trissim/OpenMFD/docs/source/api/export.rst

Export Module
=============

The export module provides file export and conversion functionality.

.. currentmodule:: openmfd.export

Configuration
-------------

.. automodule:: openmfd.export.config
   :members:
   :undoc-members:
   :show-inheritance:

SCAD Export
-----------

.. automodule:: openmfd.export.scad
   :members:
   :undoc-members:
   :show-inheritance:

DXF Export
----------

.. automodule:: openmfd.export.dxf
   :members:
   :undoc-members:
   :show-inheritance:

STL Export
----------

.. automodule:: openmfd.export.stl
   :members:
   :undoc-members:
   :show-inheritance:

File Naming
-----------

.. automodule:: openmfd.export.naming
   :members:
   :undoc-members:
   :show-inheritance:

Exporter
--------

.. automodule:: openmfd.export.exporter
   :members:
   :undoc-members:
   :show-inheritance:
