trissim/OpenMFD/docs/source/api/geometry.rst

Geometry Module
===============

The geometry module provides primitives and patterns for creating microfluidic device components.

.. currentmodule:: openmfd.geometry

Types and Measurements
----------------------

.. automodule:: openmfd.geometry.types
   :members:
   :undoc-members:
   :show-inheritance:

Primitives
----------

.. automodule:: openmfd.geometry.primitives
   :members:
   :undoc-members:
   :show-inheritance:

Wells
-----

.. automodule:: openmfd.geometry.wells
   :members:
   :undoc-members:
   :show-inheritance:

Channels
--------

.. automodule:: openmfd.geometry.channels
   :members:
   :undoc-members:
   :show-inheritance:

Chambers
--------

.. automodule:: openmfd.geometry.chambers
   :members:
   :undoc-members:
   :show-inheritance:

Positioning
-----------

.. automodule:: openmfd.geometry.positioning
   :members:
   :undoc-members:
   :show-inheritance:
