trissim/OpenMFD/docs/source/examples/custom_device.rst

Custom Devices
==============

Examples of custom device designs.

(Content to be added)
