trissim/OpenMFD/docs/source/examples/gradient_device.rst

Gradient Devices
================

Examples of gradient generation devices.

(Content to be added)
