trissim/OpenMFD/docs/source/examples/multi_well_plate.rst

Multi-Well Plates
=================

Examples of multi-well plate devices.

(Content to be added)
