trissim/OpenMFD/docs/source/examples/two_compartment.rst

Two-Compartment Devices
=======================

Examples of two-compartment microfluidic devices.

(Content to be added)
