trissim/OpenMFD/docs/source/api/index.rst

API Reference
=============

Complete API reference for OpenMFD.

.. toctree::
   :maxdepth: 2

   geometry
   devices
   export
   core
   utils

Modules
-------

.. autosummary::
   :toctree: _autosummary
   :recursive:

   openmfd.geometry
   openmfd.devices
   openmfd.export
   openmfd.core
   openmfd.utils
