trissim/OpenMFD/papers/mfd_platform/paper.md

# Manuscript source moved

The sole editable manuscript is [manuscript.md](manuscript.md). This historical
path is retained as a pointer; edit the canonical source, not this file.

Read the latest paired and combined documents under [current](current/), or see
[the paper guide](README.md) for building and preserved history.
