trissim/OpenMFD/papers/mfd_platform/prior_art_table.md

# Table 1. Prior art: multiscale microfluidic fabrication strategies (microfeatures + tall wells)

| Approach | Micro-scale features | Macro wells / tall structures | Plate / automation compatibility | What it typically costs you | Representative refs |
|---|---|---|---|---|---|
| Conventional PDMS soft lithography + manual punching | SU-8 photolithography (µm-scale channels) | Biopsy punch after casting | Limited by manual post-processing; punching becomes the throughput bottleneck | Manual labor, variability, edge defects, hard to scale to 96-well | (baseline approach; see e.g., Taylor et al., 2005) |
| CO₂ laser micromachining of PDMS | Maskless laser ablation; practical widths generally >100 µm | Laser-ablated reservoirs/wells/channels | Serial process; not ideal for dense plate arrays | Limited resolution and non-ideal cross-sections; thermal artifacts | Holle et al., 2007 |
| Micro–macro hybrid master via milling + hot embossing | Hot embossing for microfeatures | PMMA milled macrostructures (mm-scale) | Can replicate PDMS masters in quantity (not inherently plate-format) | Requires hot embosser + milling; multi-master workflow | Park et al., 2010 |
| Thick SU-8 molding + photolithography (single material) | Photolithography on molded SU-8 surface | Millimeter structures molded from 3D-printed master via PDMS mold | Demonstrated as micro-to-mm “seamless” structures (not plate workflows) | Surface roughness can degrade lithography; multi-step SU-8 handling | Tamura & Suzuki, 2019 |
| Direct 3D printing of PDMS onto photolithographic master (“printed soft lithography”) | Photolithographic master for microchannels | Printed PDMS walls/compartments | Removes punching for certain architectures; not inherently microtiter plate-format | Requires PDMS-printing hardware (bioprinter/extrusion) and ink tuning | Kajtez et al., 2020 |
| Aligned SLA printing onto patterned chips | SU-8 lithography on diced chips | SLA-printed micro/macro 3D features | Chip-scale alignment; not wafer-scale or plate-scale workflows | Requires dicing + alignment fixtures; first-layer overcure effects | Pan et al., 2022 |
| 3D-printed inserts bonded to SU-8 (lock-and-key) | SU-8 photolithography for microfeatures | Tall 3D-printed inserts + epoxy bonding | Works for open reservoirs; scaling limited by manual insert handling | Metal printing cost/availability; manual placement effort | Ristola et al., 2019 |
| Hard-plastic microtiter microfluidic plates (industrial) | Hot-embossed microchannels in COC | CNC-milled wells/compartments + fusion bonding | ANSI/SLAS compatible; automation-friendly | Requires specialized tooling/processes; not typical academic fab | Moll et al., 2024 |
| Commercial microfluidic titer plates (proprietary) | Proprietary | Proprietary | High-throughput, plate footprint | Limited design freedom; cost; opaque fab details | Spijkers et al., 2021 (OrganoPlate) |
| **This work: wafer-bonded resin well inserts + SU-8 microfeatures (with OpenMFD design rules)** | SU-8/SUEX photolithography for µm-scale microfeatures | Resin-printed well inserts adhesively bonded to wafer mold; wells formed during casting (no punching) | ANSI/SLAS footprint; demonstrated with HCS imaging + autofocus (Opera Phenix, ImageXpress) | Requires reliable bonding workflow + final mold insulation (e.g., parylene coating) | **This work** |
