trissim/OpenMFD/papers/mfd_platform/supplementary/Supplementary_Table_S1_pin_z_variability.md

# Supplementary Table S1. Resin-insert pin-height variation across a 96-position array

Each pin height was measured individually with a micrometer across one 8 × 12 resin-insert array (rows A-H, columns 1-12; *n* = 96). Values are reported in millimeters (mm) and as deviations from the mean in micrometers (µm).

- Mean height: **5.551 mm**
- Standard deviation: **26.7 µm**
- Minimum / maximum height: **5.483 mm** (H12) / **5.599 mm** (A3, A4, and A6)
- Difference between tallest and shortest pins: **116 µm**

## S1A. Measured pin heights (mm)

| Row | 1 | 2 | 3 | 4 | 5 | 6 | 7 | 8 | 9 | 10 | 11 | 12 |
|---|---|---|---|---|---|---|---|---|---|---|---|---|
| A | 5.567 | 5.588 | 5.599 | 5.599 | 5.591 | 5.599 | 5.598 | 5.598 | 5.597 | 5.596 | 5.581 | 5.562 |
| B | 5.557 | 5.588 | 5.591 | 5.591 | 5.592 | 5.588 | 5.593 | 5.592 | 5.592 | 5.591 | 5.587 | 5.562 |
| C | 5.555 | 5.556 | 5.555 | 5.563 | 5.563 | 5.556 | 5.560 | 5.557 | 5.560 | 5.560 | 5.558 | 5.555 |
| D | 5.549 | 5.552 | 5.552 | 5.555 | 5.552 | 5.552 | 5.549 | 5.552 | 5.549 | 5.552 | 5.550 | 5.545 |
| E | 5.543 | 5.546 | 5.549 | 5.550 | 5.547 | 5.547 | 5.548 | 5.544 | 5.544 | 5.543 | 5.536 | 5.532 |
| F | 5.522 | 5.531 | 5.548 | 5.544 | 5.540 | 5.540 | 5.543 | 5.542 | 5.536 | 5.531 | 5.528 | 5.522 |
| G | 5.519 | 5.528 | 5.542 | 5.543 | 5.536 | 5.535 | 5.538 | 5.538 | 5.532 | 5.529 | 5.521 | 5.501 |
| H | 5.499 | 5.516 | 5.525 | 5.525 | 5.521 | 5.520 | 5.529 | 5.517 | 5.517 | 5.503 | 5.495 | 5.483 |

## S1B. Deviation from mean (µm)

| Row | 1 | 2 | 3 | 4 | 5 | 6 | 7 | 8 | 9 | 10 | 11 | 12 |
|---|---|---|---|---|---|---|---|---|---|---|---|---|
| A | +16.2 | +37.2 | +48.2 | +48.2 | +40.2 | +48.2 | +47.2 | +47.2 | +46.2 | +45.2 | +30.2 | +11.2 |
| B | +6.2 | +37.2 | +40.2 | +40.2 | +41.2 | +37.2 | +42.2 | +41.2 | +41.2 | +40.2 | +36.2 | +11.2 |
| C | +4.2 | +5.2 | +4.2 | +12.2 | +12.2 | +5.2 | +9.2 | +6.2 | +9.2 | +9.2 | +7.2 | +4.2 |
| D | -1.8 | +1.2 | +1.2 | +4.2 | +1.2 | +1.2 | -1.8 | +1.2 | -1.8 | +1.2 | -0.8 | -5.8 |
| E | -7.8 | -4.8 | -1.8 | -0.8 | -3.8 | -3.8 | -2.8 | -6.8 | -6.8 | -7.8 | -14.8 | -18.8 |
| F | -28.8 | -19.8 | -2.8 | -6.8 | -10.8 | -10.8 | -7.8 | -8.8 | -14.8 | -19.8 | -22.8 | -28.8 |
| G | -31.8 | -22.8 | -8.8 | -7.8 | -14.8 | -15.8 | -12.8 | -12.8 | -18.8 | -21.8 | -29.8 | -49.8 |
| H | -51.8 | -34.8 | -25.8 | -25.8 | -29.8 | -30.8 | -21.8 | -33.8 | -33.8 | -47.8 | -55.8 | -67.8 |
