trissim/OpenMFD/papers/mfd_platform/figures/final_drop/Fig3_bonding_fixture/draft_figure.odp

Inserts are printed in position aligned with the wafer and then covered in slow setting epoxy

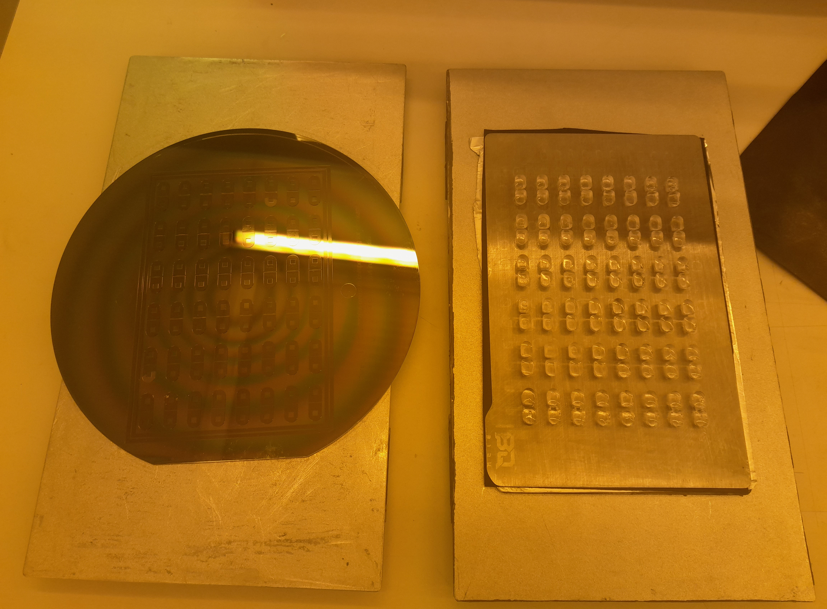
[picture p5: figure]

Aligned and Clamped Assembly

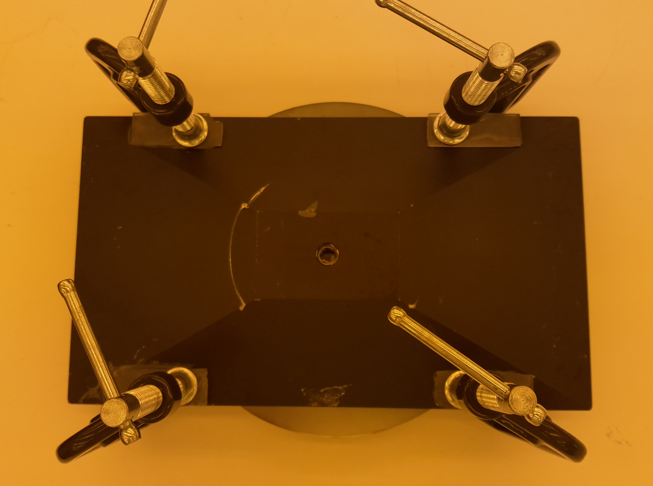
[picture p6: figure]

Sealing the glue between the wafer and inserts allows excess epoxy to be washed by immersion in acetone

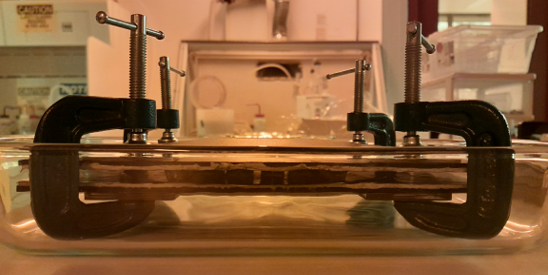
[picture p7: figure]
