trissim/OpenMFD/papers/mfd_platform/figures/final_drop/Fig4_mold_casts_package/draft_figure.odp

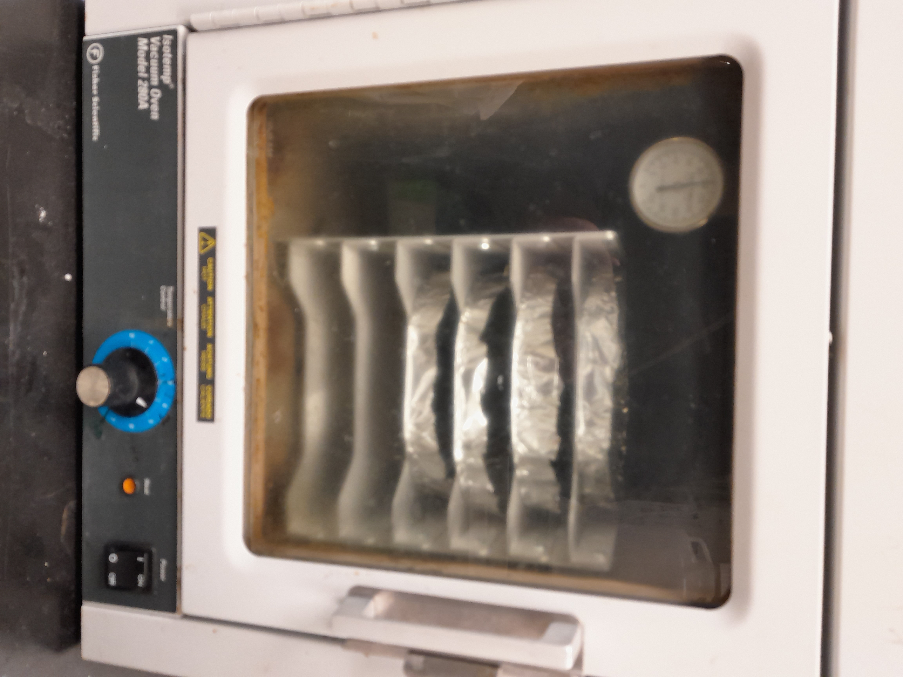
[picture p8: figure]
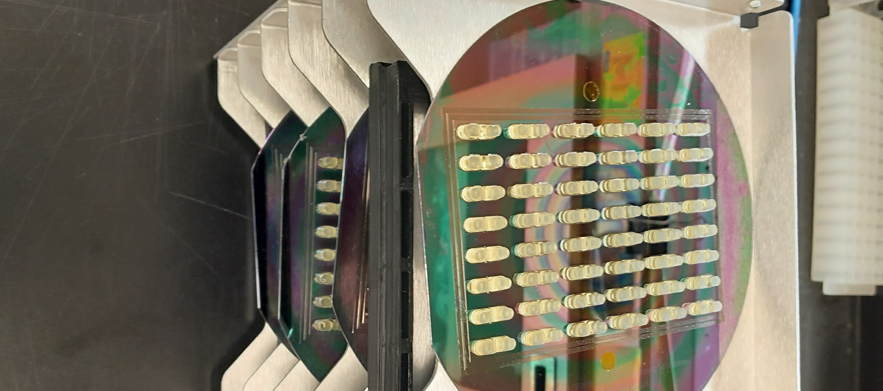
[picture p9: figure]
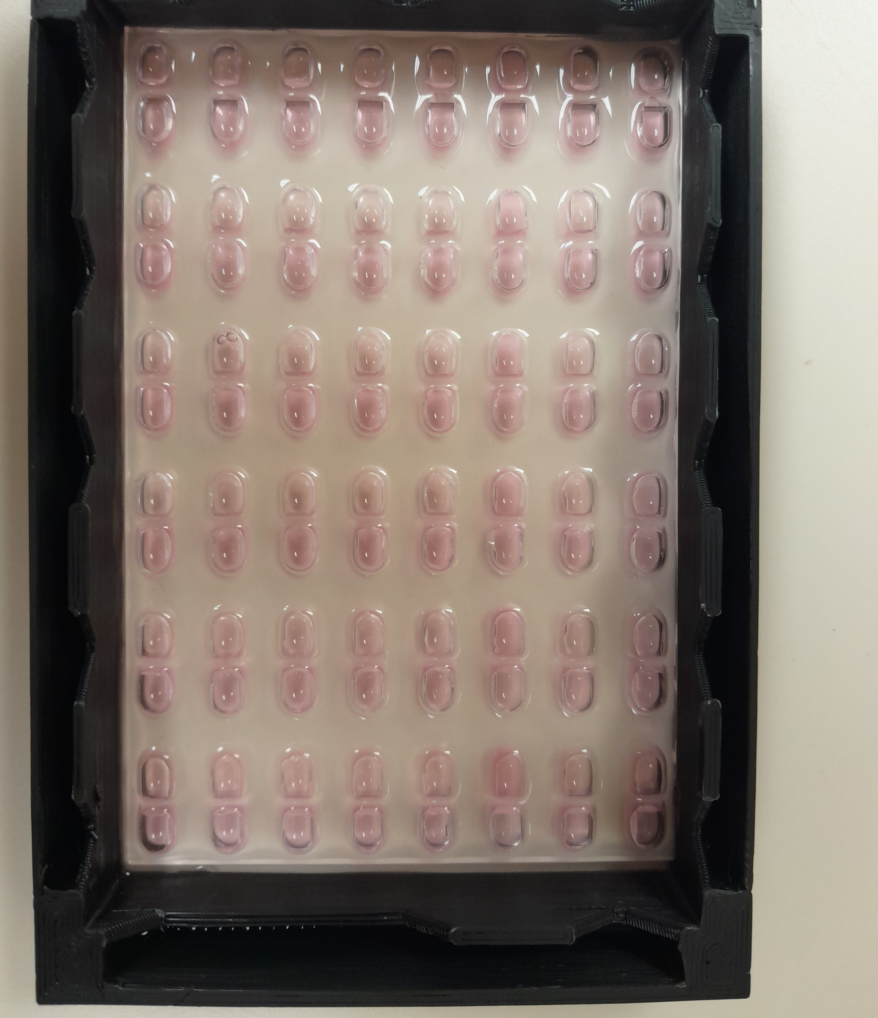
[picture p10: figure]

Unified mold and custom rack for parallel fabrication of devices

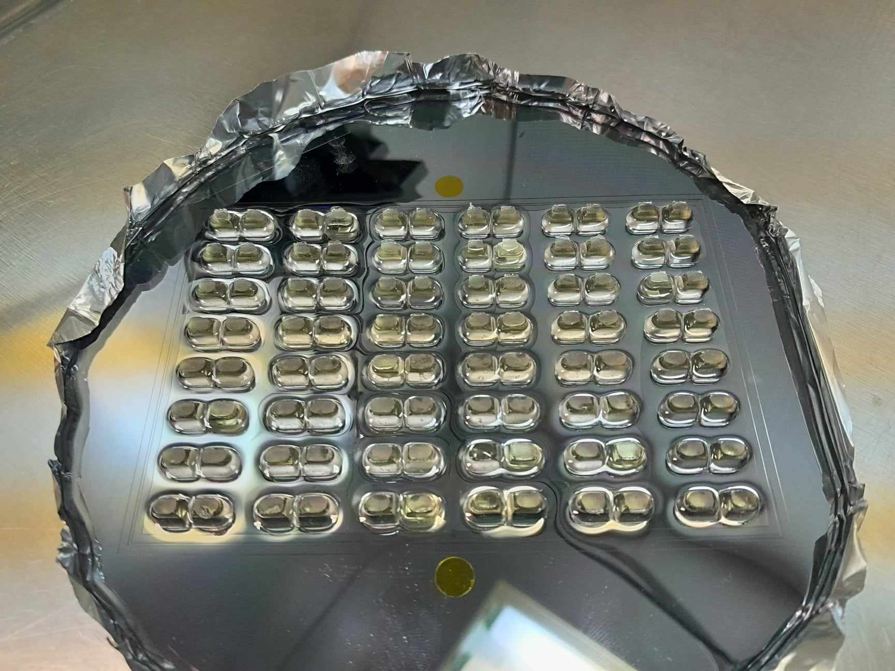
[picture p11: figure]

Assembly with 3D printed plates and glue

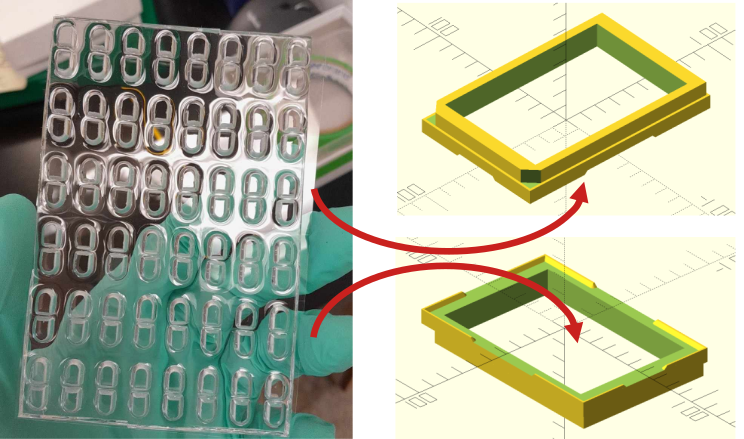
[picture p12: figure]
