trissim/OpenMFD/papers/mfd_platform/figures/final_drop/Fig6_generalizability/draft_figure.odp

## Other High-throughput Devices for Various Assays

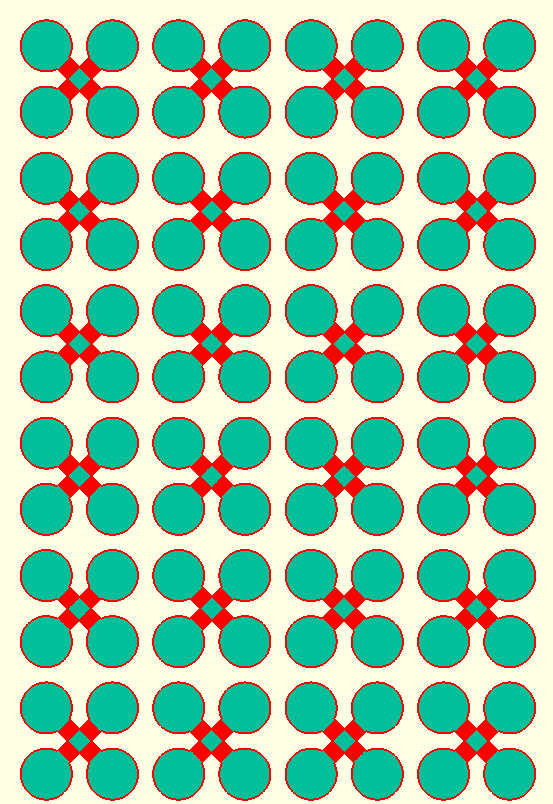
[picture p13: figure]

Myelination Assay

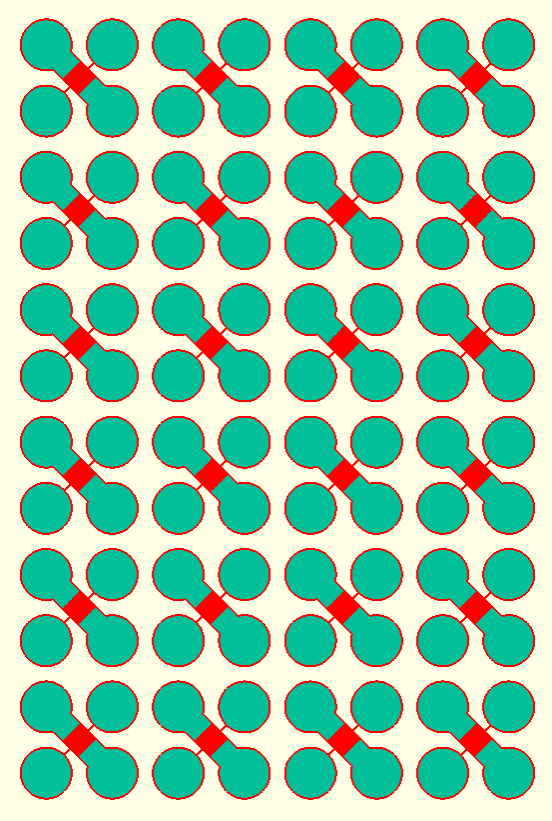
[picture p14: figure]

Axon Guidance Assay

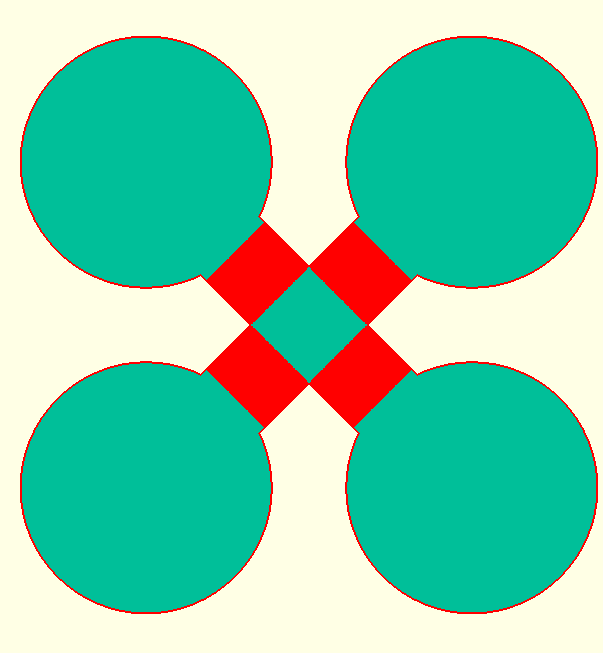
[picture p15: figure]
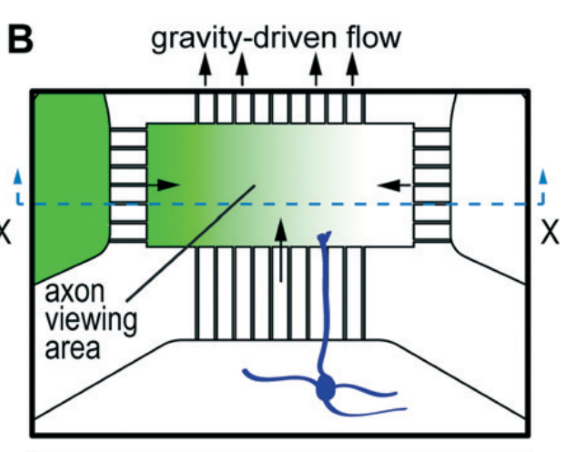
[picture p16: figure]
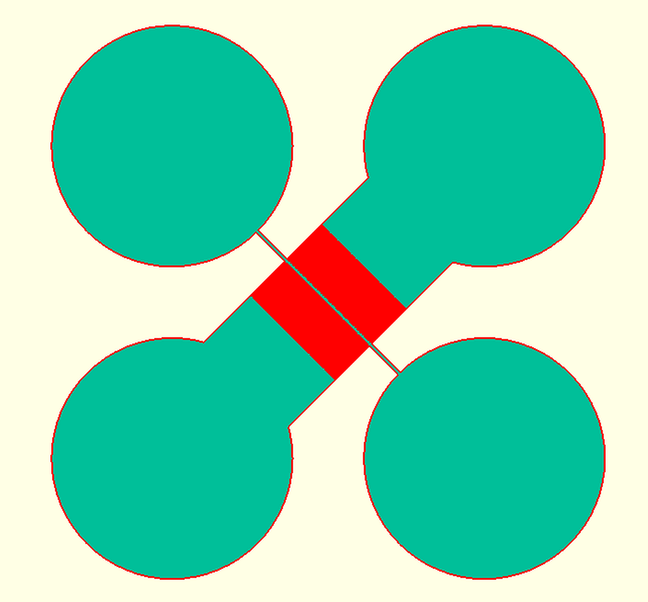
[picture p17: figure]
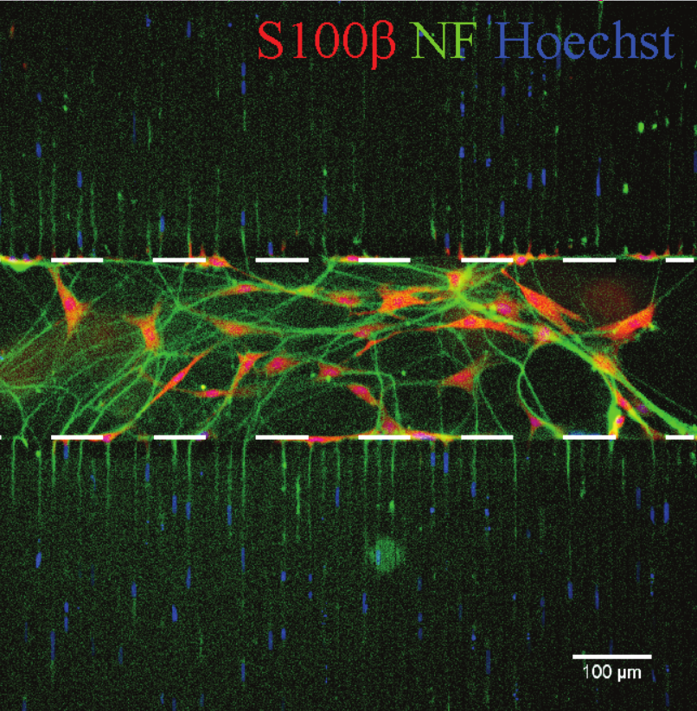
[picture p18: figure]

Oligo

Inlet

Axons

Myelin

Oligo

Outlet

Waste /

Outlet

Axons

Cue 2

Cue 1

Cell

Bodies

Cell

Bodies

<number>

Notes: - Once 96-well axotomy works → can make high-throughput device of any layouts - Recreation of published layout but transformed into high throughput version - Example of myelination assay - Example of Axon guidance assay
