trissim/OpenMFD/papers/mfd_platform/figures/final_drop/Supp_FigS1_noLP360/draft_figure.odp

SUEX 200 without 360nm Long-Pass Filter

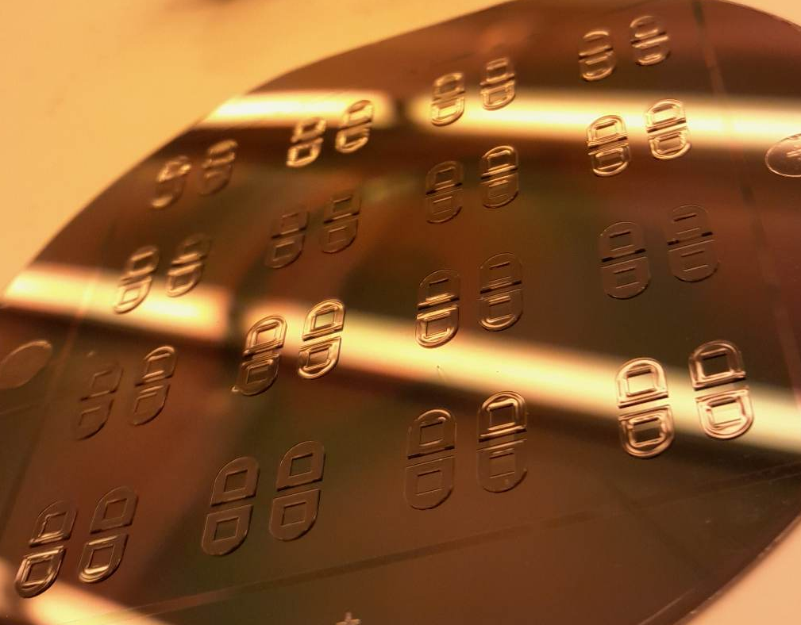
[picture p19: figure]

SUEX 200 with 360nm Long-Pass Filter

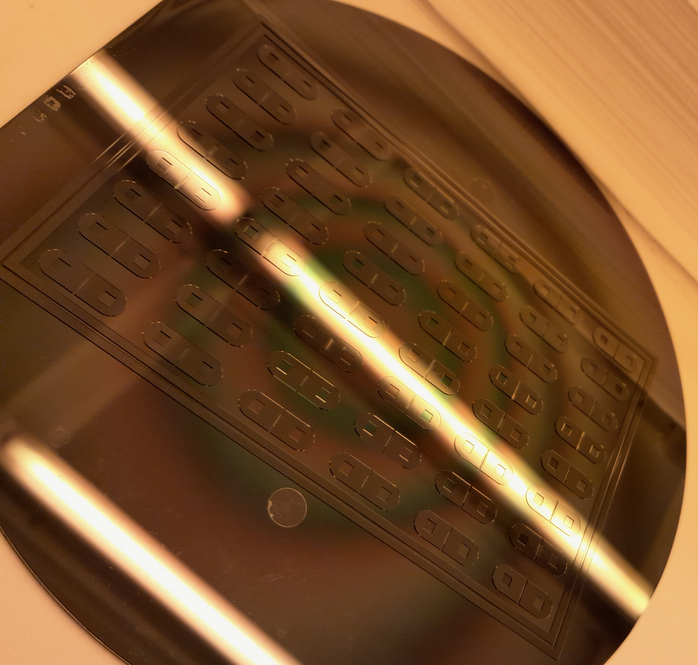
[picture p20: figure]
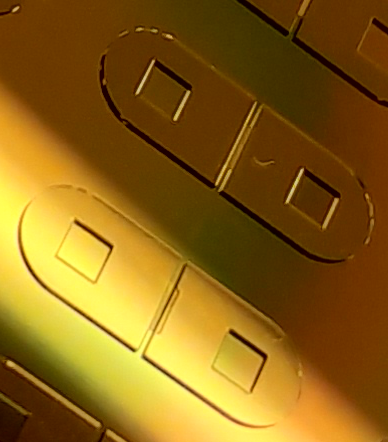
[picture p21: figure]
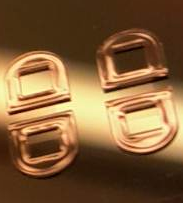
[picture p22: figure]
