trissim/OpenMFD/papers/mfd_platform/figures/rendered/mold_casts_package.pdf

# Post-mold device replication and assembly

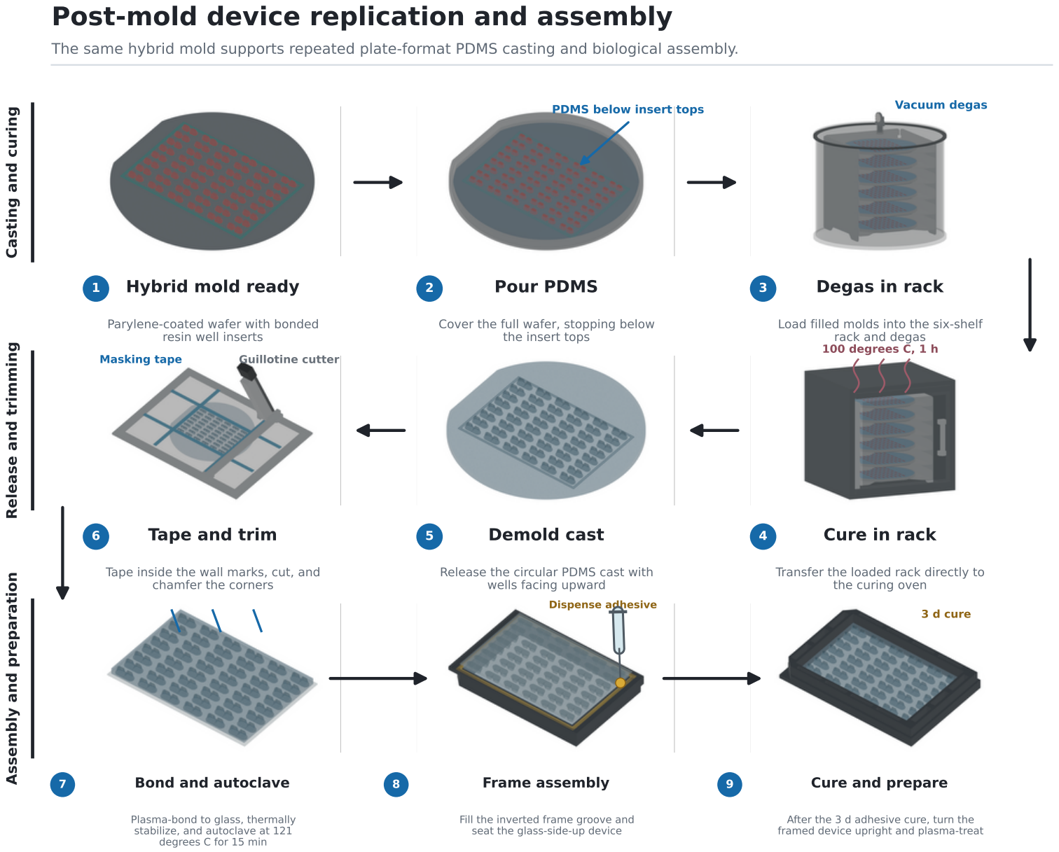
[picture p23: page 1]

The same hybrid mold supports repeated plate-format PDMS casting and biological assembly.

### Casting and curing

## Hybrid mold ready

Parylene-coated wafer with bonded resin well inserts

PDMS below insert tops

## Pour PDMS

Cover the full wafer, stopping below the insert tops

Vacuum degas

## Degas in rack

Load filled molds into the six-shelf rack and degas

### Release and trimming

Masking tape | Guillotine cutter

## Tape and trim

Tape inside the wall marks, cut, and chamfer the corners

## Demold cast

Release the circular PDMS cast with wells facing upward

100 degrees C, 1 h

## Cure in rack

Transfer the loaded rack directly to the curing oven

### Assembly and preparation

Bond and autoclave

Plasma-bond to glass, thermally stabilize, and autoclave at 121 degrees C for 15 min

Dispense adhesive

Frame assembly

Fill the inverted frame groove and seat the glass-side-up device

### 3 d cure

Cure and prepare

After the 3 d adhesive cure, turn the framed device upright and plasma-treat

1 | 2 | 3
6 | 5 | 4
7 | 8 | 9
