trissim/OpenMFD/papers/mfd_platform/figures/final_drop/Supp_FigS2_delamination/draft_figure.odp

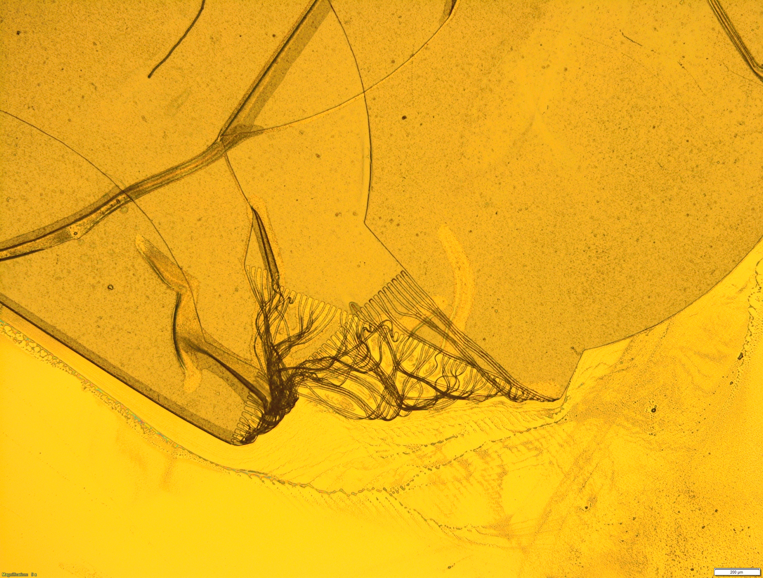
[picture p24: figure]
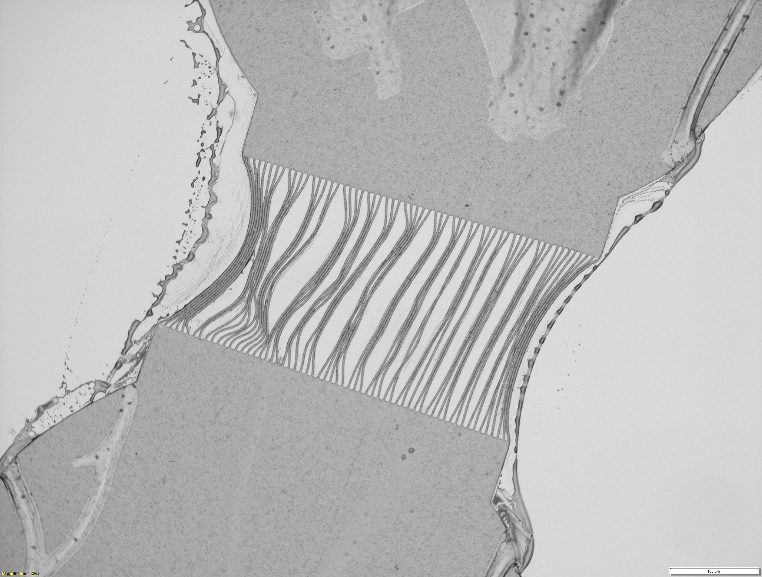
[picture p25: figure]
