trissim/OpenMFD/papers/mfd_platform/pin_z_variability.xlsx

Raw Data | 1 | 2 | 3 | 4 | 5 | 6 | 7 | 8 | 9 | 10 | 11 | 12
1 | 5.567 | 5.588 | 5.599 | 5.599 | 5.591 | 5.599 | 5.598 | 5.598 | 5.597 | 5.596 | 5.581 | 5.562
2 | 5.557 | 5.588 | 5.591 | 5.591 | 5.592 | 5.588 | 5.593 | 5.592 | 5.592 | 5.591 | 5.587 | 5.562
3 | 5.555 | 5.556 | 5.555 | 5.563 | 5.563 | 5.556 | 5.56 | 5.557 | 5.56 | 5.56 | 5.558 | 5.555
4 | 5.549 | 5.552 | 5.552 | 5.555 | 5.552 | 5.552 | 5.549 | 5.552 | 5.549 | 5.552 | 5.55 | 5.545
5 | 5.543 | 5.546 | 5.549 | 5.55 | 5.547 | 5.547 | 5.548 | 5.544 | 5.544 | 5.543 | 5.536 | 5.532
6 | 5.522 | 5.531 | 5.548 | 5.544 | 5.54 | 5.54 | 5.543 | 5.542 | 5.536 | 5.531 | 5.528 | 5.522
7 | 5.519 | 5.528 | 5.542 | 5.543 | 5.536 | 5.535 | 5.538 | 5.538 | 5.532 | 5.529 | 5.521 | 5.501
8 | 5.499 | 5.516 | 5.525 | 5.525 | 5.521 | 5.52 | 5.529 | 5.517 | 5.517 | 5.503 | 5.495 | 5.483
 |  | Average of pin heights |  |  | 5.552409091
Diff. From Avg | 1 | 2 | 3 | 4 | 5 | 6 | 7 | 8 | 9 | 10 | 11 | 12
1 | 0.01459090909 | 0.03559090909 | 0.04659090909 | 0.04659090909 | 0.03859090909 | 0.04659090909 | 0.04559090909 | 0.04559090909 | 0.04459090909 | 0.04359090909 | 0.02859090909 | 0.009590909091
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
