trissim/OpenMFD/papers/mfd_platform/figures/final_drop/Fig2_insert_bonding/old/Fig2_insert_alignment/README.md

# Retired Insert Alignment Source

This source folder is no longer rendered into the main manuscript. Its OpenMFD design-rule and insert STL panels moved to `Fig1_openmfd_design`.

Dump here:
- CAD render of one insert
- CAD or DXF view of matching lock geometry
- any panel showing the 1.85 mm pin into the 2.0 mm square hole
- any tolerance callout graphic

Best fit for this figure:
- lock-and-key geometry
- alignment concept
- clearance / tolerance explanation

Avoid using only a bench photo here; this figure should mainly be geometry-driven.
