trissim/OpenMFD/papers/mfd_platform/figures/final_drop/Fig2_insert_bonding/old/Fig2_insert_alignment/draft_figure.odp

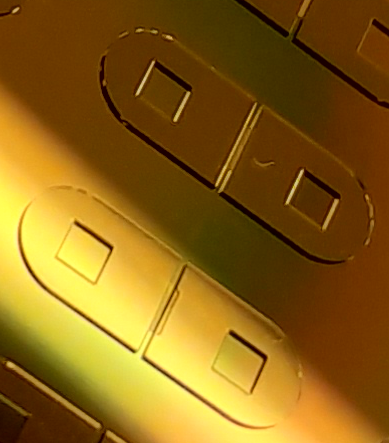
[picture p26: figure]

2 mm

2 mm

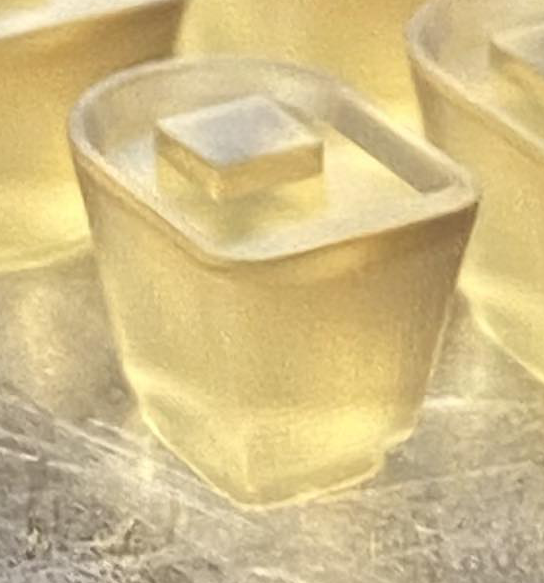
[picture p27: figure]

1.85 mm

1.85 mm

3D Printed Inserts

Cavity to Align Insert Pins

Assemble Pins on Wafer

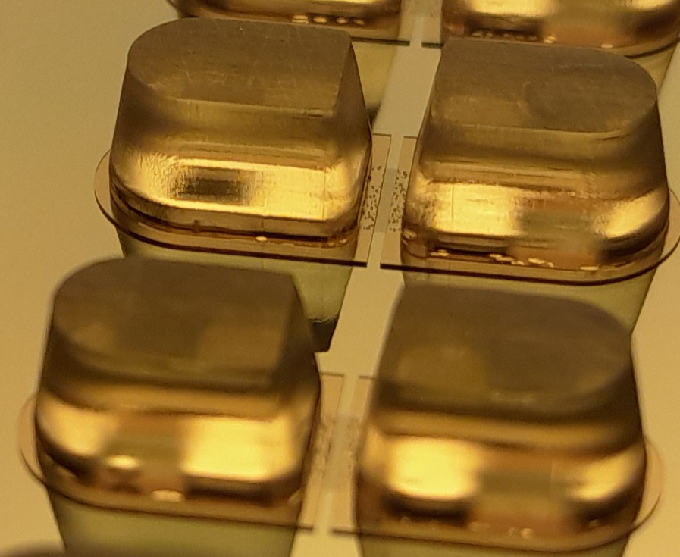
[picture p28: figure]

+

=
