trissim/OpenMFD/papers/mfd_platform/figures/final_drop/Fig2_insert_bonding/old/Fig2_insert_alignment/draft_figure_old.odp

2 mm

2 mm


1.85 mm

1.85 mm

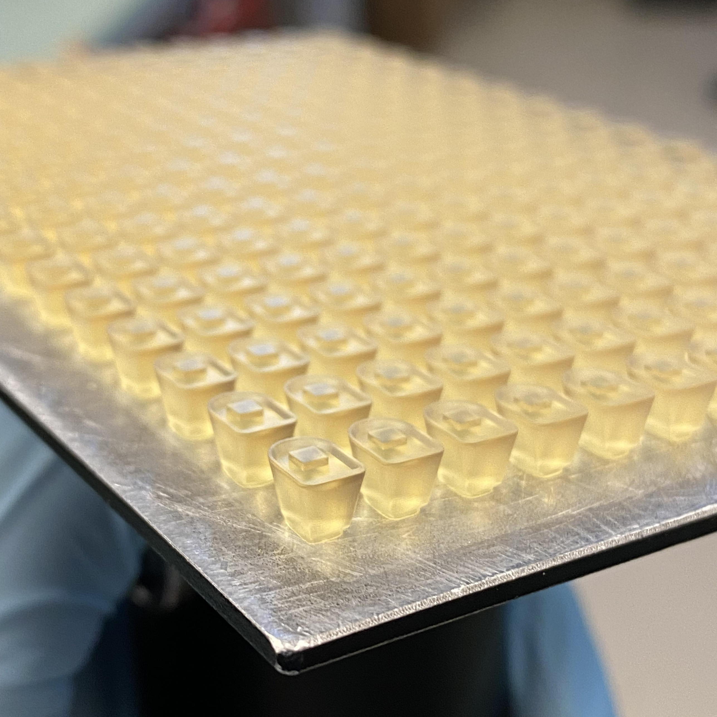
[picture p29: figure]

3D Printed Inserts

Cavity to Align Insert Pins

Assemble Pins on Wafer


+

=

<number>

Mervi Ristola et al 2019 J. Micromech. Microeng. 29 065009

Confidential

Notes: - integrating well in mold saves time, more accurate, reproducible - SU-8 is practically limited to 200um as resin, 500um as dry sheet - Journal of Micromechanics and Microengineering paper uses steel 3D printed parts and glues on wafer with lock and key mechanism - Used affordable resin printer instead
