trissim/OpenMFD/designs/open_chamber/2compartment/devices_2compartment_multi_device.png

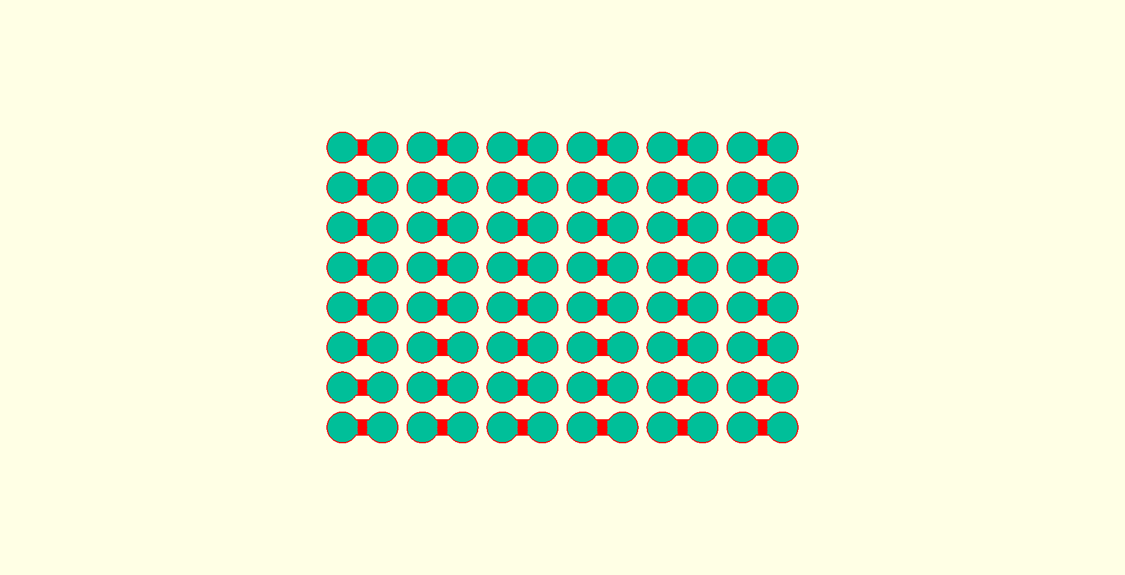
designs/open_chamber/2compartment/devices_2compartment_multi_device.png
