trissim/OpenMFD/designs/open_chamber/2compartment/devices_2compartment_single_device.png

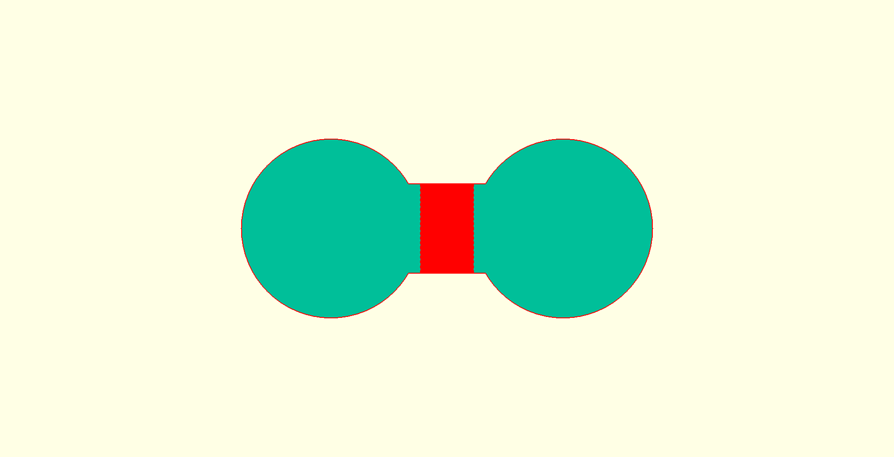
designs/open_chamber/2compartment/devices_2compartment_single_device.png
