trissim/OpenMFD/designs/open_chamber/3compartment/devices_3compartment_single_device.png

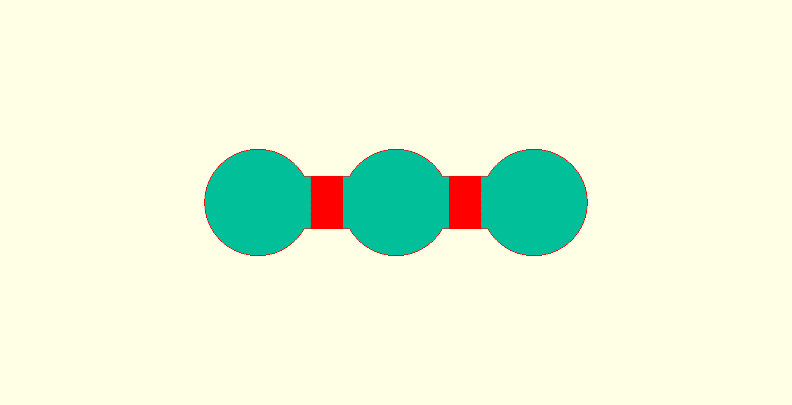
designs/open_chamber/3compartment/devices_3compartment_single_device.png
