trissim/OpenMFD/designs/open_chamber/gradient_layout/devices_closed_gradient_single_device.png

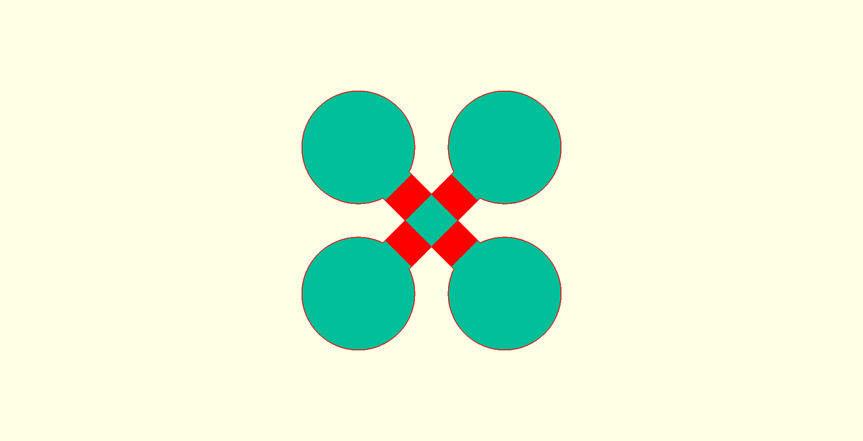
designs/open_chamber/gradient_layout/devices_closed_gradient_single_device.png
