trissim/OpenMFD/designs/open_chamber/gradient_layout/gradient_96_well_single.png

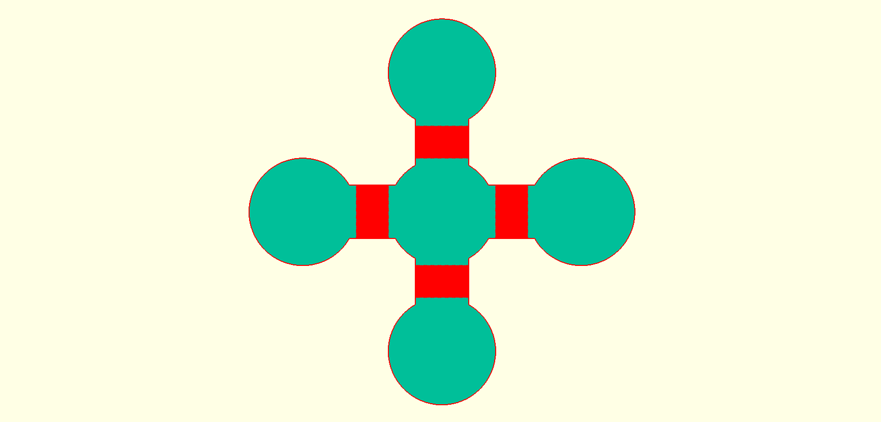
designs/open_chamber/gradient_layout/gradient_96_well_single.png
