trissim/OpenMFD/designs/open_chamber/myelination/devices_myelination_single_device.png

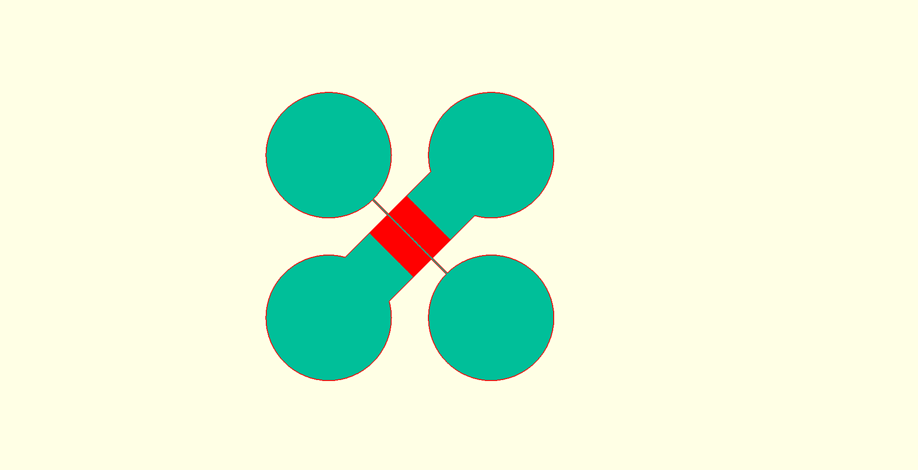
designs/open_chamber/myelination/devices_myelination_single_device.png
