trissim/OpenMFD/designs/taylor/chambers_wells_chans_1x1_units_.jpg

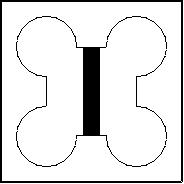
designs/taylor/chambers_wells_chans_1x1_units_.jpg
