trissim/OpenMFD/designs/taylor/chambers_wells_chans_8x12_units_.jpg

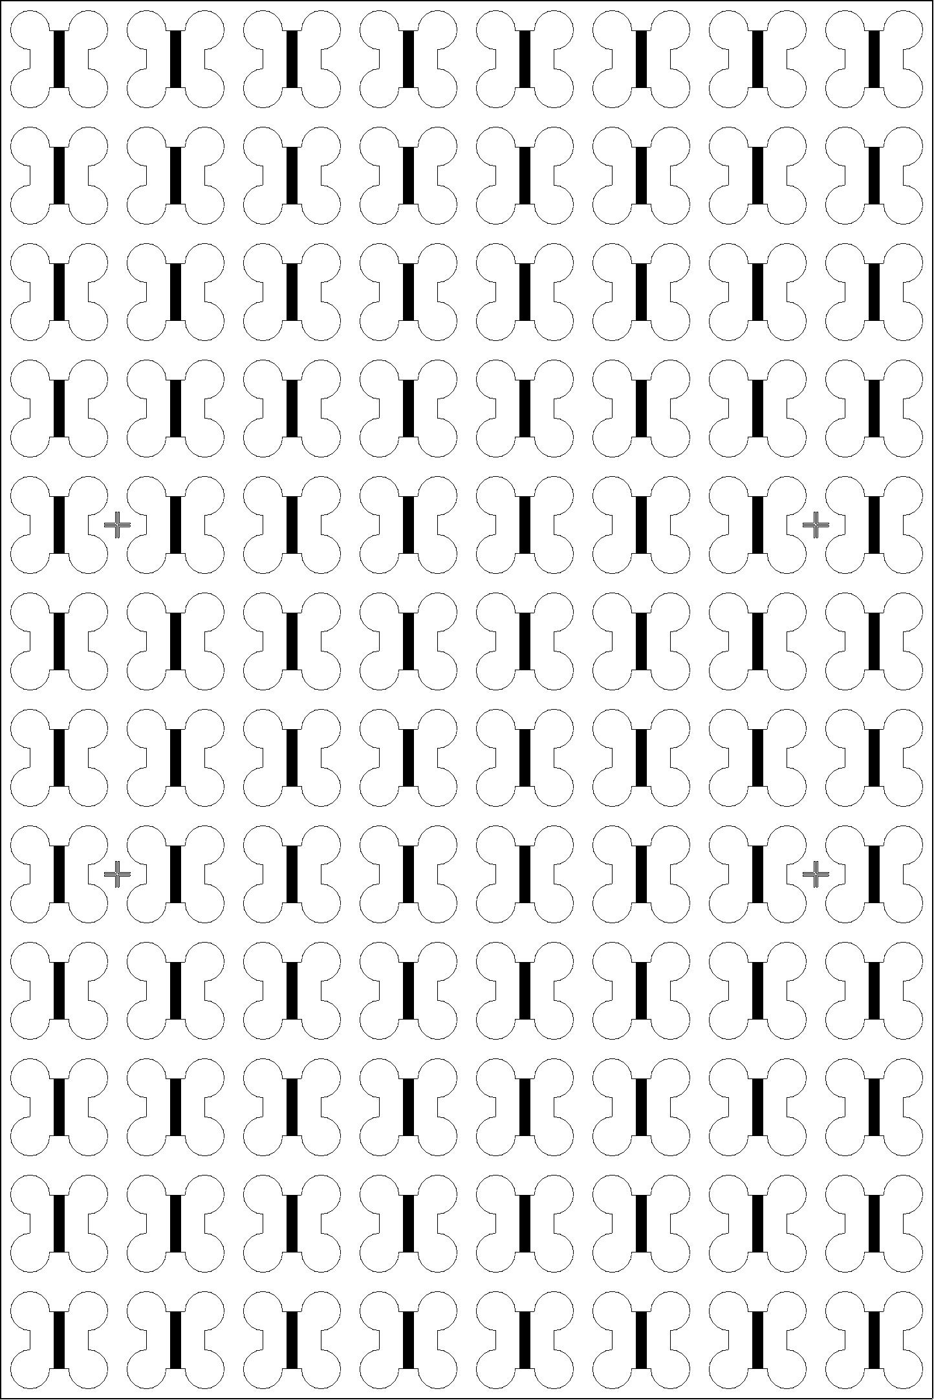
designs/taylor/chambers_wells_chans_8x12_units_.jpg
