trissim/OpenMFD/papers/mfd_platform/figures/comparisons/v25_vs_v27/2_compartment_96_well_300um_v25_vs_v27.png

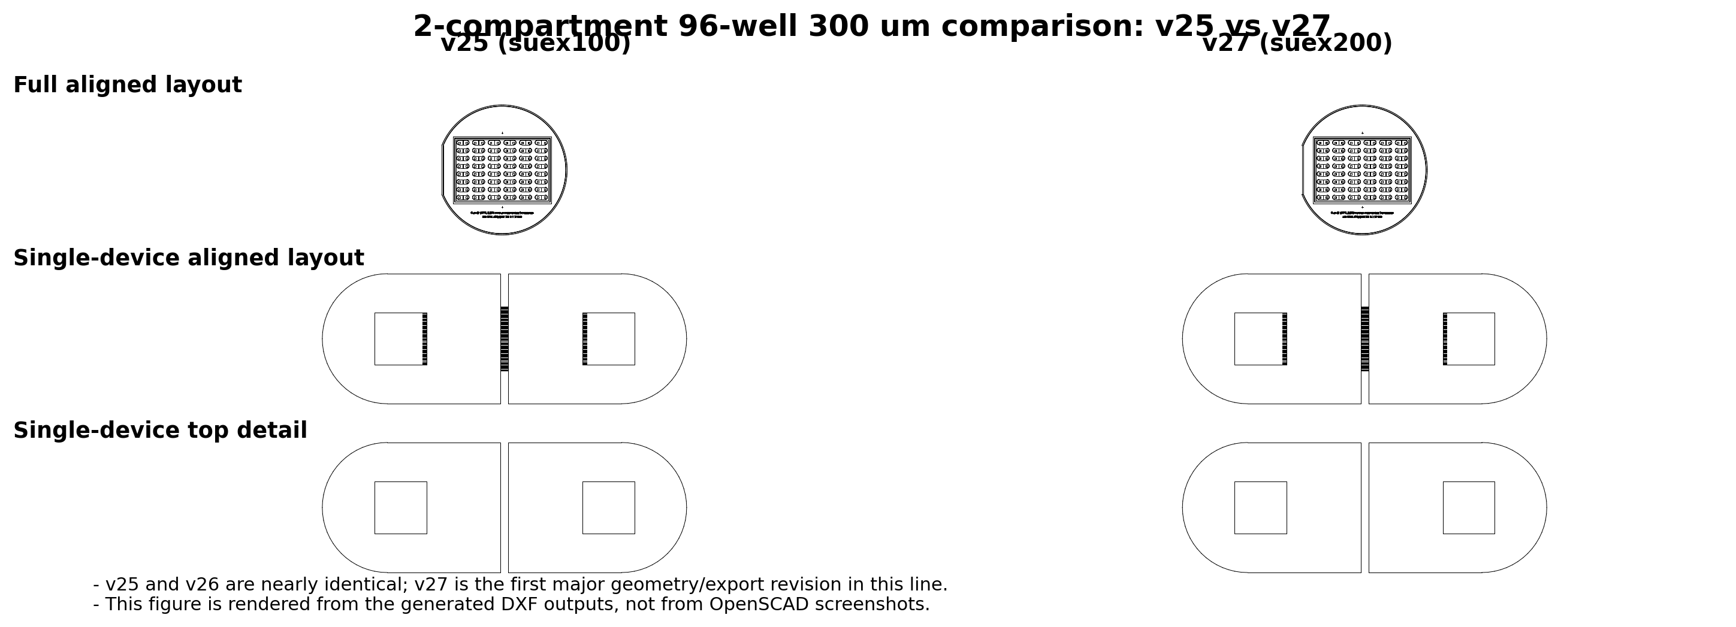
papers/mfd_platform/figures/comparisons/v25_vs_v27/2_compartment_96_well_300um_v25_vs_v27.png
