trissim/OpenMFD/papers/mfd_platform/figures/drafts/pics/4x_brightfield.png

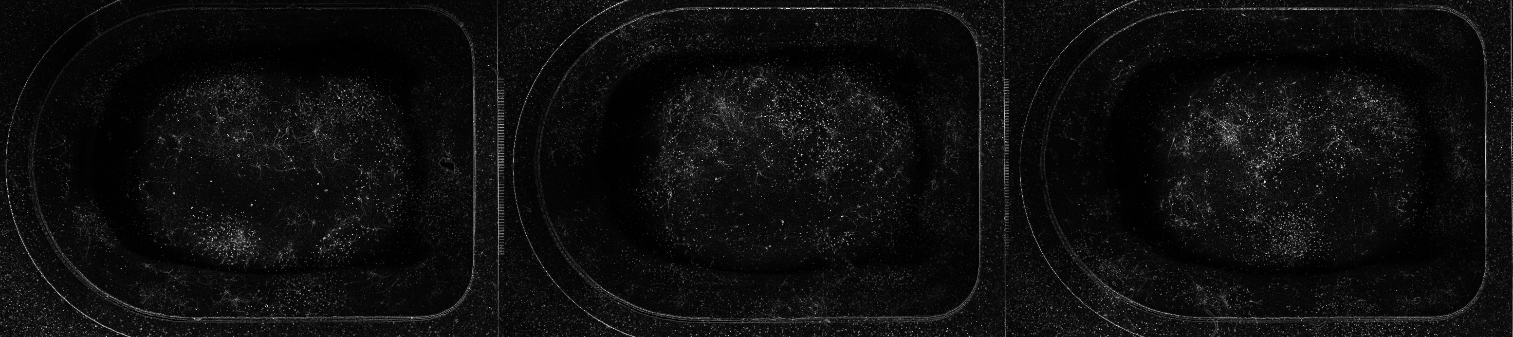
papers/mfd_platform/figures/drafts/pics/4x_brightfield.png
