trissim/OpenMFD/papers/mfd_platform/figures/drafts/pics/4x_brightfield_inv.png

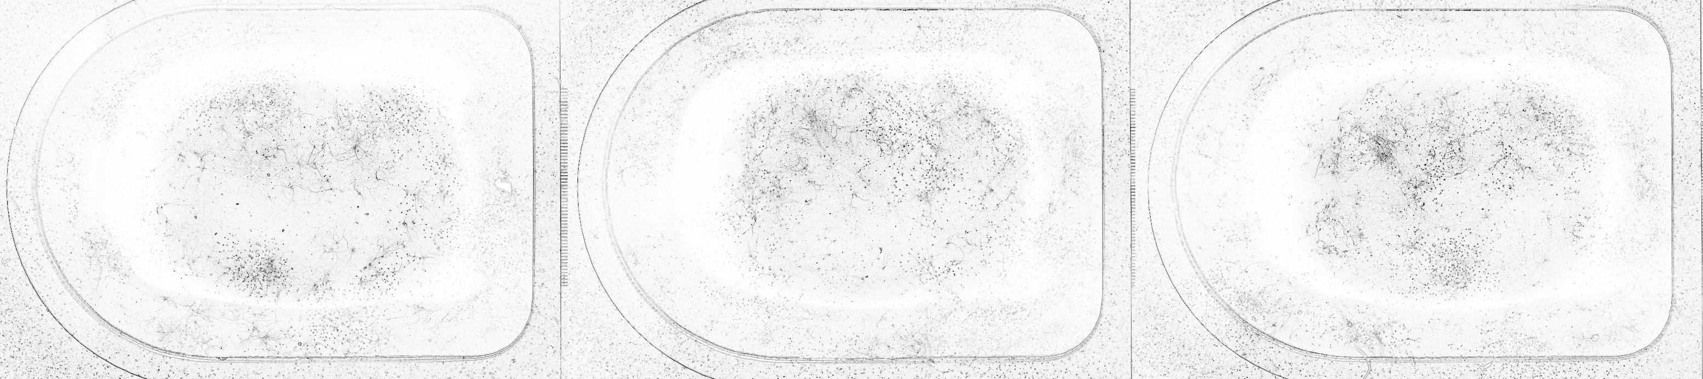
papers/mfd_platform/figures/drafts/pics/4x_brightfield_inv.png
