trissim/OpenMFD/papers/mfd_platform/figures/drafts/pics/dapi_tild_inv.tif

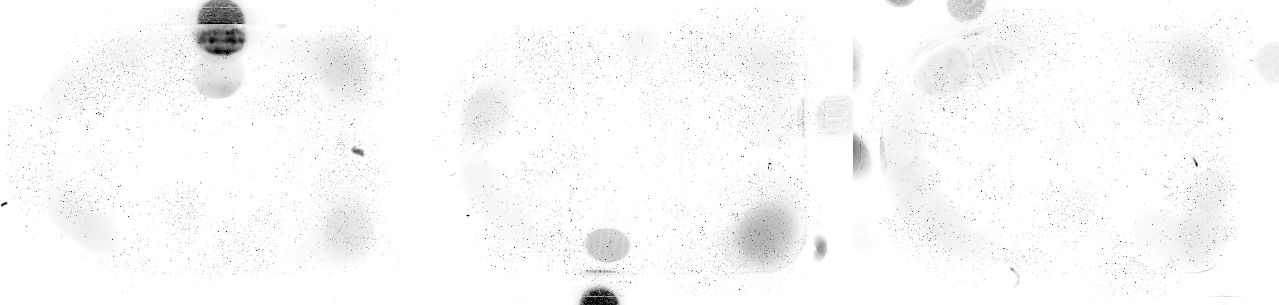
papers/mfd_platform/figures/drafts/pics/dapi_tild_inv.tif
