trissim/OpenMFD/papers/mfd_platform/figures/drafts/pics/dapi_tiled.tif

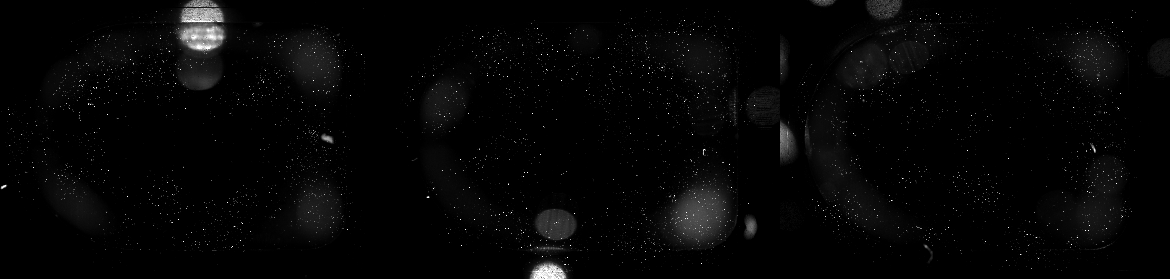
papers/mfd_platform/figures/drafts/pics/dapi_tiled.tif
