trissim/OpenMFD/papers/mfd_platform/figures/drafts/pics/dapi_zoom.tif

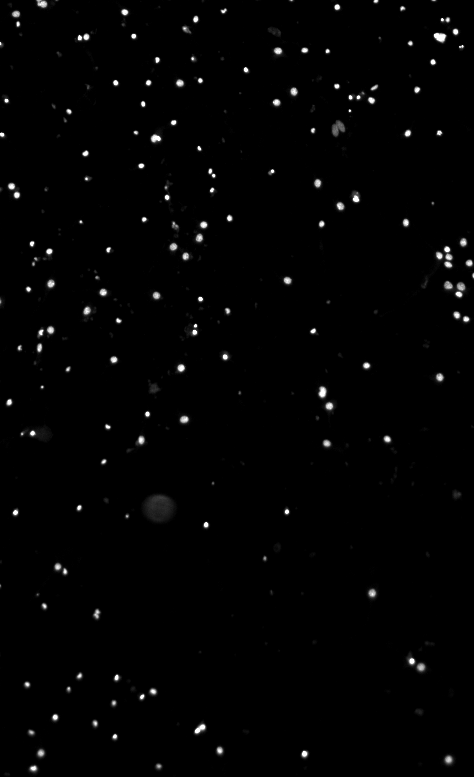
papers/mfd_platform/figures/drafts/pics/dapi_zoom.tif
