trissim/OpenMFD/papers/mfd_platform/figures/drafts/pics/E09_w2_001_bin2_background.png

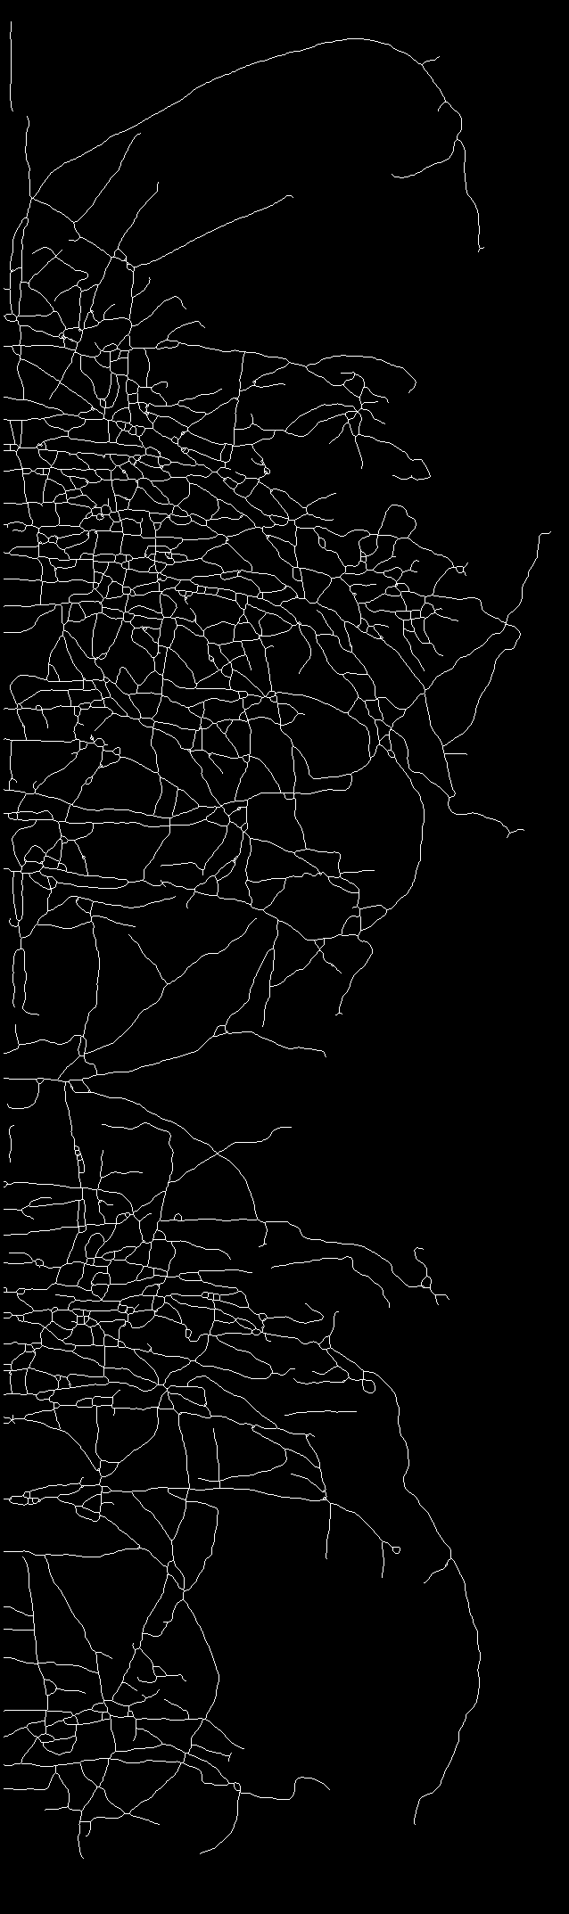
papers/mfd_platform/figures/drafts/pics/E09_w2_001_bin2_background.png
