trissim/OpenMFD/papers/mfd_platform/figures/drafts/pics/less_axons.png

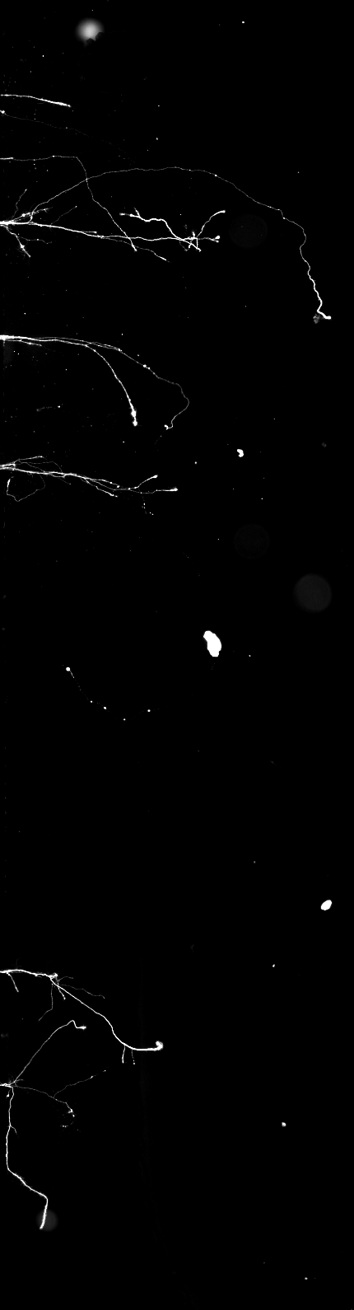
papers/mfd_platform/figures/drafts/pics/less_axons.png
