trissim/OpenMFD/papers/mfd_platform/figures/drafts/pics/less_axons_inv.png

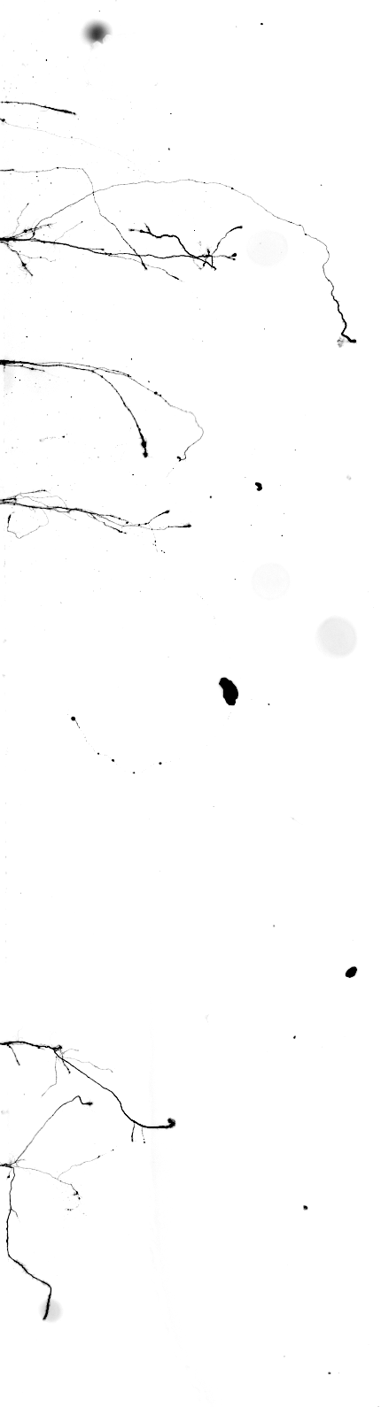
papers/mfd_platform/figures/drafts/pics/less_axons_inv.png
