trissim/OpenMFD/papers/mfd_platform/figures/drafts/pics/less_axons_trace.png

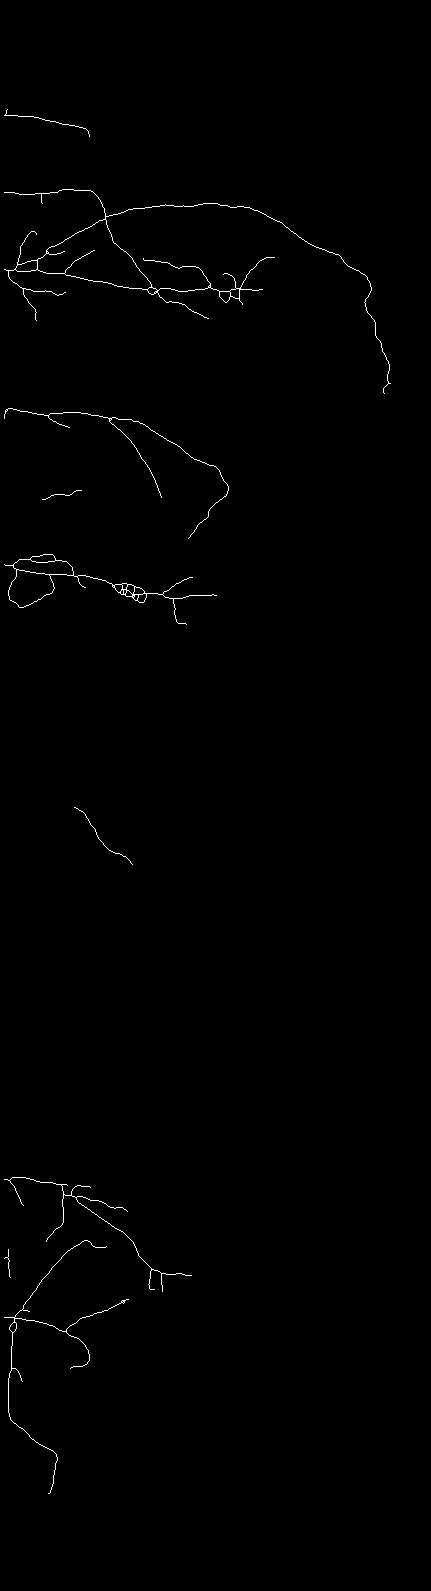
papers/mfd_platform/figures/drafts/pics/less_axons_trace.png
