trissim/OpenMFD/papers/mfd_platform/figures/drafts/pics/less_axons_trace_inv.png

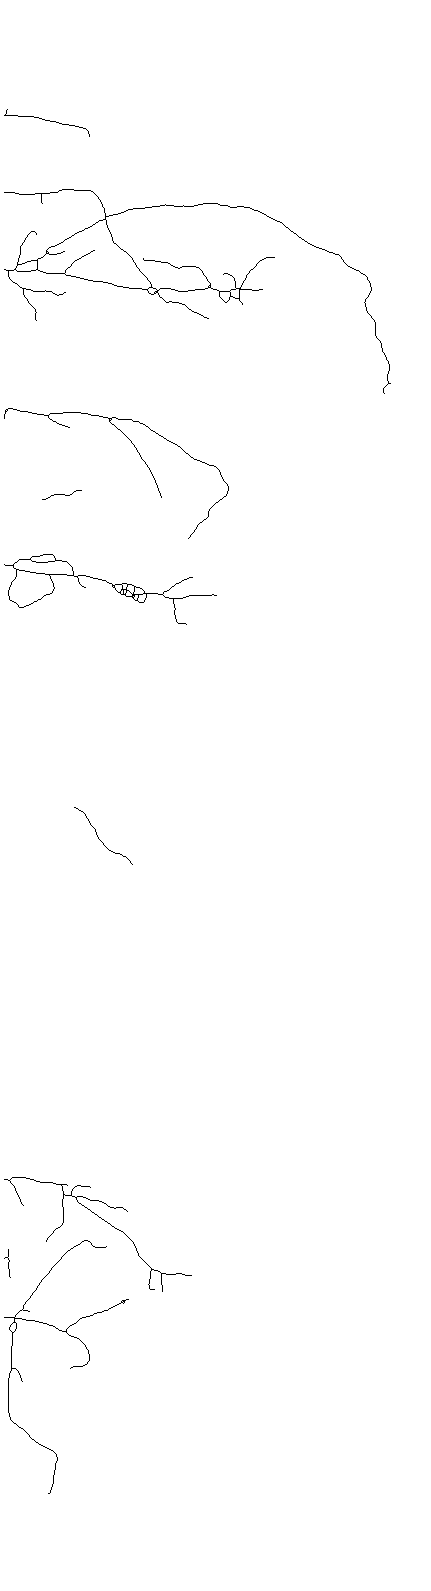
papers/mfd_platform/figures/drafts/pics/less_axons_trace_inv.png
