trissim/OpenMFD/papers/mfd_platform/figures/drafts/pics/lotsa_axons.png

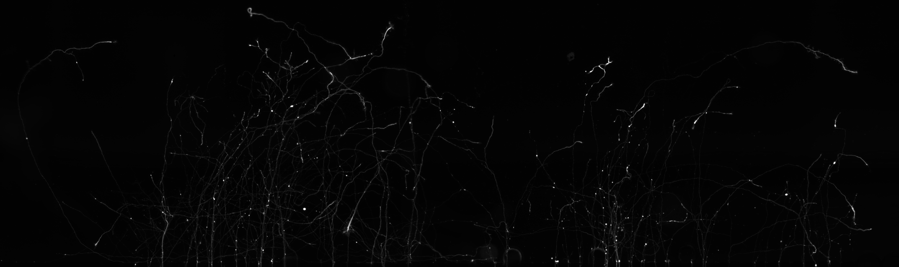
papers/mfd_platform/figures/drafts/pics/lotsa_axons.png
