trissim/OpenMFD/papers/mfd_platform/figures/drafts/pics/lotsa_axons_inv.png

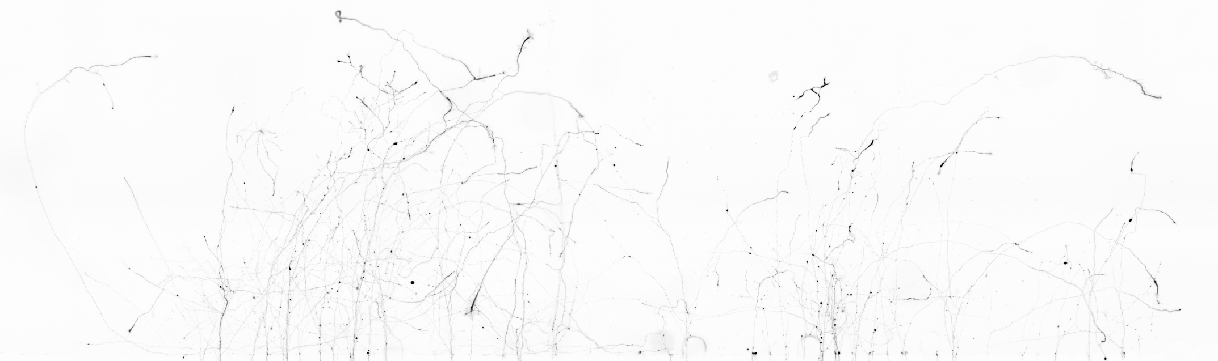
papers/mfd_platform/figures/drafts/pics/lotsa_axons_inv.png
