trissim/OpenMFD/papers/mfd_platform/figures/drafts/pics/lotsa_axons_inv_contrast.tif

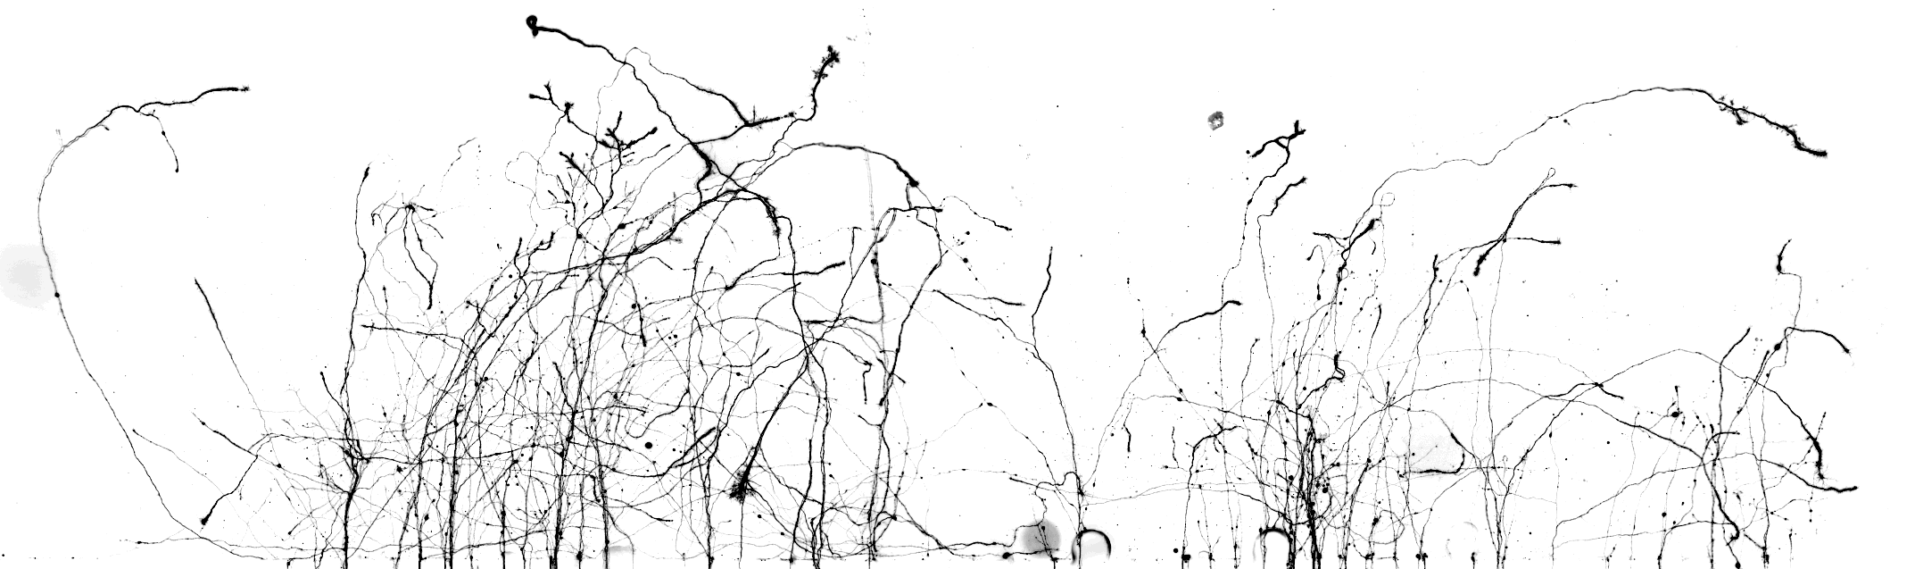
papers/mfd_platform/figures/drafts/pics/lotsa_axons_inv_contrast.tif
