trissim/OpenMFD/papers/mfd_platform/figures/final_drop/Fig1_openmfd_design/subfigures/C.png

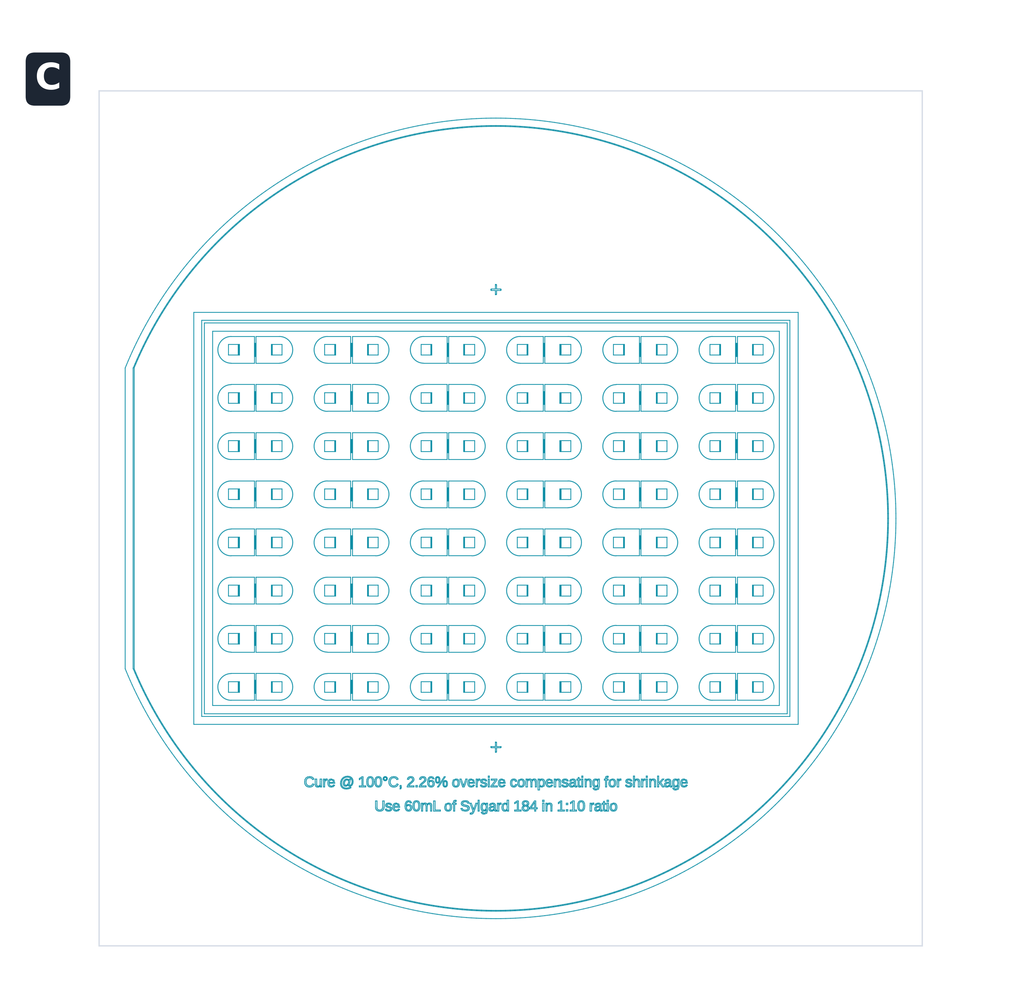
papers/mfd_platform/figures/final_drop/Fig1_openmfd_design/subfigures/C.png
