trissim/OpenMFD/papers/mfd_platform/figures/final_drop/Fig1_openmfd_design/subfigures/D.png

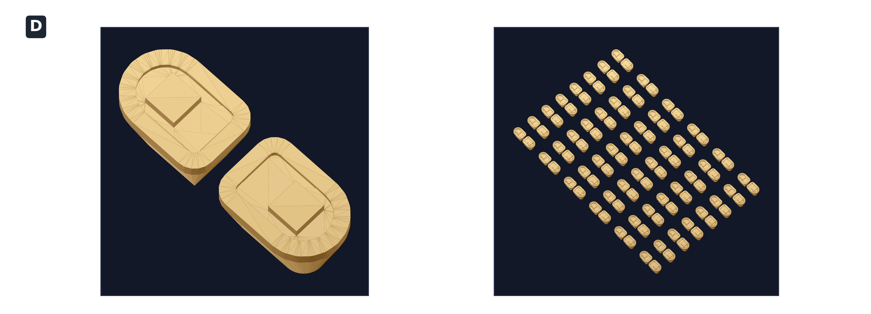
papers/mfd_platform/figures/final_drop/Fig1_openmfd_design/subfigures/D.png
