trissim/OpenMFD/papers/mfd_platform/figures/final_drop/Fig1_openmfd_design/subfigures/E.png

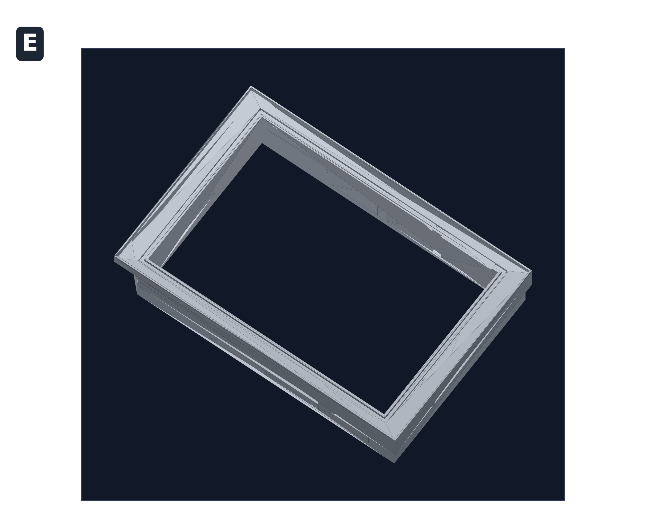
papers/mfd_platform/figures/final_drop/Fig1_openmfd_design/subfigures/E.png
