trissim/OpenMFD/papers/mfd_platform/figures/final_drop/Fig2_insert_bonding/subfigures/D.png

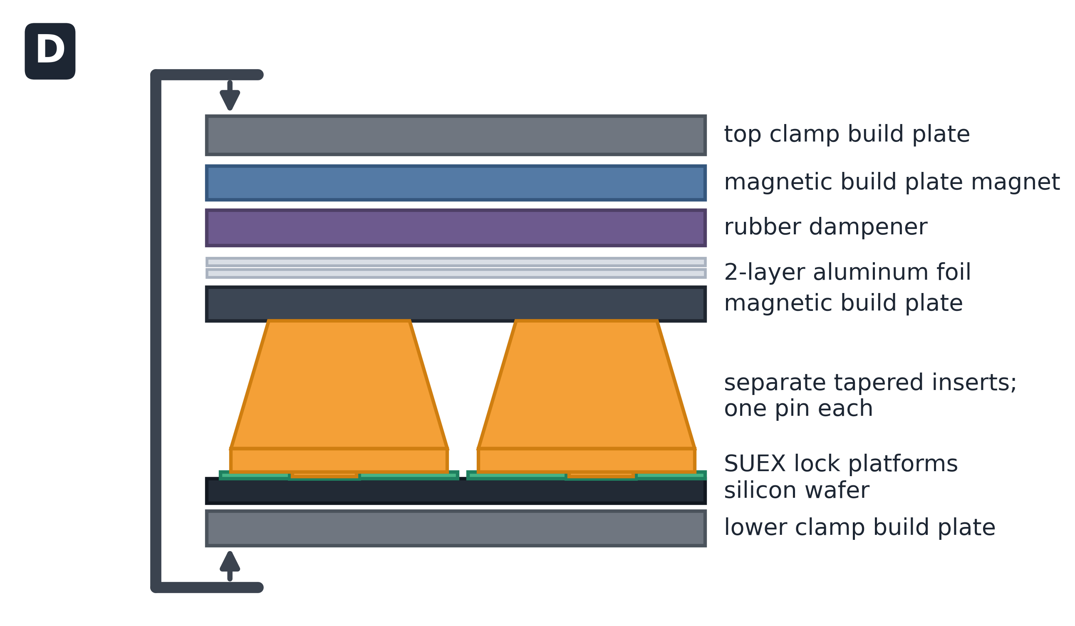
papers/mfd_platform/figures/final_drop/Fig2_insert_bonding/subfigures/D.png
