trissim/OpenMFD/papers/mfd_platform/figures/final_drop/Fig3_bonding_fixture/draft_figure.png

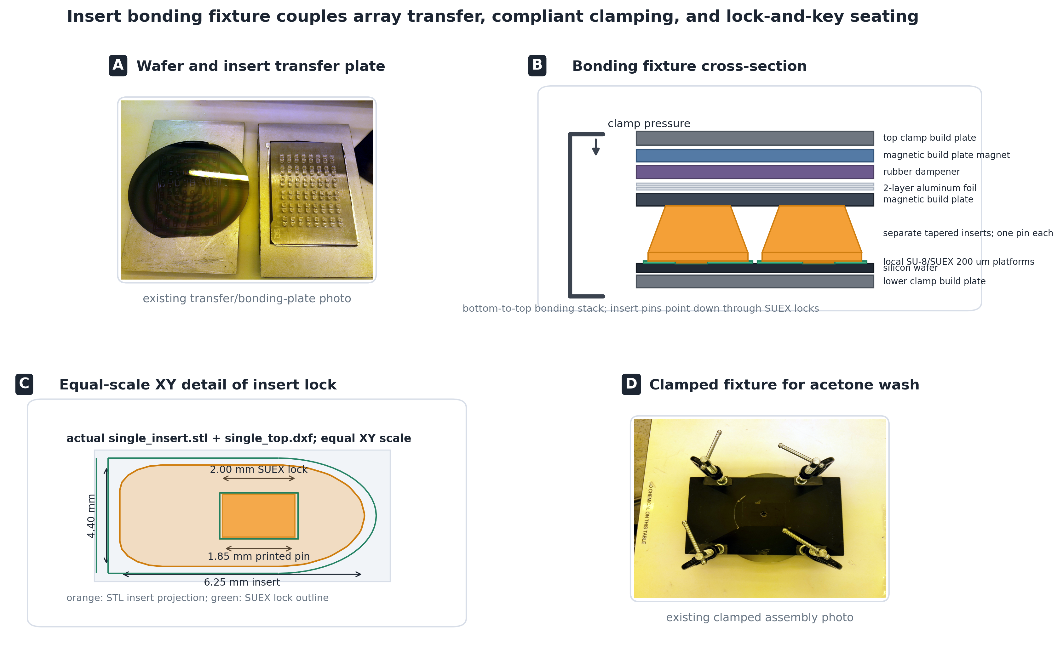
papers/mfd_platform/figures/final_drop/Fig3_bonding_fixture/draft_figure.png
