trissim/OpenMFD/papers/mfd_platform/figures/final_drop/Fig4_mold_casts_package/draft_figure.png

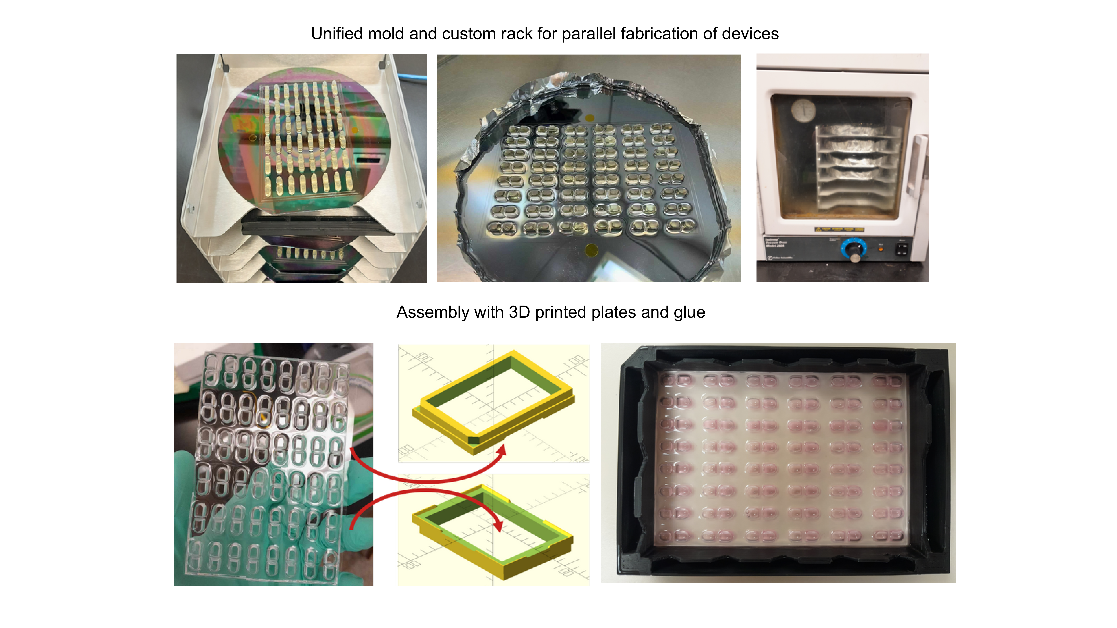
papers/mfd_platform/figures/final_drop/Fig4_mold_casts_package/draft_figure.png
