trissim/OpenMFD/papers/mfd_platform/figures/final_drop/Fig6_generalizability/subfigures/A_myelination_dxf_outputs.png

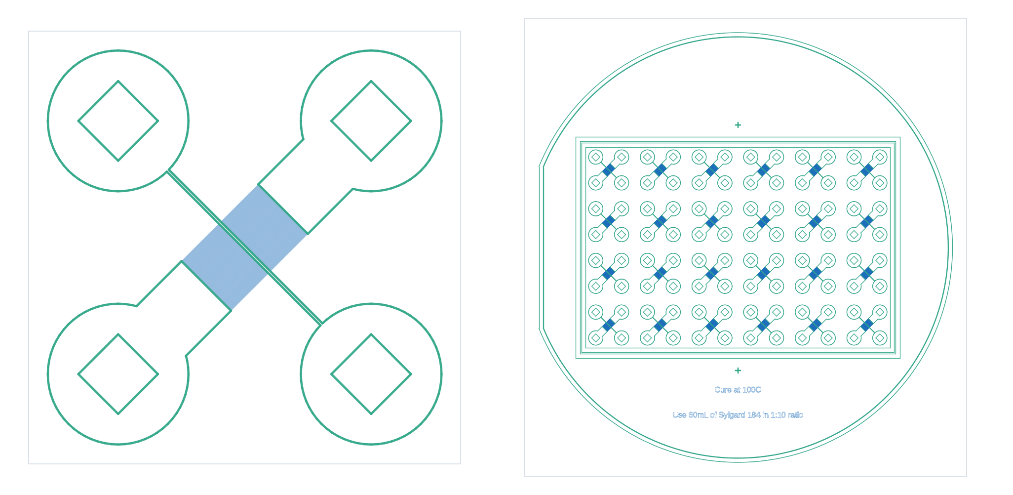
papers/mfd_platform/figures/final_drop/Fig6_generalizability/subfigures/A_myelination_dxf_outputs.png
