trissim/OpenMFD/papers/mfd_platform/figures/final_drop/Fig6_generalizability/subfigures/B_myelination_insert_outputs.png

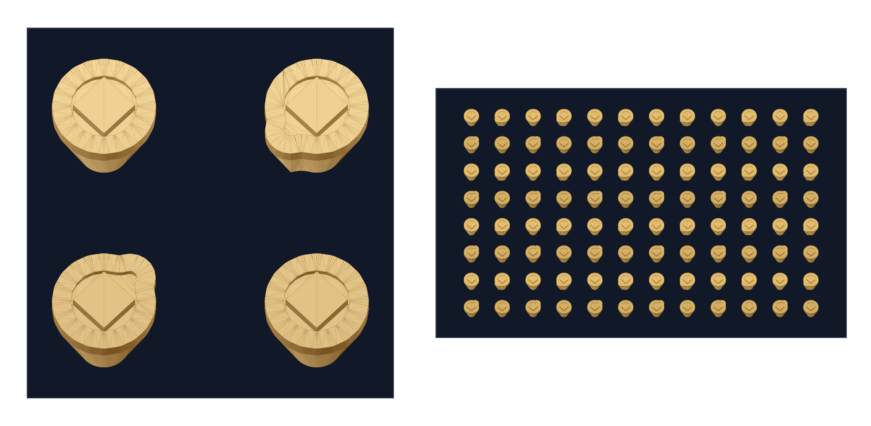
papers/mfd_platform/figures/final_drop/Fig6_generalizability/subfigures/B_myelination_insert_outputs.png
