trissim/OpenMFD/papers/mfd_platform/figures/final_drop/Fig6_generalizability/subfigures/E_three_compartment_dxf_outputs.png

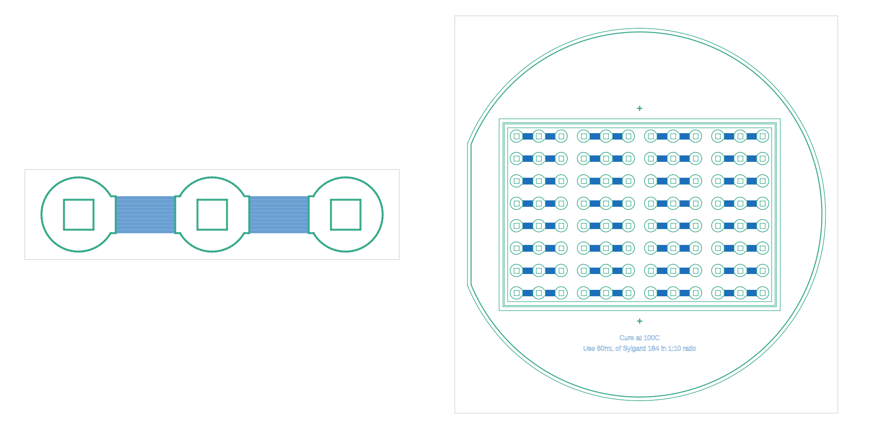
papers/mfd_platform/figures/final_drop/Fig6_generalizability/subfigures/E_three_compartment_dxf_outputs.png
