trissim/OpenMFD/papers/mfd_platform/figures/final_drop/Fig6_generalizability/subfigures/F_three_compartment_insert_outputs.png

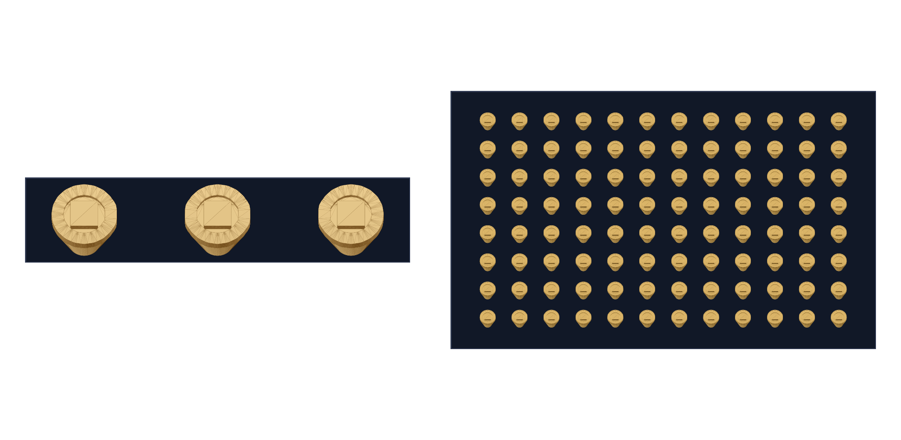
papers/mfd_platform/figures/final_drop/Fig6_generalizability/subfigures/F_three_compartment_insert_outputs.png
