trissim/OpenMFD/papers/mfd_platform/figures/final_drop/Fig6_generalizability/subfigures/individual/myelination_single_unit_dxf.png

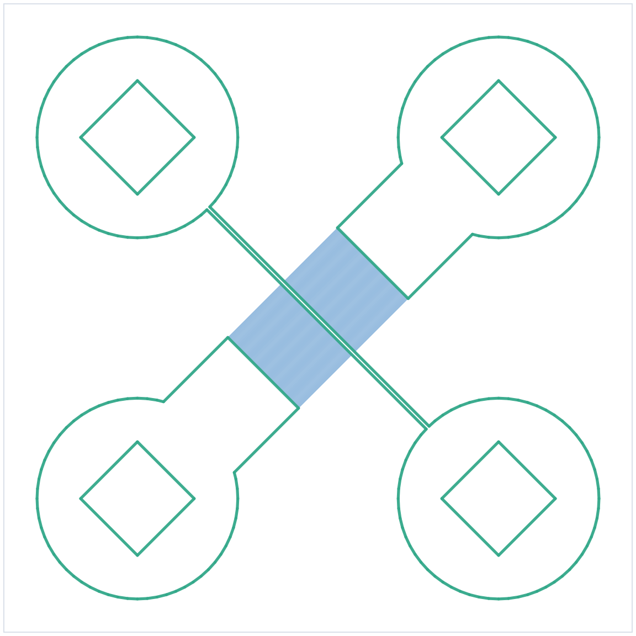
papers/mfd_platform/figures/final_drop/Fig6_generalizability/subfigures/individual/myelination_single_unit_dxf.png
