trissim/OpenMFD/papers/mfd_platform/figures/final_drop/Fig6_generalizability/subfigures/individual/three_compartment_plate_layout_dxf.png

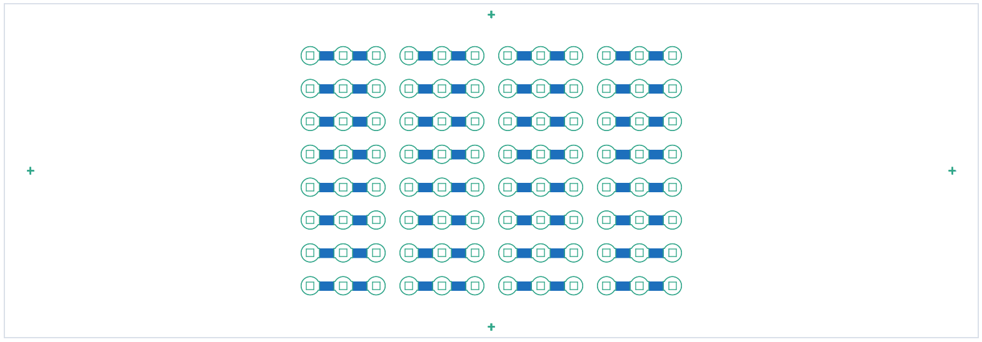
papers/mfd_platform/figures/final_drop/Fig6_generalizability/subfigures/individual/three_compartment_plate_layout_dxf.png
