trissim/OpenMFD/papers/mfd_platform/figures/final_drop/Fig6_generalizability/subfigures/individual/three_compartment_wafer_mask_dxf.png

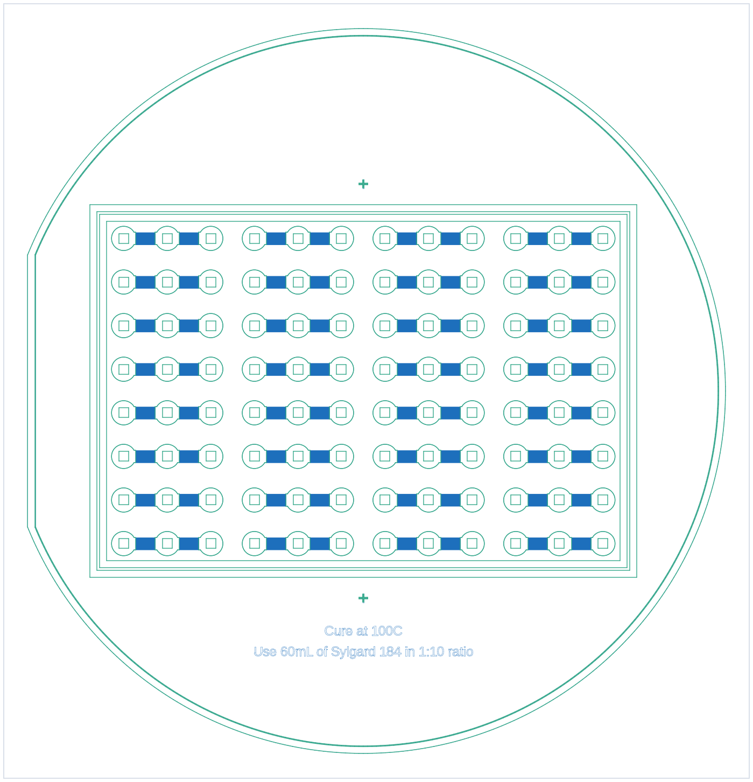
papers/mfd_platform/figures/final_drop/Fig6_generalizability/subfigures/individual/three_compartment_wafer_mask_dxf.png
