trissim/OpenMFD/papers/mfd_platform/figures/rendered_docx/mold_casts_package.png

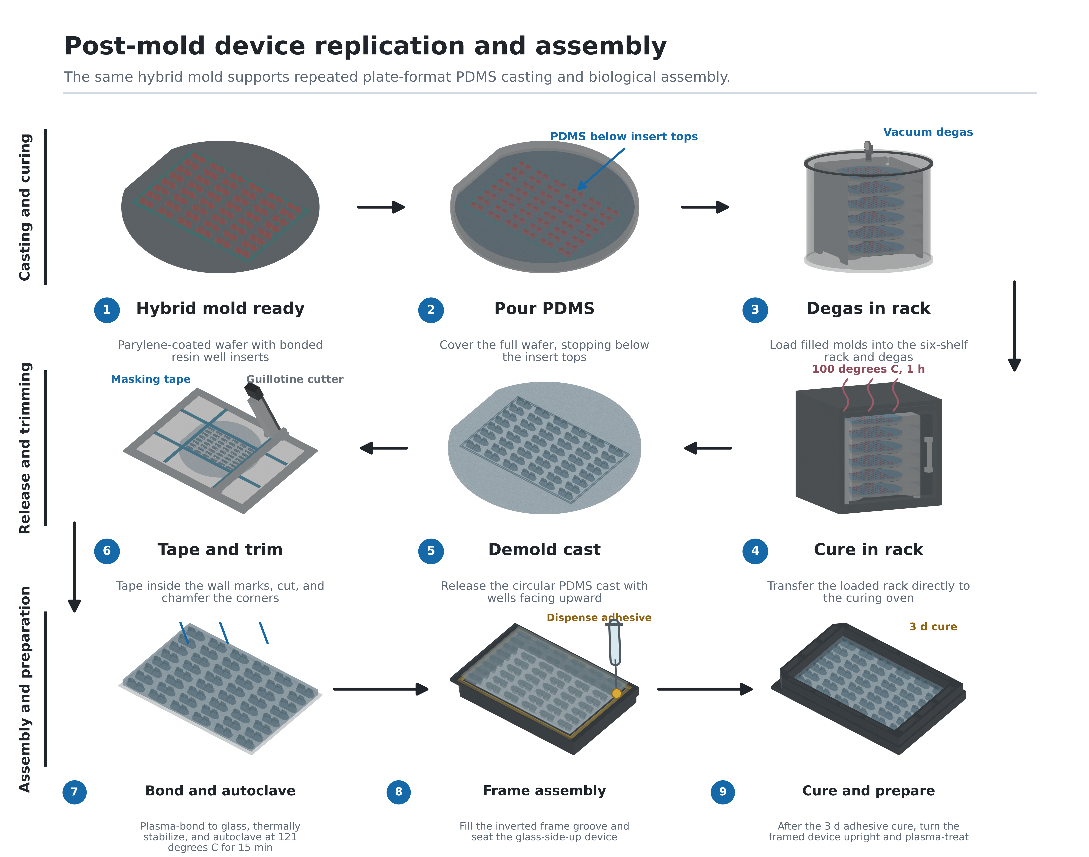
papers/mfd_platform/figures/rendered_docx/mold_casts_package.png
