trissim/OpenMFD/papers/mfd_platform/figures/rendered_docx/supp_fig_s2_delamination.png

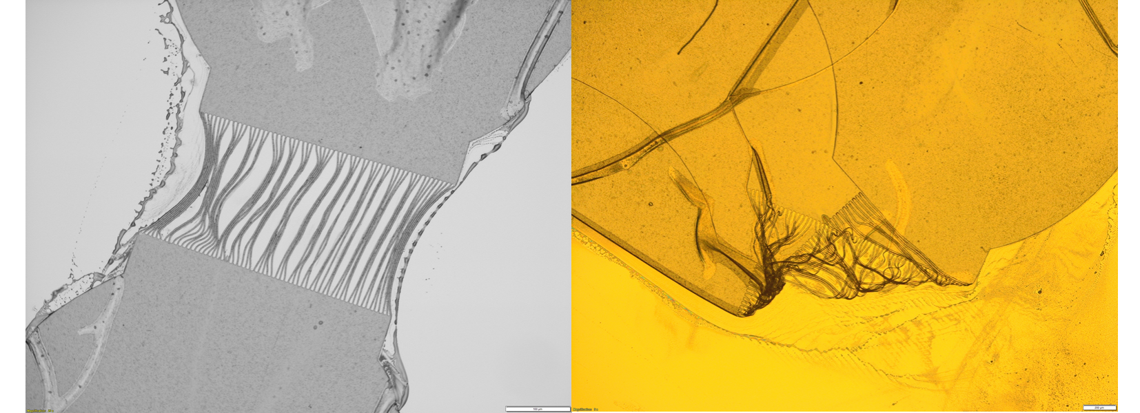
papers/mfd_platform/figures/rendered_docx/supp_fig_s2_delamination.png
