trissim/OpenMFD/designs/open_chamber/3mm_pairs_5x5/wall_3mm_pairs_5x5.stl

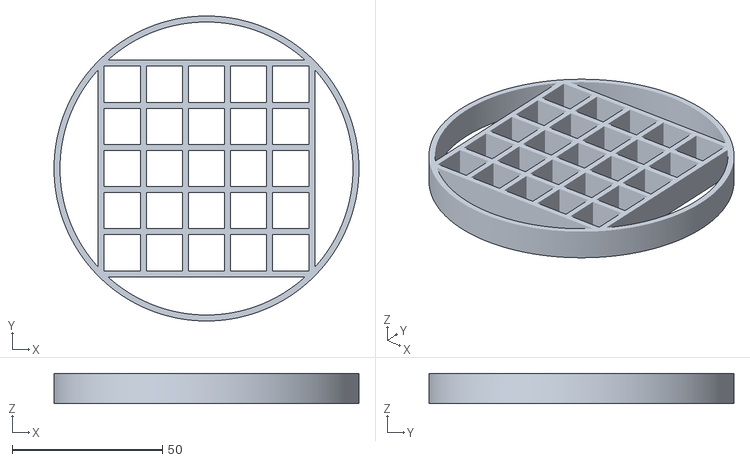
[picture p108: CAD file, 2025-10-20]
designs/open_chamber/3mm_pairs_5x5/wall_3mm_pairs_5x5.stl
101.4 x 101.4 x 10.0
