trissim/OpenMFD/designs/open_chamber/gradient_layout/wall_and_devices_gradient_multi_device.dxf

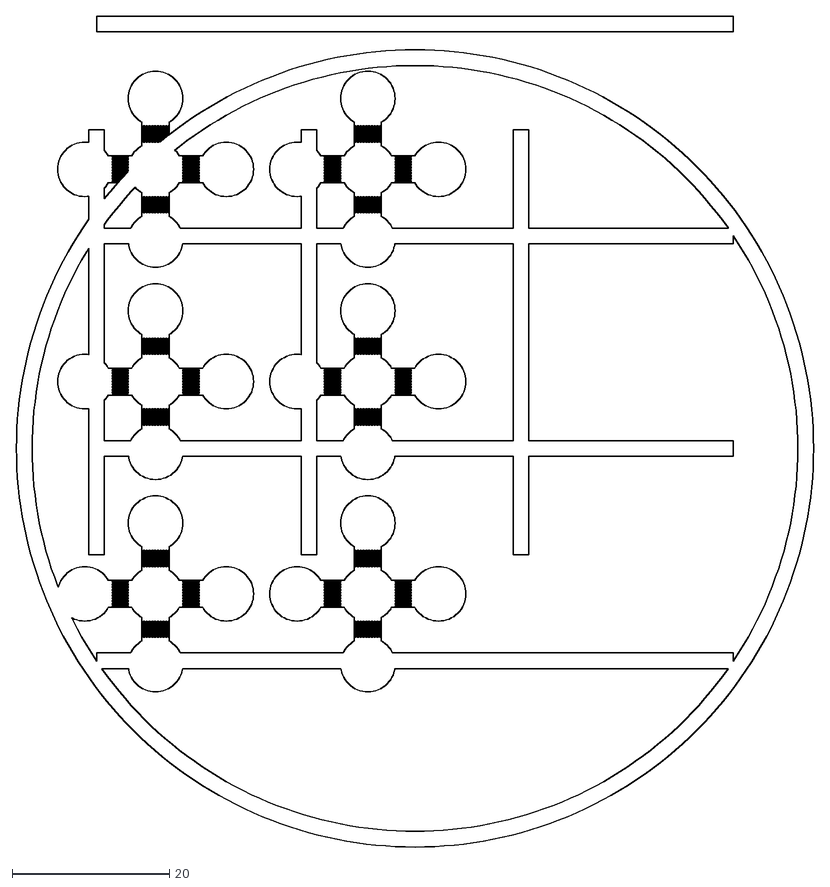
[picture p110: CAD file, 2025-10-20]
designs/open_chamber/gradient_layout/wall_and_devices_gradient_multi_device.dxf
101.4 x 105.7
