trissim/OpenMFD/designs/open_chamber/myelination/devices_myelination_single_device.dxf

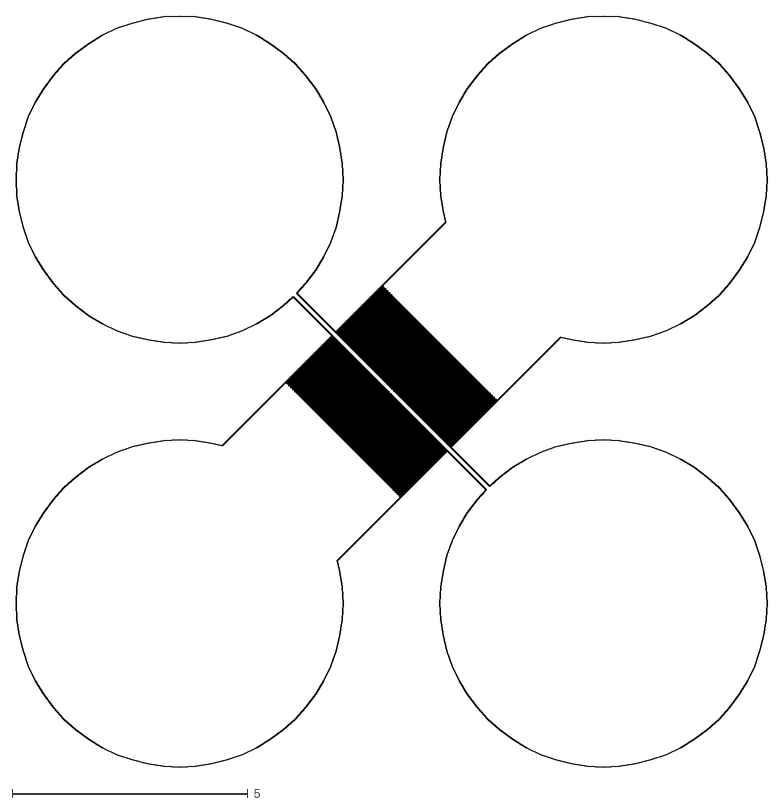
[picture p111: CAD file, 2025-10-20]
designs/open_chamber/myelination/devices_myelination_single_device.dxf
15.9 x 15.9
