trissim/OpenMFD/designs/plasma_racks/4mm_well_0.5inch_diam_device_final_cnc/single_adapter_final_cnc.step

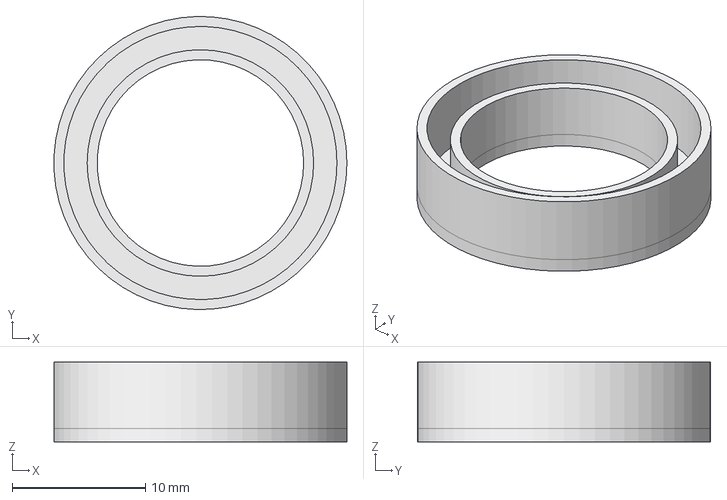
[picture p112: CAD file, 2025-10-20]
designs/plasma_racks/4mm_well_0.5inch_diam_device_final_cnc/single_adapter_final_cnc.step
22.0 x 22.0 x 6.00 mm
