trissim/OpenMFD/designs/plasma_racks/4mm_well_0.5inch_diam_device_v5/12_well_plate_v5.stl

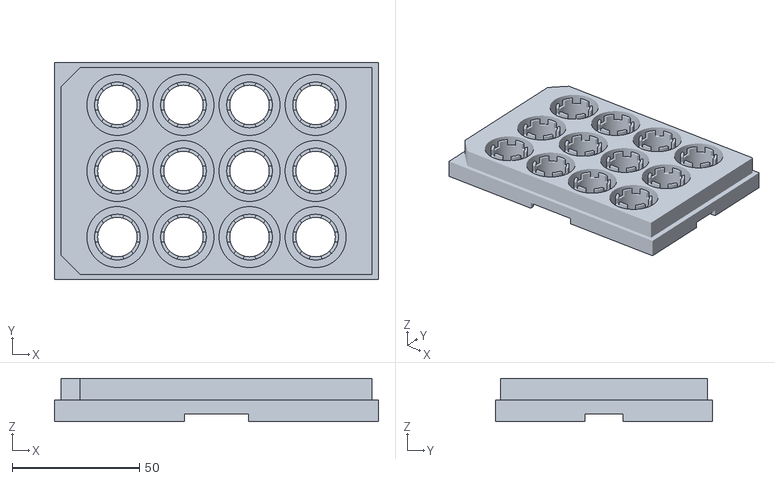
[picture p113: CAD file, 2025-10-20]
designs/plasma_racks/4mm_well_0.5inch_diam_device_v5/12_well_plate_v5.stl
127.5 x 85.3 x 17.0
