trissim/OpenMFD/designs/taylor/v9.2_chans_8x12_units_.sync-conflict-20211020-150856-3VDLRGL.dxf

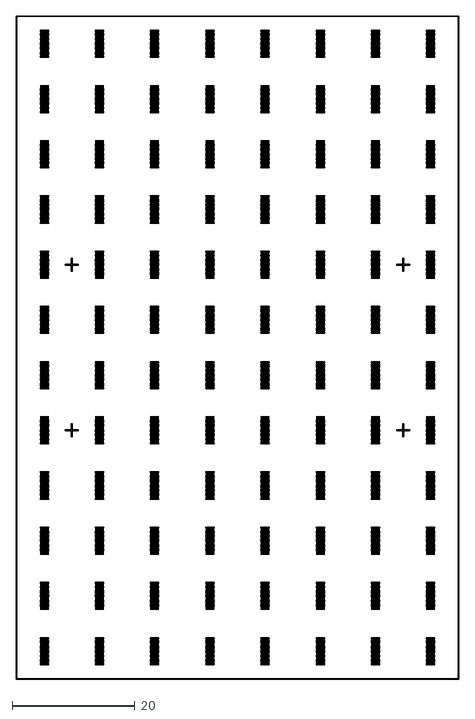
[picture p114: CAD file, 2025-10-20]
designs/taylor/v9.2_chans_8x12_units_.sync-conflict-20211020-150856-3VDLRGL.dxf
72.1 x 108.1
