trissim/OpenMFD/orders/cnc_order_final_april_27th_2024/96_well_plate_reservoirs_final_cnc_v2.step

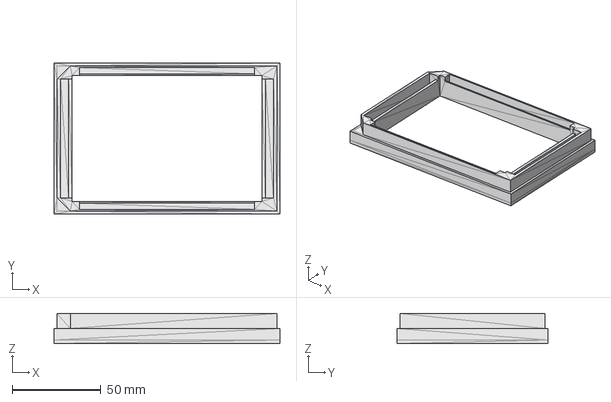
[picture p115: CAD file, 2025-10-20]
orders/cnc_order_final_april_27th_2024/96_well_plate_reservoirs_final_cnc_v2.step
127.5 x 85.3 x 17.0 mm
