trissim/OpenMFD/orders/order oct_13_2022/2compartment_96well_v2/2compartment_multi_device_bottom.dxf

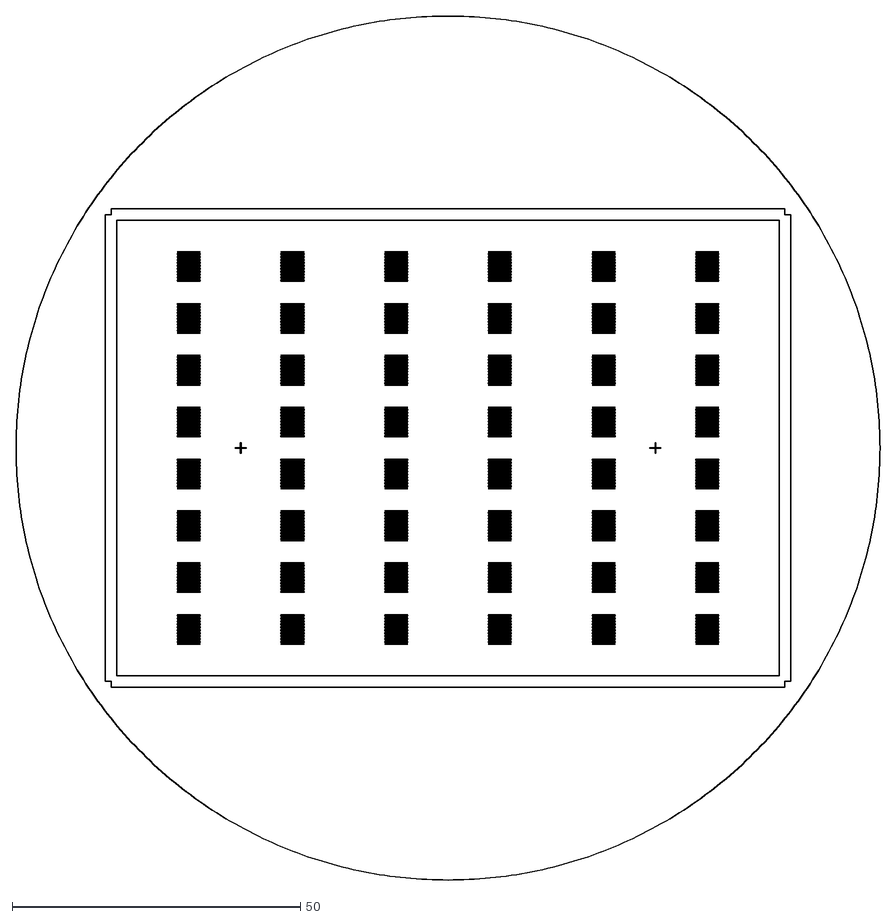
[picture p116: CAD file, 2025-10-20]
orders/order oct_13_2022/2compartment_96well_v2/2compartment_multi_device_bottom.dxf
150.0 x 150.0
