trissim/OpenMFD/orders/order oct_13_2022/closed_chamber_4x4_top.dxf

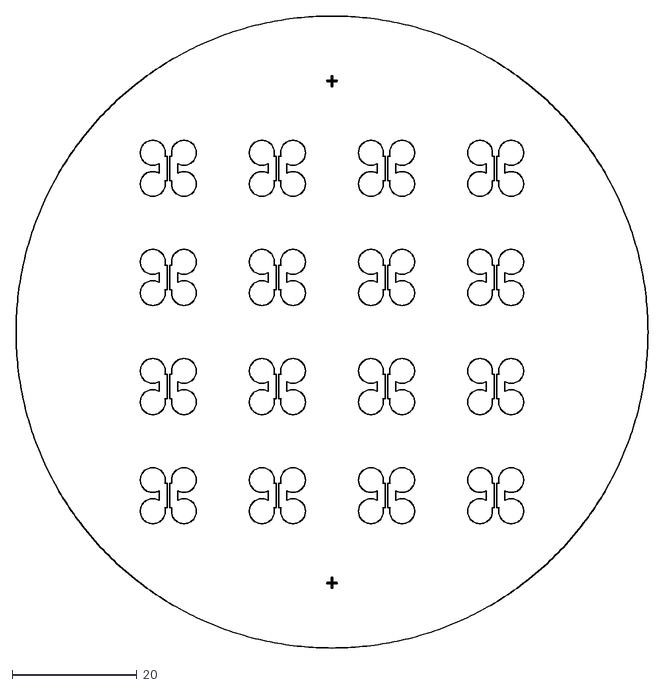
[picture p118: CAD file, 2025-10-20]
orders/order oct_13_2022/closed_chamber_4x4_top.dxf
101.4 x 101.4
