trissim/OpenMFD/orders/order oct_15_2022/2compartment_96well_v2/2compartment_single_device_top.dxf

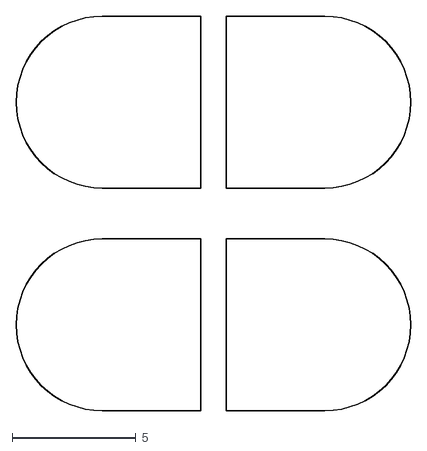
[picture p119: CAD file, 2025-10-20]
orders/order oct_15_2022/2compartment_96well_v2/2compartment_single_device_top.dxf
15.9 x 15.9
