trissim/OpenMFD/orders/order oct_15_2022/2compartment_duplicates_4x4_v2/open_duplicates_4mm_4x4_bottom.dxf

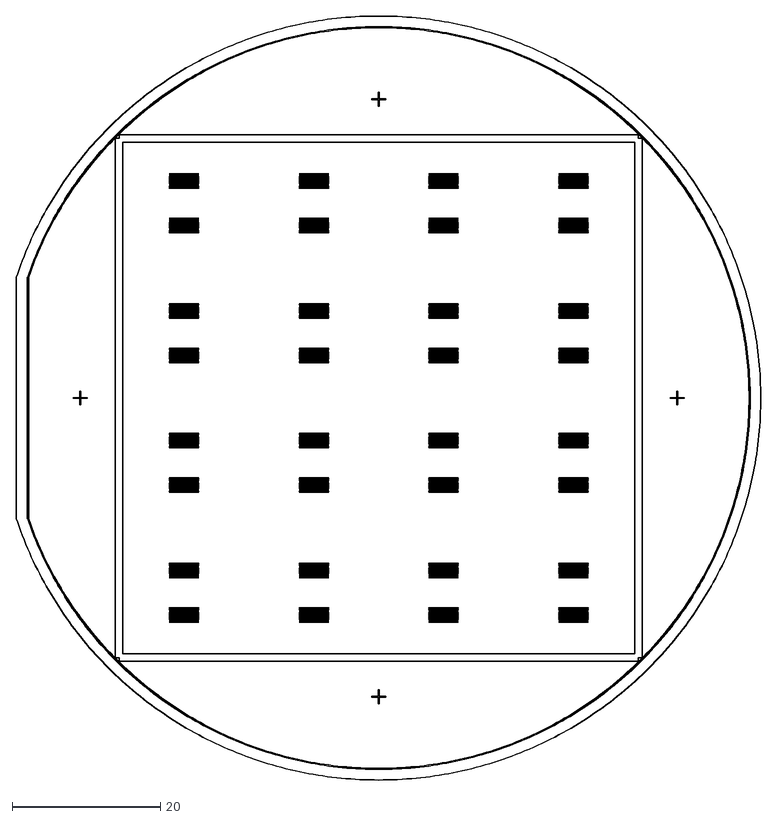
[picture p120: CAD file, 2025-10-20]
orders/order oct_15_2022/2compartment_duplicates_4x4_v2/open_duplicates_4mm_4x4_bottom.dxf
100.4 x 103.0
