trissim/OpenMFD/orders/order oct_15_2022/4x4/closed_chamber_4x4_bottom.dxf

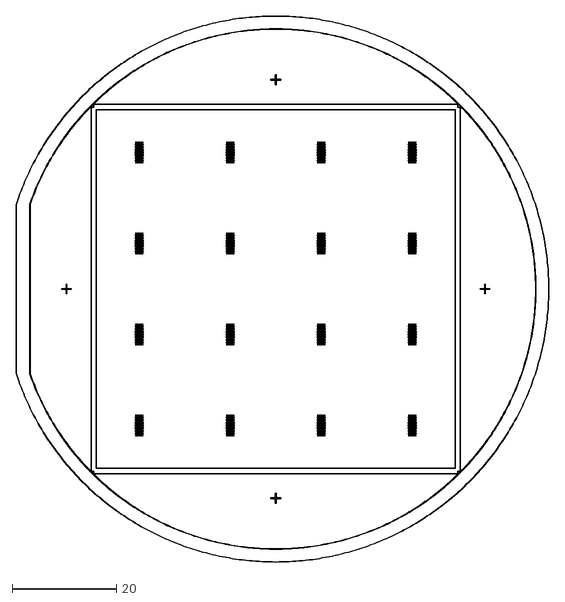
[picture p121: CAD file, 2025-10-20]
orders/order oct_15_2022/4x4/closed_chamber_4x4_bottom.dxf
102.4 x 105.0
