trissim/OpenMFD/orders/order oct_15_2022/closed_chamber_4x4_top.dxf

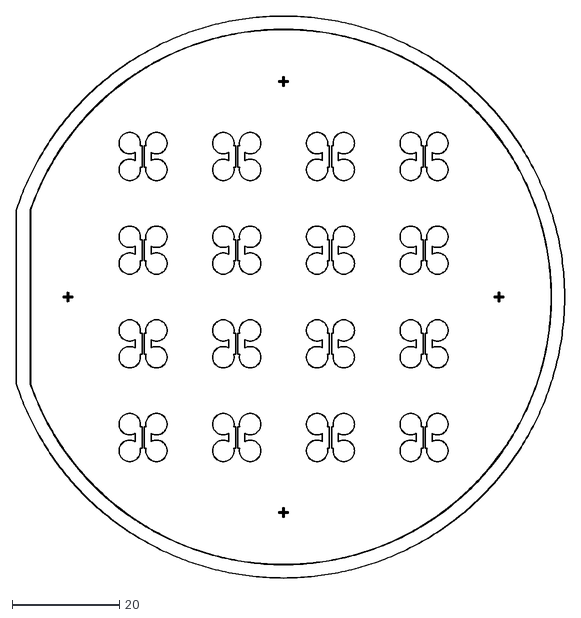
[picture p122: CAD file, 2025-10-20]
orders/order oct_15_2022/closed_chamber_4x4_top.dxf
102.4 x 105.0
