trissim/OpenMFD/orders/order_dec_20_2023/2_compartment_96_well_300um_v11/2_compartment_96_well_300um_v11_single_bottom.dxf

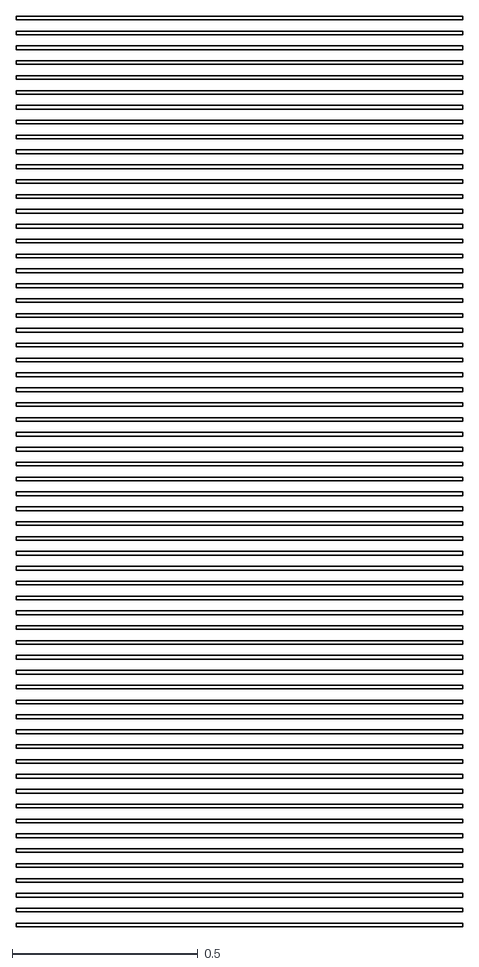
[picture p123: CAD file, 2025-10-20]
orders/order_dec_20_2023/2_compartment_96_well_300um_v11/2_compartment_96_well_300um_v11_single_bottom.dxf
1.20 x 2.45
