trissim/OpenMFD/orders/order_nov_2_2021/device_96_well_3mm_diameter.dxf

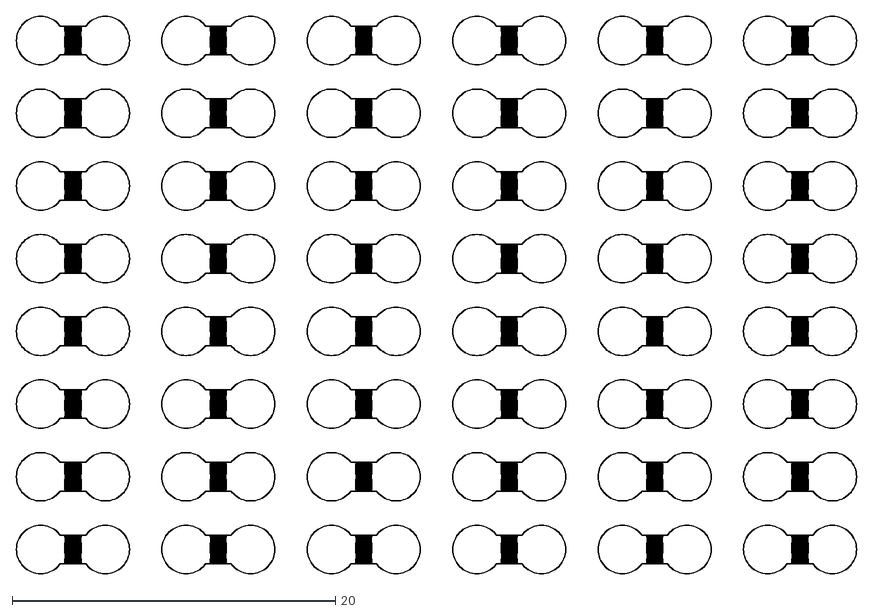
[picture p126: CAD file, 2025-10-20]
orders/order_nov_2_2021/device_96_well_3mm_diameter.dxf
52.0 x 34.5
