trissim/OpenMFD/orders/wafer_rack_send_cut_send_dec_9_2024/shelf.dxf

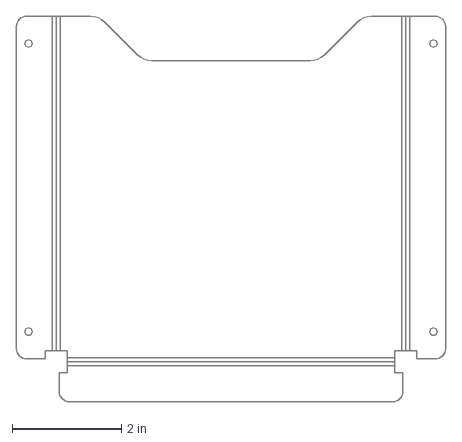
[picture p127: CAD file, 2025-10-20]
orders/wafer_rack_send_cut_send_dec_9_2024/shelf.dxf
7.85 x 7.05 in
