trissim/OpenMFD/plates/96_well_plate_reservoirs_print_resin_v4/96_well_plate_reservoirs_print_resin_v4.step

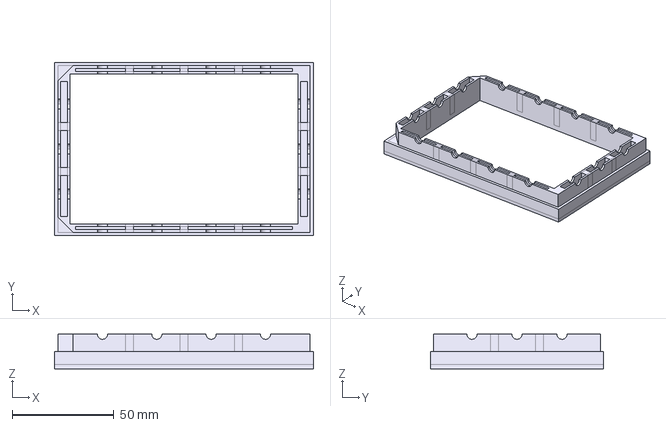
[picture p128: CAD file, 2025-10-20]
plates/96_well_plate_reservoirs_print_resin_v4/96_well_plate_reservoirs_print_resin_v4.step
127.5 x 85.3 x 17.0 mm
