trissim/OpenMFD/tests/wafer_holder.stl

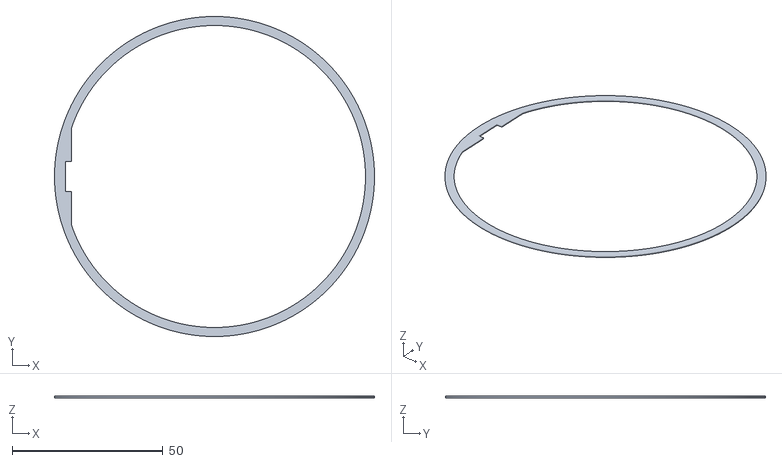
[picture p129: CAD file, 2025-10-20]
tests/wafer_holder.stl
106.2 x 106.2 x 0.5
