trissim/OpenMFD/designs/closed_chamber/4x4/closed_top_bottom.dxf

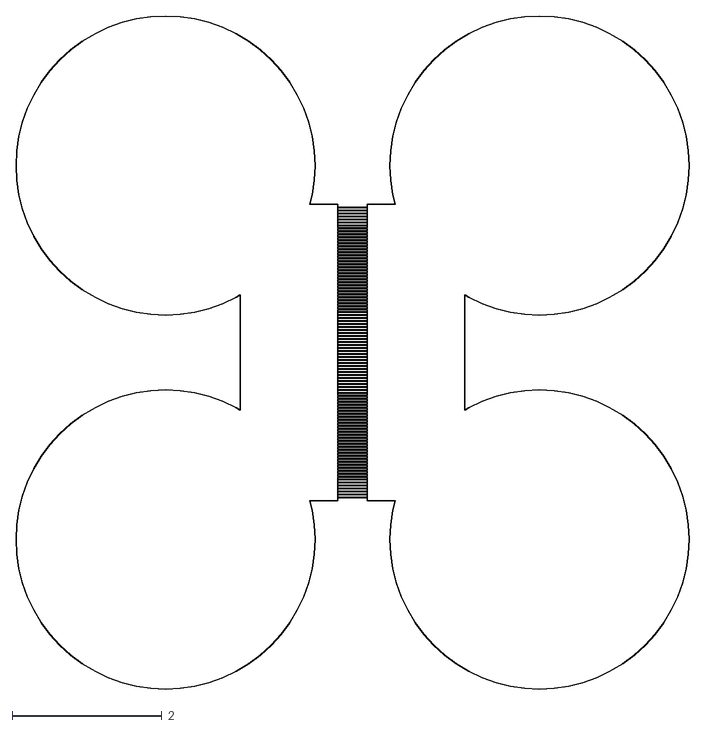
[picture p130: CAD file, 2025-10-20]
designs/closed_chamber/4x4/closed_top_bottom.dxf
9.00 x 9.00
