trissim/OpenMFD/designs/open_chamber/2_compartment_154_well_300um_v21/wall_single_2_compartment_96_well_300um_v21.stl

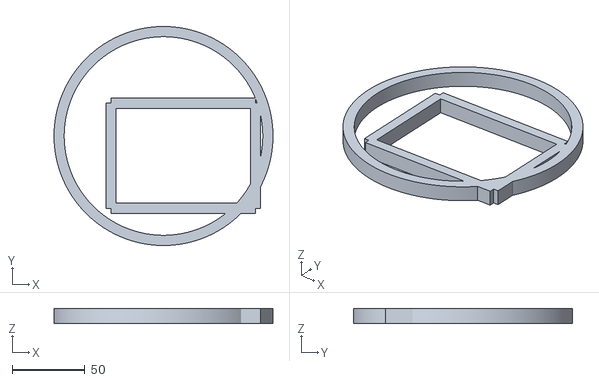
[picture p131: CAD file, 2025-10-20]
designs/open_chamber/2_compartment_154_well_300um_v21/wall_single_2_compartment_96_well_300um_v21.stl
150.0 x 150.0 x 10.0
