trissim/OpenMFD/designs/open_chamber/2_compartment_192_well_300um_v22/2_compartment_96_well_300um_v22_single_bottom.dxf

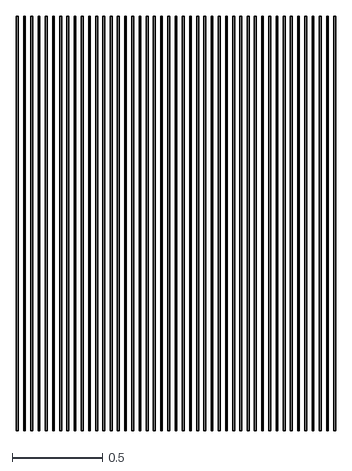
[picture p132: CAD file, 2025-10-20]
designs/open_chamber/2_compartment_192_well_300um_v22/2_compartment_96_well_300um_v22_single_bottom.dxf
1.77 x 2.30
