trissim/OpenMFD/designs/open_chamber/2_compartment_384_well_300um_suex100_v25/wafer.dxf

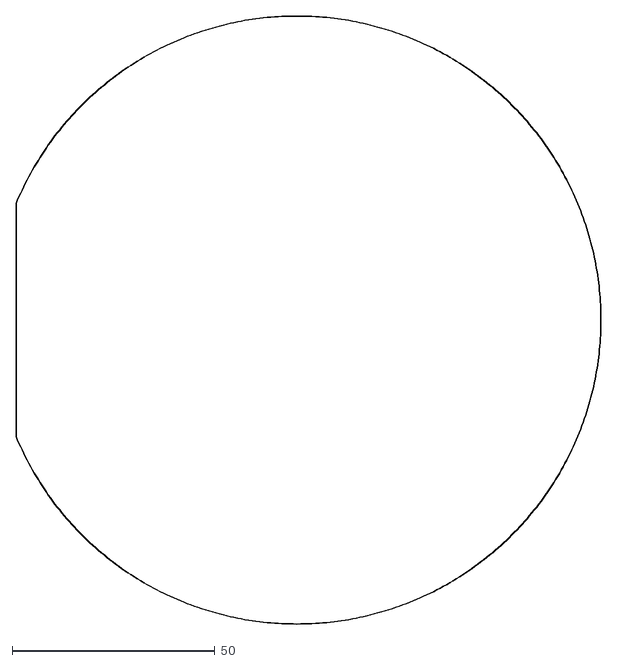
[picture p133: CAD file, 2025-10-20]
designs/open_chamber/2_compartment_384_well_300um_suex100_v25/wafer.dxf
144.3 x 150.0
