trissim/OpenMFD/designs/open_chamber/2_compartment_48_well_300um_v22/2_compartment_96_well_300um_v22_single_bottom.dxf

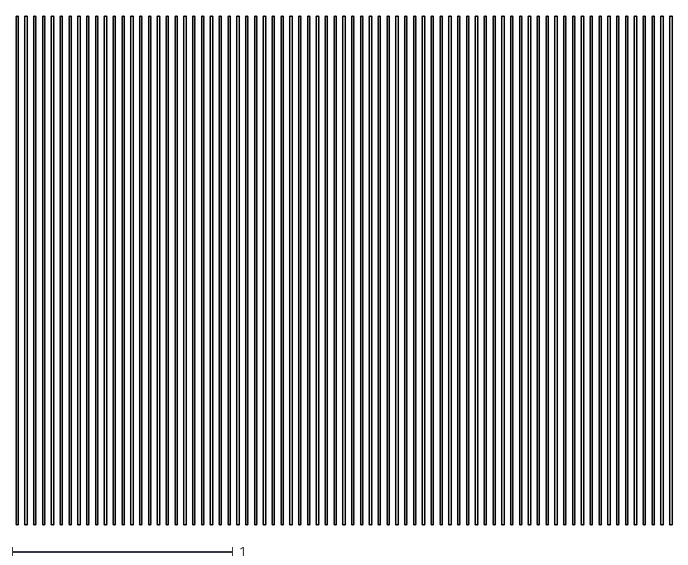
[picture p134: CAD file, 2025-10-20]
designs/open_chamber/2_compartment_48_well_300um_v22/2_compartment_96_well_300um_v22_single_bottom.dxf
2.97 x 2.30
