trissim/OpenMFD/designs/open_chamber/2_compartment_4x4_300um_suex200_v27/2_compartment_4x4_300um_suex100_v27_single_bottom.dxf

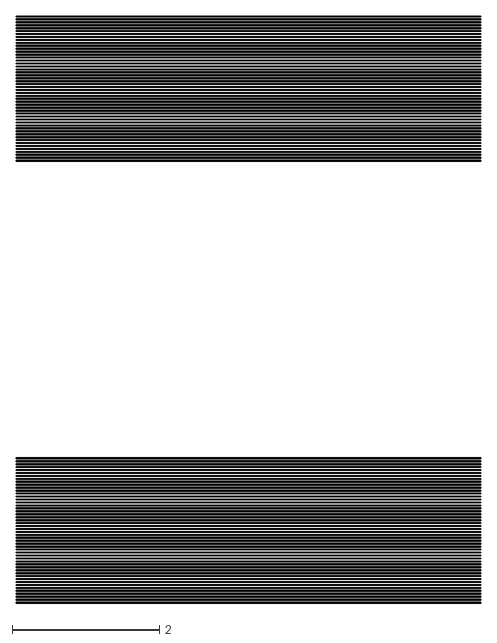
[picture p135: CAD file, 2025-10-20]
designs/open_chamber/2_compartment_4x4_300um_suex200_v27/2_compartment_4x4_300um_suex100_v27_single_bottom.dxf
6.30 x 7.97
