trissim/OpenMFD/designs/open_chamber/2_compartment_96_well_1000um_v10/2_compartment_96_well_1000um_v10_single_top.dxf

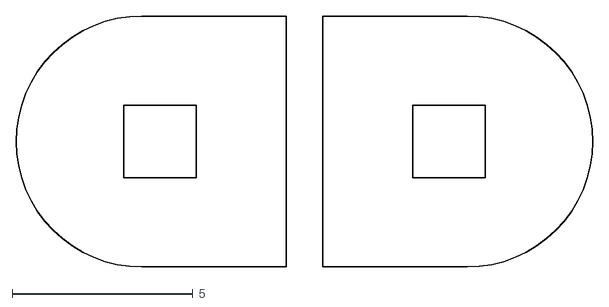
[picture p136: CAD file, 2025-10-20]
designs/open_chamber/2_compartment_96_well_1000um_v10/2_compartment_96_well_1000um_v10_single_top.dxf
15.9 x 6.94
