trissim/OpenMFD/designs/open_chamber/2_compartment_96_well_300um_suex100_v26/2_compartment_96_well_300um_suex100_v26_single_top.dxf

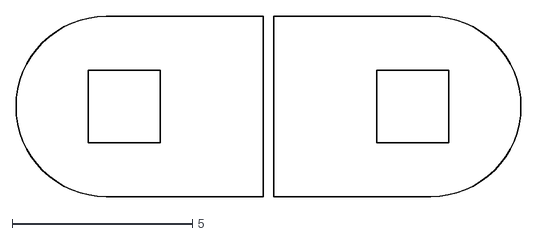
[picture p137: CAD file, 2025-10-20]
designs/open_chamber/2_compartment_96_well_300um_suex100_v26/2_compartment_96_well_300um_suex100_v26_single_top.dxf
14.0 x 5.00
