trissim/OpenMFD/designs/open_chamber/2_compartment_96_well_300um_suex200_v27/2_compartment_96_well_300um_suex200_v27_single_insert.stl

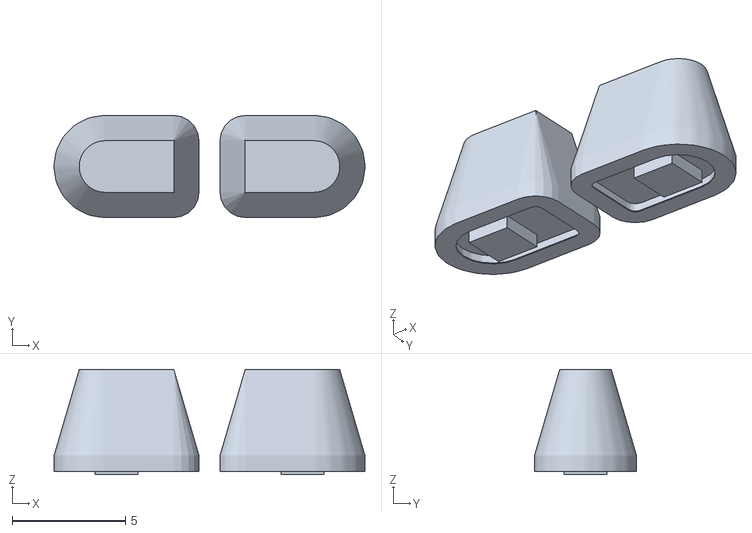
[picture p138: CAD file, 2026-04-29]
designs/open_chamber/2_compartment_96_well_300um_suex200_v27/2_compartment_96_well_300um_suex200_v27_single_insert.stl
13.7 x 4.50 x 4.64
