trissim/OpenMFD/designs/open_chamber/2_compartment_96_well_300um_v21/2_compartment_96_well_300um_v21_single_aligned.dxf

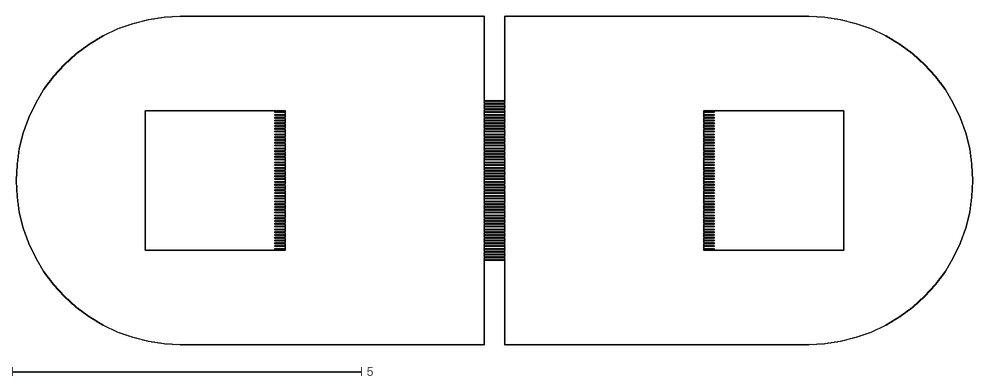
[picture p139: CAD file, 2025-10-20]
designs/open_chamber/2_compartment_96_well_300um_v21/2_compartment_96_well_300um_v21_single_aligned.dxf
13.7 x 4.70
