trissim/OpenMFD/designs/open_chamber/2compartment/2compartment_many_single_device_bottom.dxf

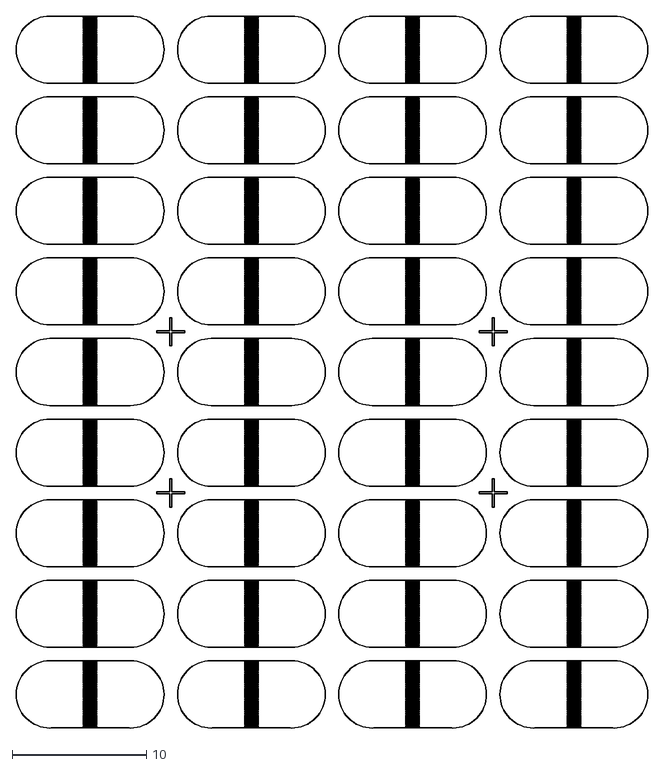
[picture p140: CAD file, 2025-10-20]
designs/open_chamber/2compartment/2compartment_many_single_device_bottom.dxf
47.0 x 53.0
