trissim/OpenMFD/designs/open_chamber/2compartment_96_well_inserts_v9_300um/wall_single_2_compartment_96_well_300um.stl

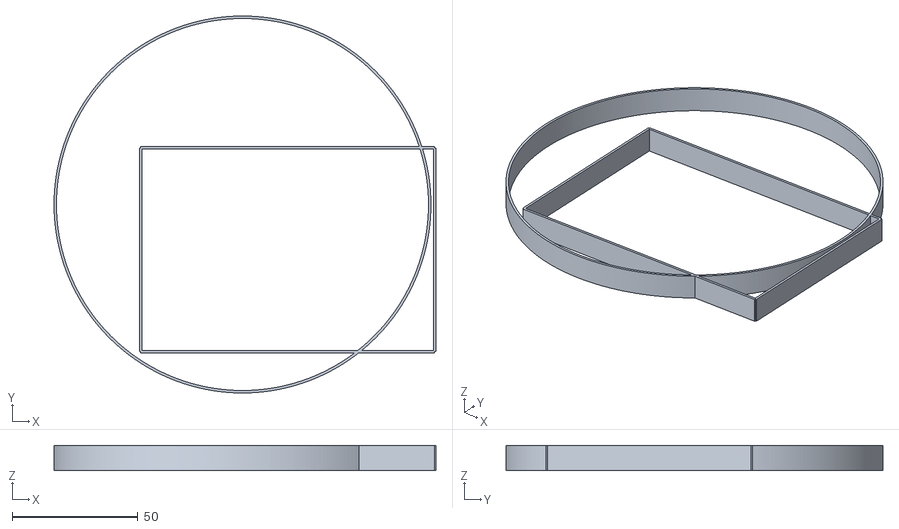
[picture p141: CAD file, 2025-10-20]
designs/open_chamber/2compartment_96_well_inserts_v9_300um/wall_single_2_compartment_96_well_300um.stl
152.0 x 150.0 x 10.0
