trissim/OpenMFD/designs/open_chamber/2compartment_duplicates_4x4_refactored_inserts_v11_300um/2_compartment_96_well_300um_v19/2_compartment_96_well_300um_v19_single_bottom.dxf

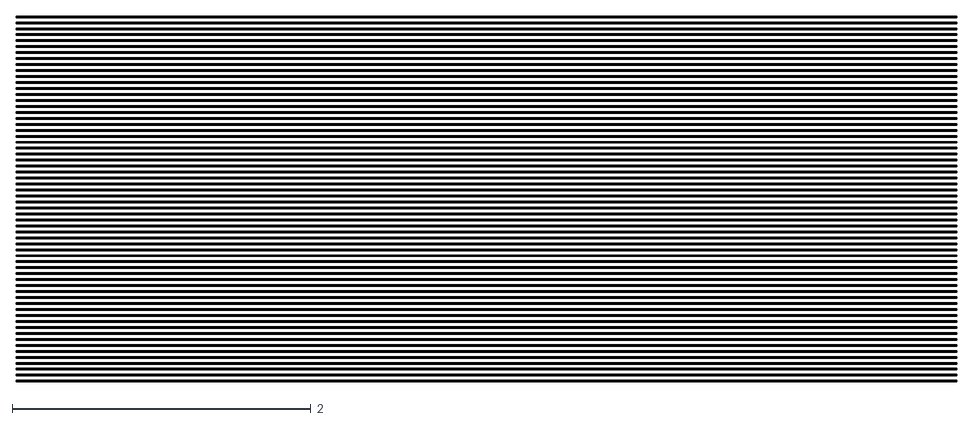
[picture p145: CAD file, 2025-10-20]
designs/open_chamber/2compartment_duplicates_4x4_refactored_inserts_v11_300um/2_compartment_96_well_300um_v19/2_compartment_96_well_300um_v19_single_bottom.dxf
6.30 x 2.45
