trissim/OpenMFD/designs/open_chamber/3compartment/devices_3compartment_single_device_bottom.dxf

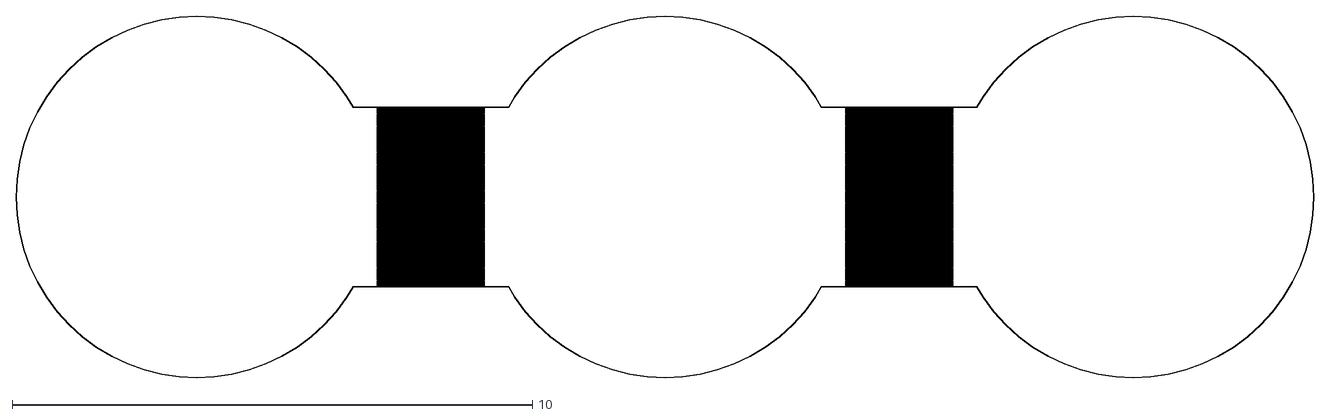
[picture p146: CAD file, 2025-10-20]
designs/open_chamber/3compartment/devices_3compartment_single_device_bottom.dxf
24.9 x 6.94
