trissim/OpenMFD/designs/open_chamber/3mm_pairs_5x5/devices_3mm_pairs_5x5.dxf

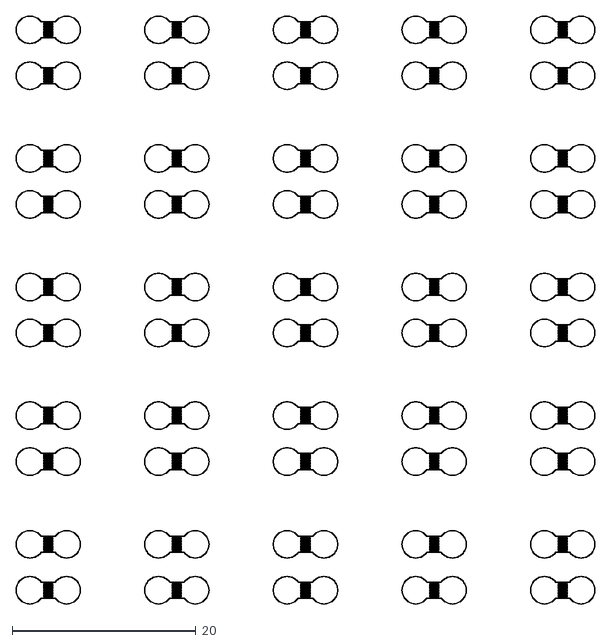
[picture p147: CAD file, 2025-10-20]
designs/open_chamber/3mm_pairs_5x5/devices_3mm_pairs_5x5.dxf
63.0 x 64.0
