trissim/OpenMFD/designs/open_chamber/gradient_layout/devices_gradient_multi_device.dxf

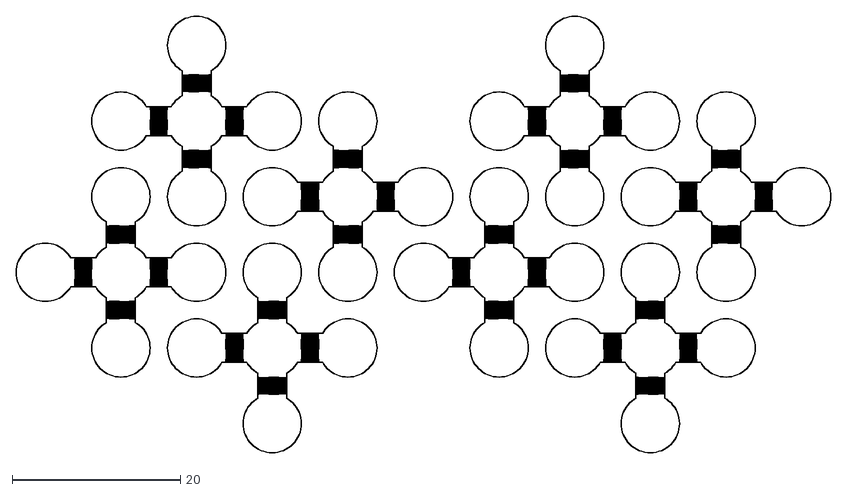
[picture p148: CAD file, 2025-10-20]
designs/open_chamber/gradient_layout/devices_gradient_multi_device.dxf
96.9 x 51.9
