trissim/OpenMFD/designs/open_chamber/myelination/devices_myelination_multi_device.dxf

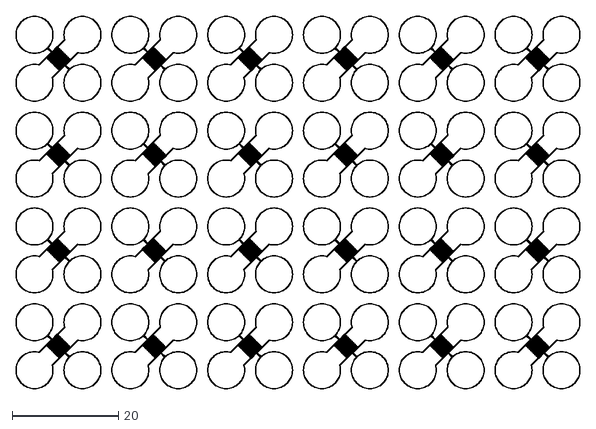
[picture p149: CAD file, 2025-10-20]
designs/open_chamber/myelination/devices_myelination_multi_device.dxf
105.9 x 69.9
