trissim/OpenMFD/orders/cnc_order_final_march_13th_2024/12_well_plate_0.5inch_diam_final_cnc.FCStd

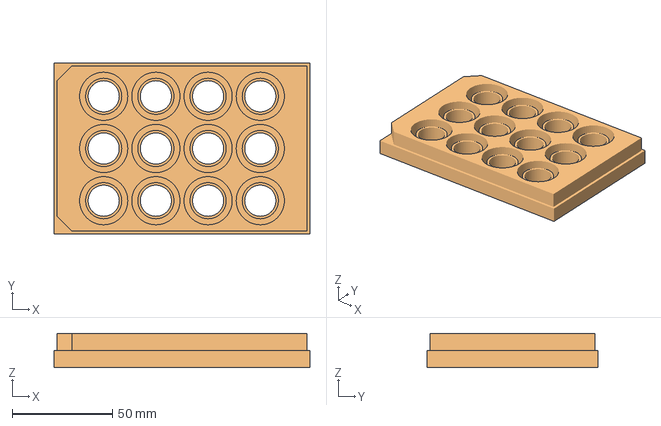
[picture p151: CAD file, 2025-10-20]
orders/cnc_order_final_march_13th_2024/12_well_plate_0.5inch_diam_final_cnc.FCStd
127.5 x 85.3 x 17.0 mm
_2_well_plate_0_5inch_diam_final_cnc001
12_well_plate_0.5inch_diam_final_cnc
