trissim/OpenMFD/orders/order oct_13_2022/2compartment_96well_v2/wall_2compartment_multi.stl

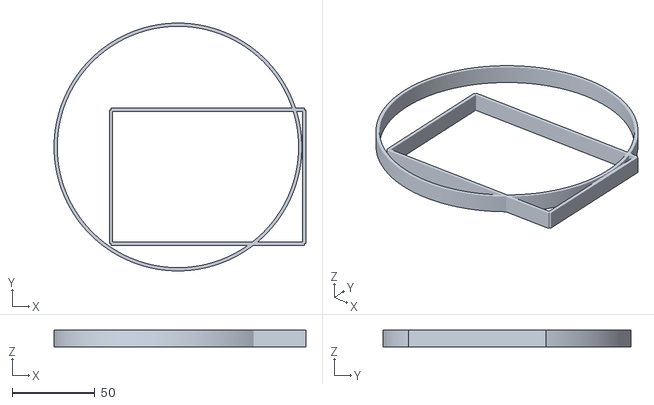
[picture p152: CAD file, 2025-10-20]
orders/order oct_13_2022/2compartment_96well_v2/wall_2compartment_multi.stl
152.5 x 150.0 x 10.0
