trissim/OpenMFD/orders/order oct_15_2022/2compartment_96well_v2/2compartment_multi_device_bottom.dxf

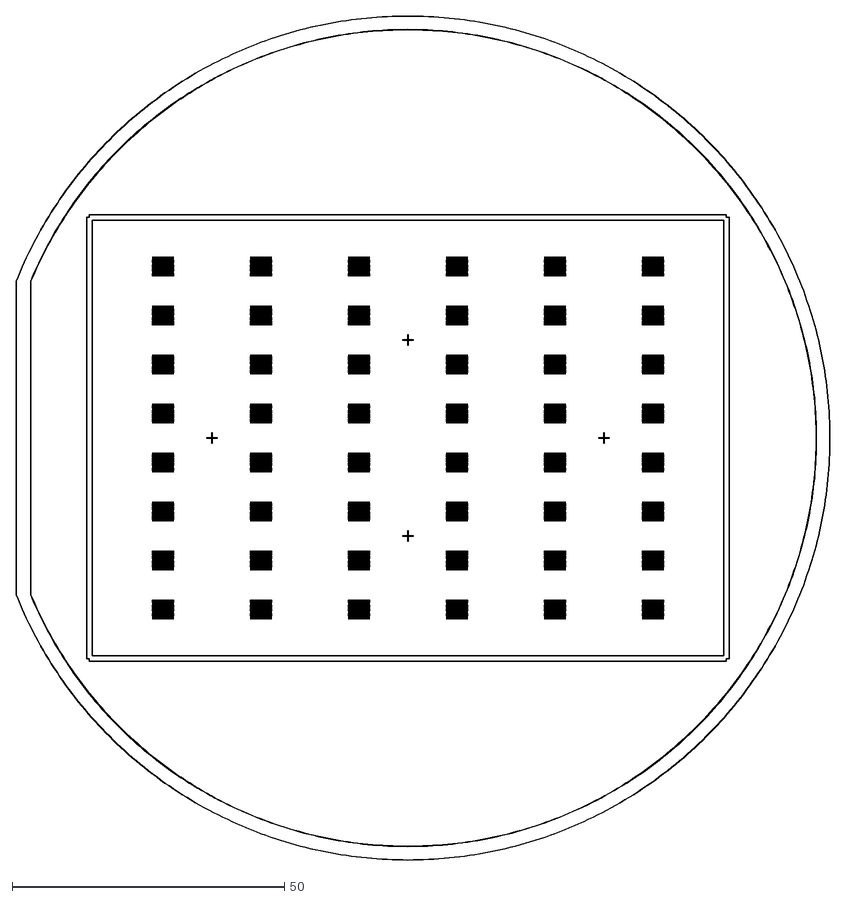
[picture p154: CAD file, 2025-10-20]
orders/order oct_15_2022/2compartment_96well_v2/2compartment_multi_device_bottom.dxf
149.5 x 155.0
