trissim/OpenMFD/orders/order oct_15_2022/2compartment_duplicates_4x4_v2/wall_open_chamber_4x4_top.dxf

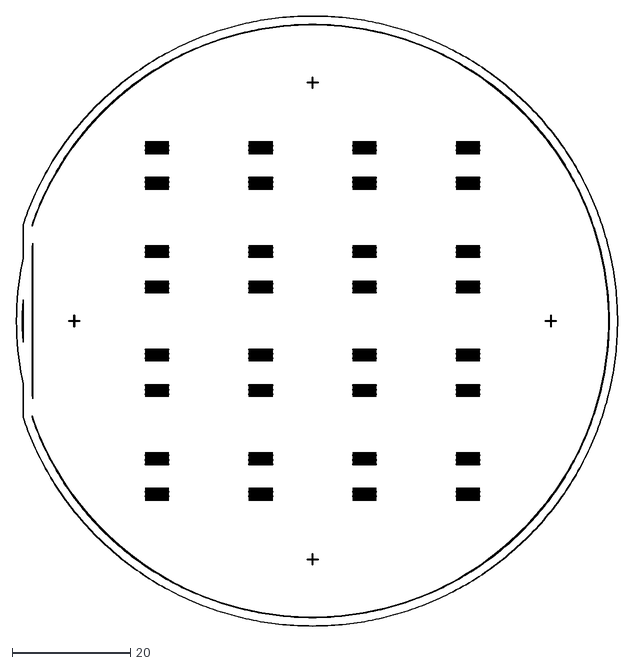
[picture p155: CAD file, 2025-10-20]
orders/order oct_15_2022/2compartment_duplicates_4x4_v2/wall_open_chamber_4x4_top.dxf
101.5 x 103.0
