trissim/OpenMFD/orders/order oct_15_2022/4x4/closed_top.dxf

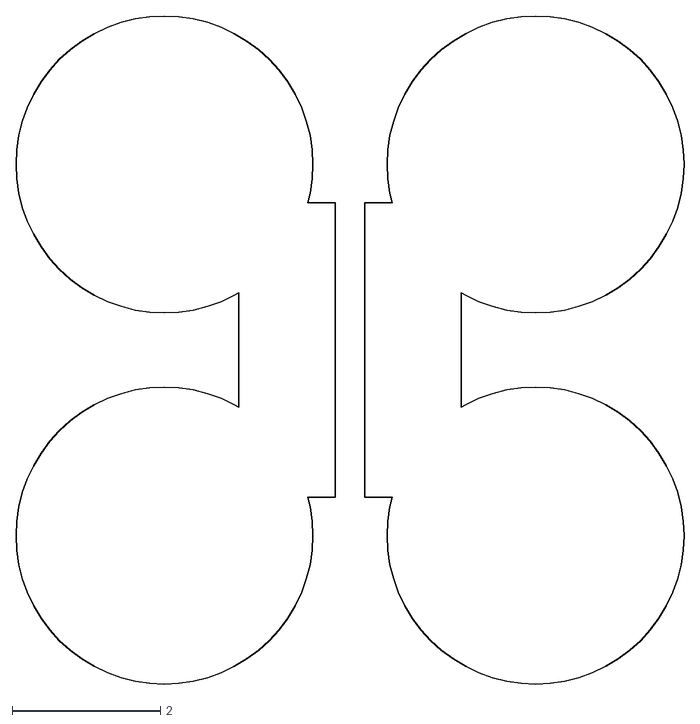
[picture p156: CAD file, 2025-10-20]
orders/order oct_15_2022/4x4/closed_top.dxf
9.00 x 9.00
