trissim/OpenMFD/orders/order_dec_20_2023/2_compartment_96_well_300um_v11/2_compartment_96_well_300um_v11_single_aligned.dxf

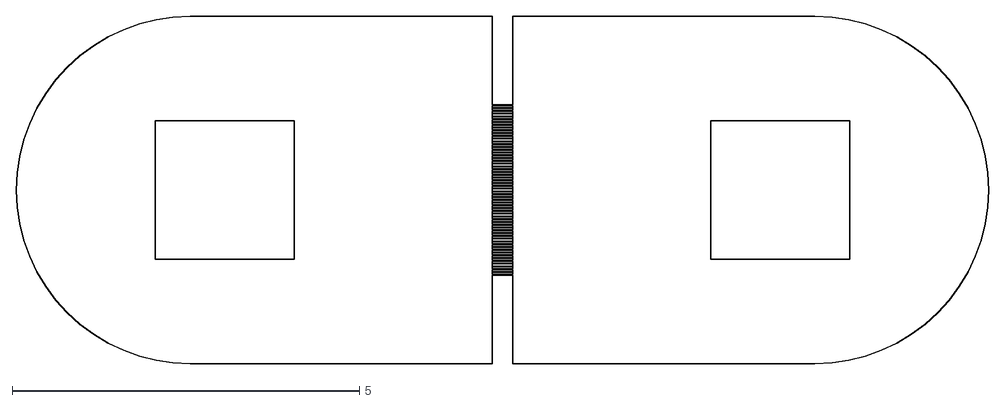
[picture p157: CAD file, 2025-10-20]
orders/order_dec_20_2023/2_compartment_96_well_300um_v11/2_compartment_96_well_300um_v11_single_aligned.dxf
14.0 x 5.00
