trissim/OpenMFD/orders/order_july25th_2024/2_compartment_96_well_300um_v17/2_compartment_96_well_300um_v17_single_bottom.dxf

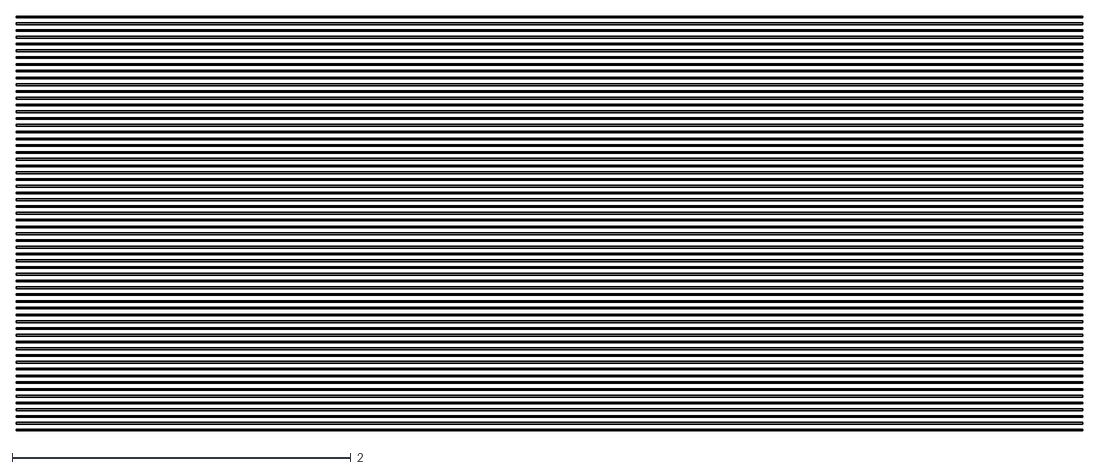
[picture p158: CAD file, 2025-10-20]
orders/order_july25th_2024/2_compartment_96_well_300um_v17/2_compartment_96_well_300um_v17_single_bottom.dxf
6.30 x 2.45
