trissim/OpenMFD/orders/order_july25th_2024/2_compartment_96_well_300um_v17_top.dxf

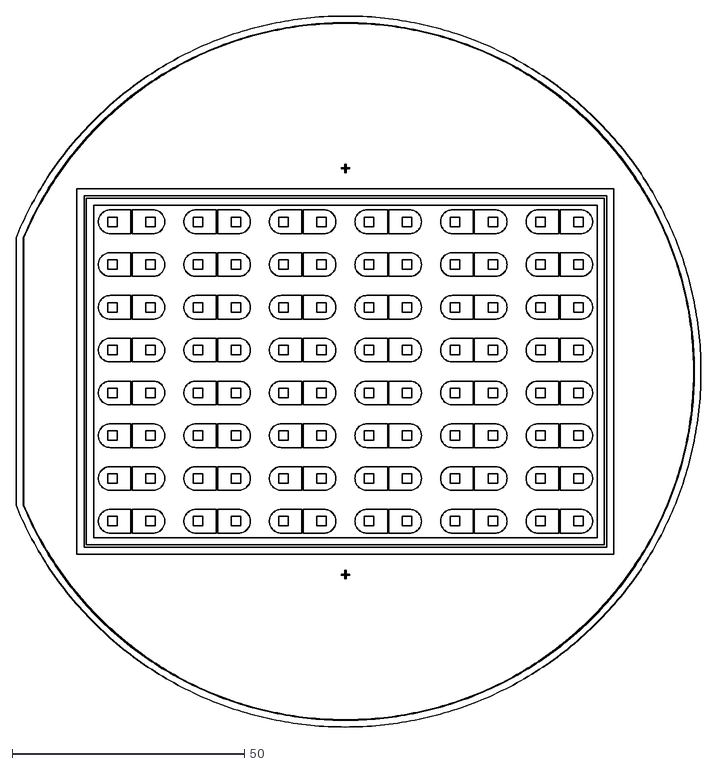
[picture p159: CAD file, 2025-10-20]
orders/order_july25th_2024/2_compartment_96_well_300um_v17_top.dxf
147.4 x 153.0
