trissim/OpenMFD/orders/order_nov_2_2021/device_96_well_3mm_diameter_rotated.dxf

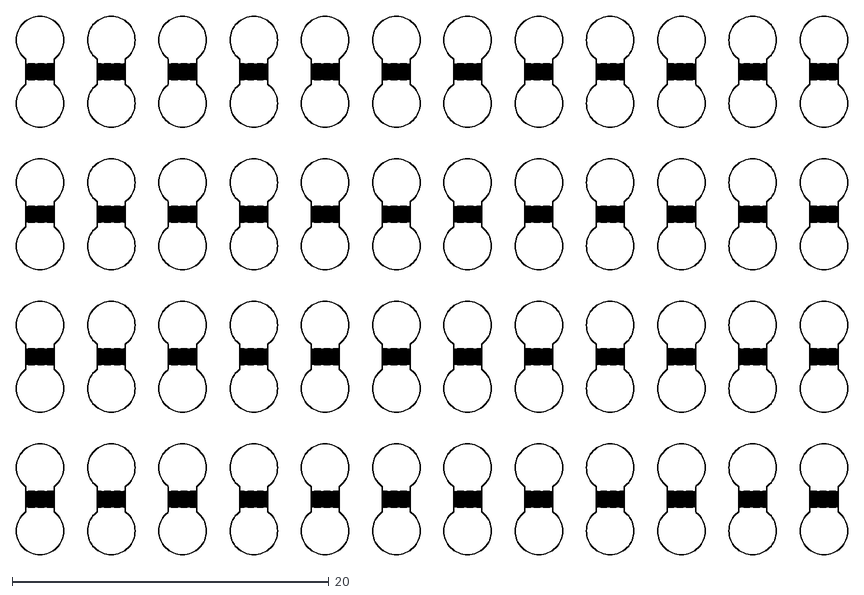
[picture p160: CAD file, 2025-10-20]
orders/order_nov_2_2021/device_96_well_3mm_diameter_rotated.dxf
52.5 x 34.0
