trissim/OpenMFD/orders/wafer_rack_send_cut_send_dec_9_2024/wall.dxf

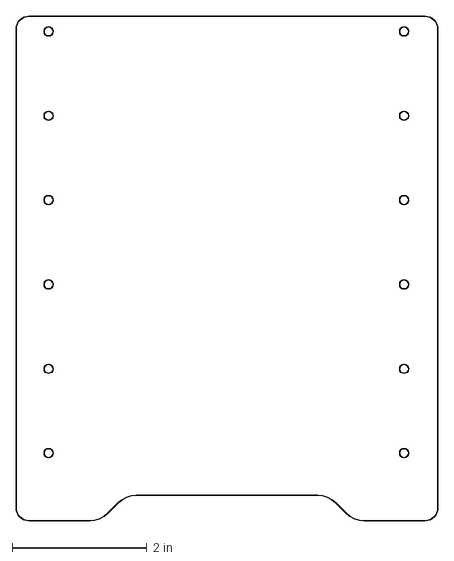
[picture p161: CAD file, 2025-10-20]
orders/wafer_rack_send_cut_send_dec_9_2024/wall.dxf
6.25 x 7.47 in
