trissim/OpenMFD/plates/96_well_plate_reservoirs_print_hips_2/96_well_plate_reservoirs_print_hips_2_chamfered_v2.stl

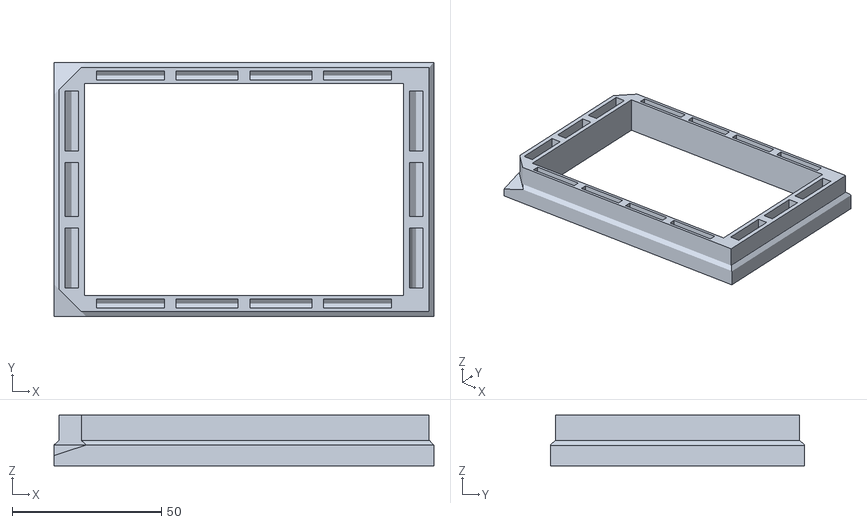
[picture p162: CAD file, 2025-10-20]
plates/96_well_plate_reservoirs_print_hips_2/96_well_plate_reservoirs_print_hips_2_chamfered_v2.stl
127.5 x 85.3 x 17.0
