trissim/OpenMFD/tests/open_duplicates_4mm_2x2_wells.stl

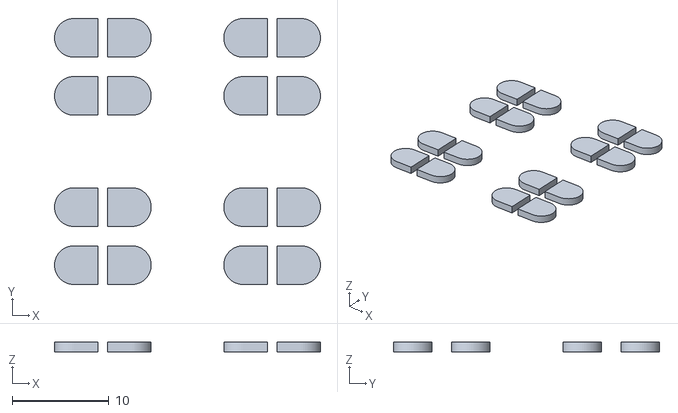
[picture p163: CAD file, 2025-10-20]
tests/open_duplicates_4mm_2x2_wells.stl
27.5 x 27.5 x 1.00
