trissim/OpenMFD/designs/closed_chamber/4x4/closed_chamber_4x4_aligned.dxf

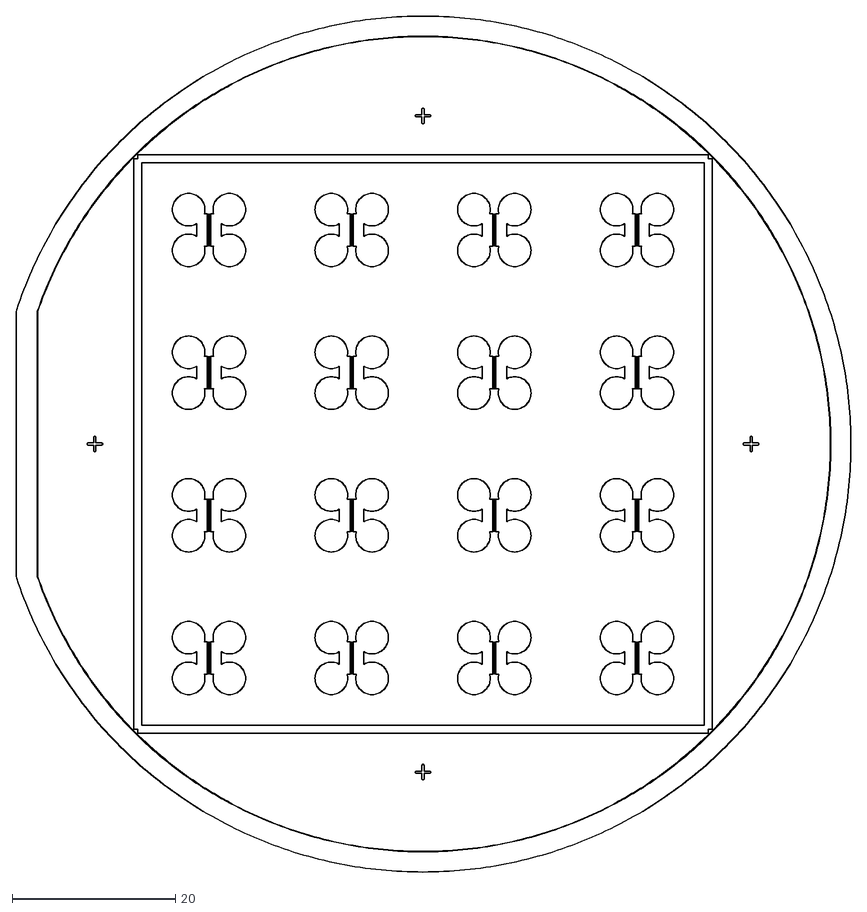
[picture p164: CAD file, 2025-10-20]
designs/closed_chamber/4x4/closed_chamber_4x4_aligned.dxf
102.4 x 105.0
