trissim/OpenMFD/designs/open_chamber/2_compartment_154_well_300um_v21/2_compartment_96_well_300um_v21_top.dxf

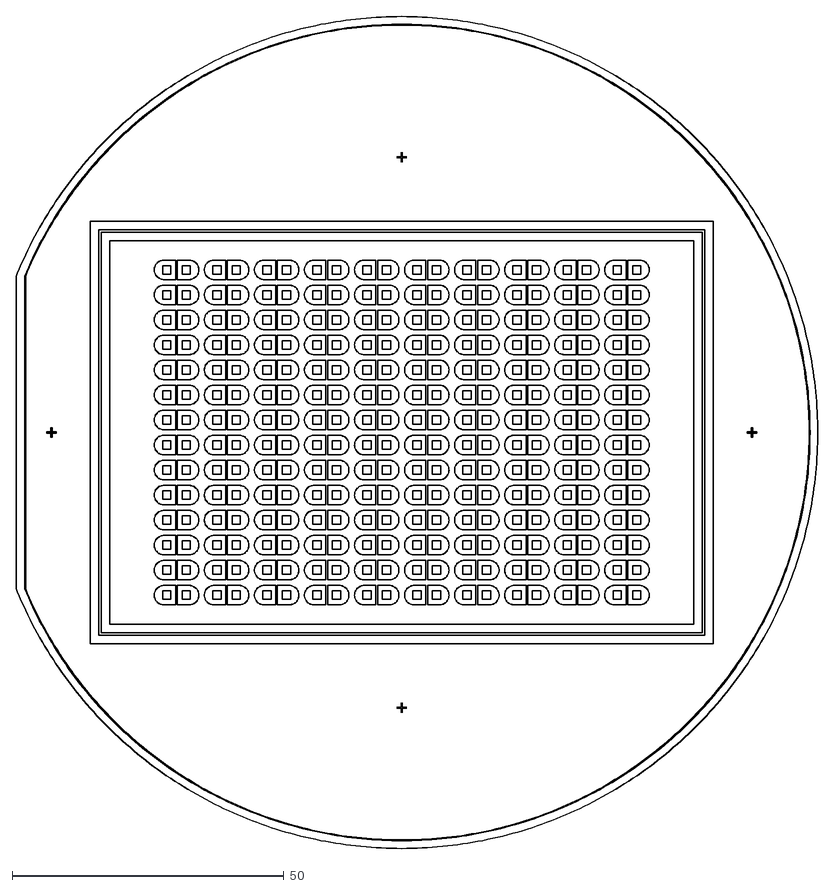
[picture p165: CAD file, 2025-10-20]
designs/open_chamber/2_compartment_154_well_300um_v21/2_compartment_96_well_300um_v21_top.dxf
147.4 x 153.0
