trissim/OpenMFD/designs/open_chamber/2_compartment_192_well_300um_v22/2_compartment_96_well_300um_v22_bottom.dxf

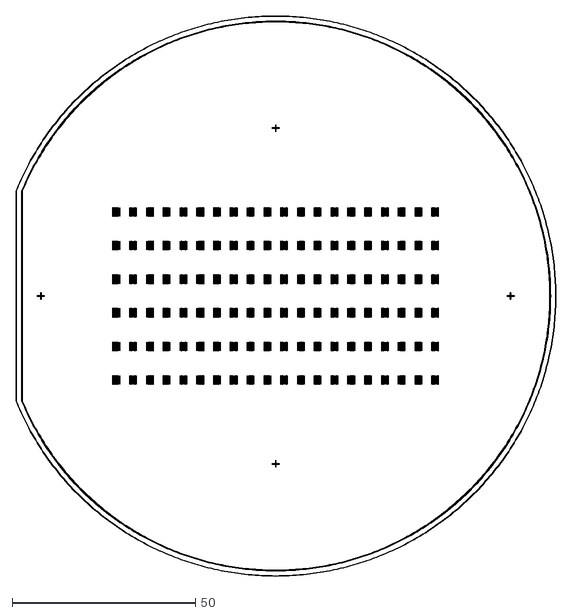
[picture p166: CAD file, 2025-10-20]
designs/open_chamber/2_compartment_192_well_300um_v22/2_compartment_96_well_300um_v22_bottom.dxf
147.4 x 153.0
