trissim/OpenMFD/designs/open_chamber/2_compartment_384_well_300um_suex100_v25/2_compartment_384_well_300um_suex100_v25_single_top.dxf

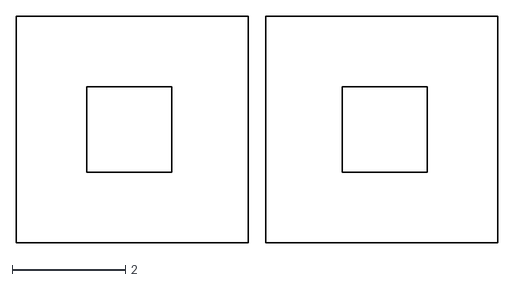
[picture p167: CAD file, 2025-10-20]
designs/open_chamber/2_compartment_384_well_300um_suex100_v25/2_compartment_384_well_300um_suex100_v25_single_top.dxf
8.50 x 4.00
