trissim/OpenMFD/designs/open_chamber/2_compartment_48_well_300um_v22/horizontal_well_test.dxf.dxf

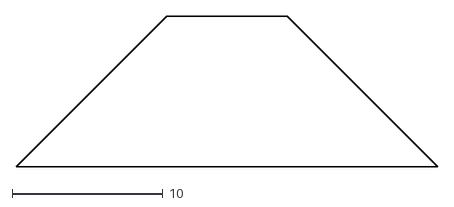
[picture p168: CAD file, 2025-10-20]
designs/open_chamber/2_compartment_48_well_300um_v22/horizontal_well_test.dxf.dxf
28.0 x 10.0
