trissim/OpenMFD/designs/open_chamber/2_compartment_4x4_300um_suex200_v27/2_compartment_4x4_300um_suex100_v27_single_aligned.dxf

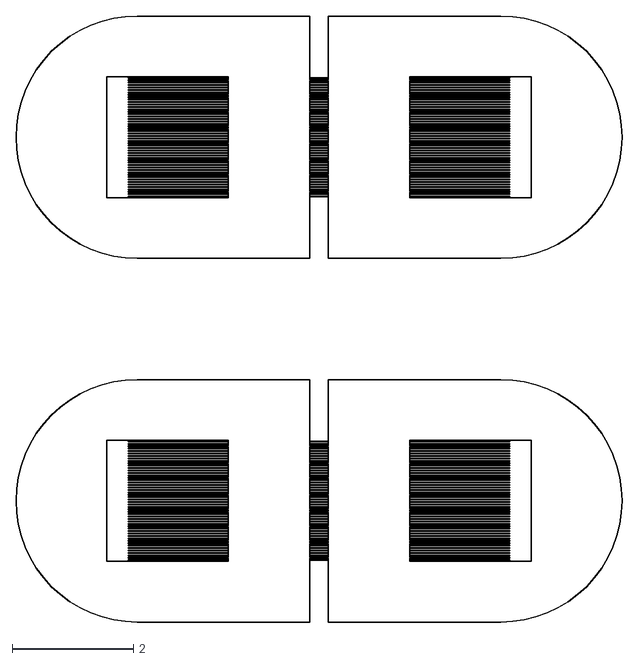
[picture p170: CAD file, 2025-10-20]
designs/open_chamber/2_compartment_4x4_300um_suex200_v27/2_compartment_4x4_300um_suex100_v27_single_aligned.dxf
10.0 x 10.0
