trissim/OpenMFD/designs/open_chamber/2_compartment_96_well_300um_suex100_v26/2_compartment_96_well_300um_suex100_v26_single_aligned.dxf

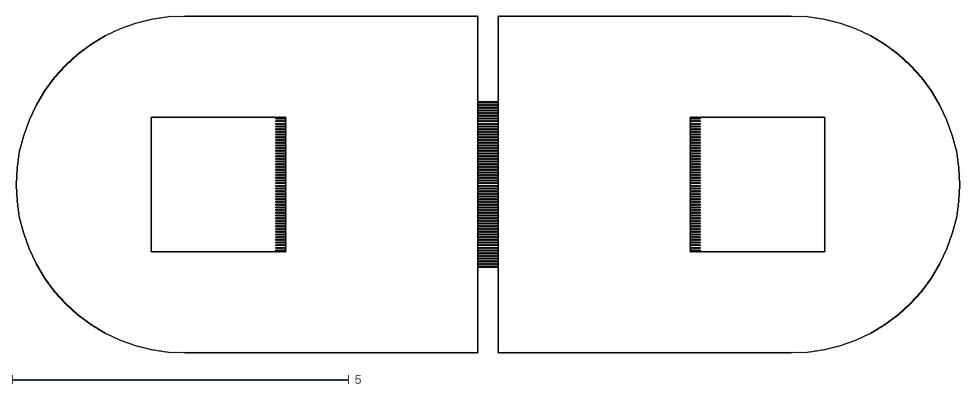
[picture p171: CAD file, 2025-10-20]
designs/open_chamber/2_compartment_96_well_300um_suex100_v26/2_compartment_96_well_300um_suex100_v26_single_aligned.dxf
14.0 x 5.00
