trissim/OpenMFD/designs/open_chamber/2_compartment_96_well_300um_suex200_v27/2_compartment_96_well_300um_suex200_v27_wells_insert.stl

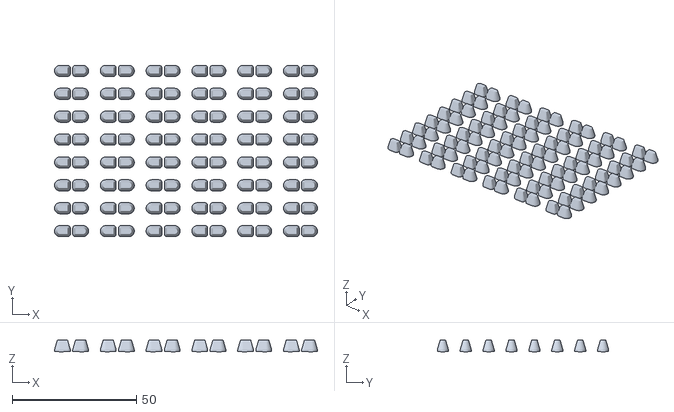
[picture p172: CAD file, 2026-04-28]
designs/open_chamber/2_compartment_96_well_300um_suex200_v27/2_compartment_96_well_300um_suex200_v27_wells_insert.stl
105.7 x 68.9 x 4.64
