trissim/OpenMFD/designs/open_chamber/2_compartment_96_well_300um_v21/2_compartment_96_well_300um_v21_single_bottom.dxf

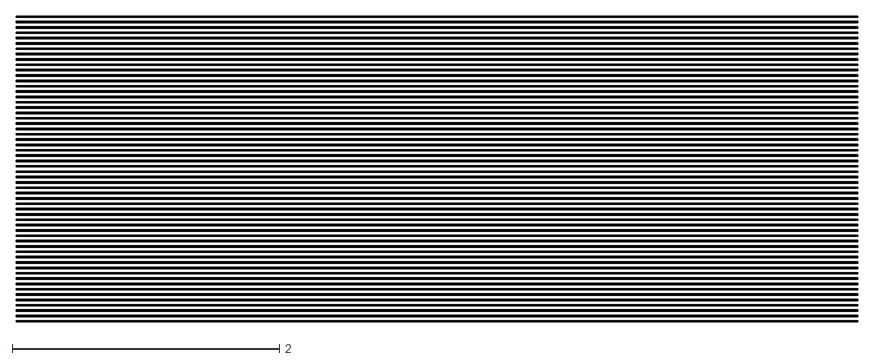
[picture p173: CAD file, 2025-10-20]
designs/open_chamber/2_compartment_96_well_300um_v21/2_compartment_96_well_300um_v21_single_bottom.dxf
6.30 x 2.29
