trissim/OpenMFD/designs/open_chamber/2compartment/devices_2compartment_multi_device_bottom.dxf

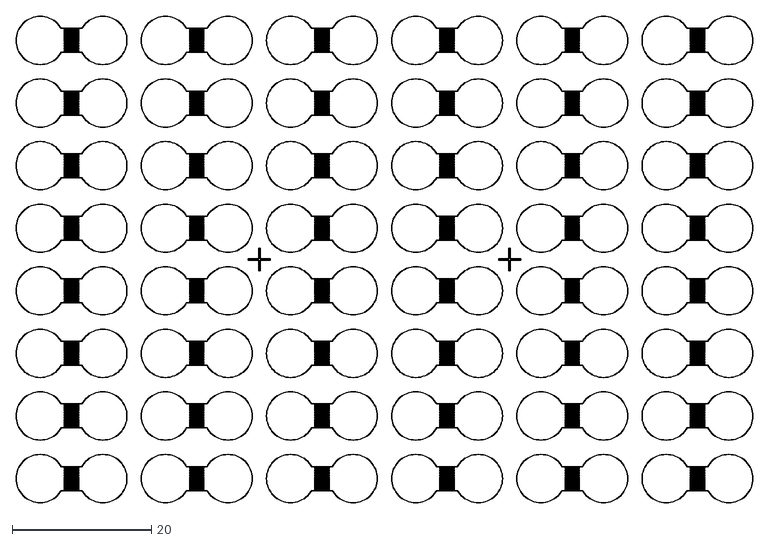
[picture p174: CAD file, 2025-10-20]
designs/open_chamber/2compartment/devices_2compartment_multi_device_bottom.dxf
105.9 x 69.9
