trissim/OpenMFD/designs/open_chamber/2compartment_96_well_inserts_v9_300um/2_compartment_96_well_300um_single_top.dxf

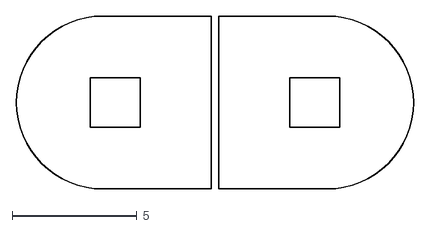
[picture p175: CAD file, 2025-10-20]
designs/open_chamber/2compartment_96_well_inserts_v9_300um/2_compartment_96_well_300um_single_top.dxf
15.9 x 6.94
