trissim/OpenMFD/designs/open_chamber/2compartment_duplicates_4x4_refactored_inserts_v10_1000um/2_compartment_4x4_1000um_v10_single_top.dxf

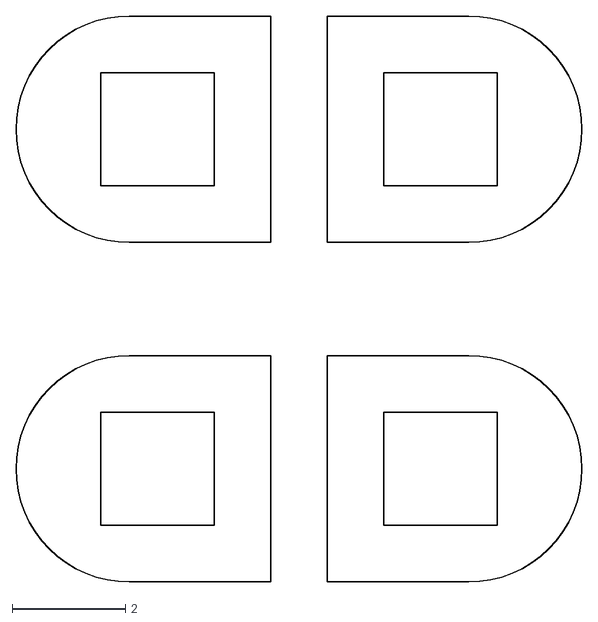
[picture p176: CAD file, 2025-10-20]
designs/open_chamber/2compartment_duplicates_4x4_refactored_inserts_v10_1000um/2_compartment_4x4_1000um_v10_single_top.dxf
10.0 x 10.0
