trissim/OpenMFD/designs/open_chamber/2compartment_duplicates_4x4_refactored_inserts_v11+_300um/2_compartment_4x4_300um_v11_aligned.dxf

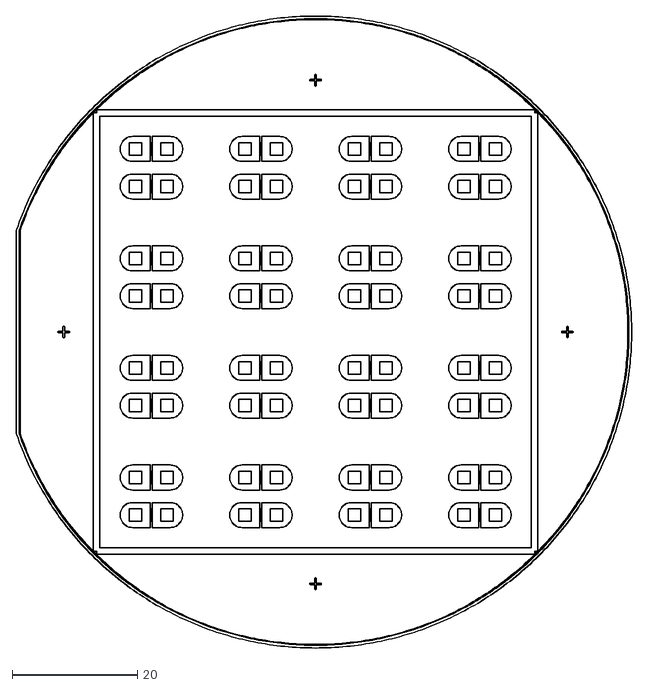
[picture p178: CAD file, 2025-10-20]
designs/open_chamber/2compartment_duplicates_4x4_refactored_inserts_v11+_300um/2_compartment_4x4_300um_v11_aligned.dxf
98.3 x 101.0
