trissim/OpenMFD/designs/open_chamber/3mm_pairs_5x5/wall_and_devices_3mm_pairs_5x5.dxf

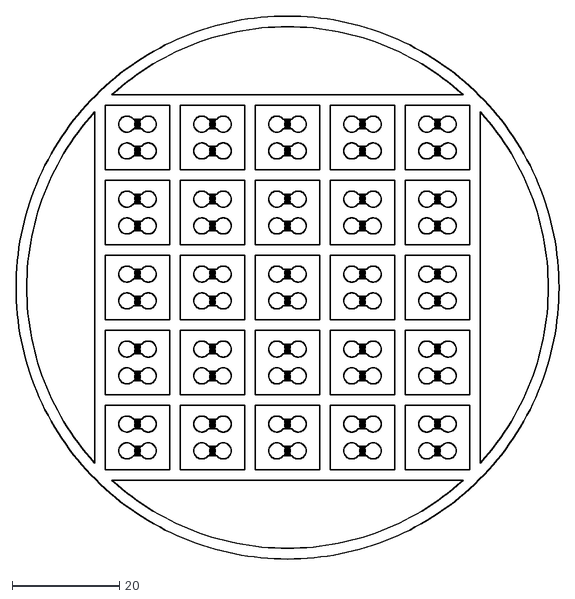
[picture p182: CAD file, 2025-10-20]
designs/open_chamber/3mm_pairs_5x5/wall_and_devices_3mm_pairs_5x5.dxf
101.4 x 101.4
