trissim/OpenMFD/designs/open_chamber/gradient_layout/2compartment_96_well_inserts_v9_1000um/2_compartment_96_well_1000um_top.dxf

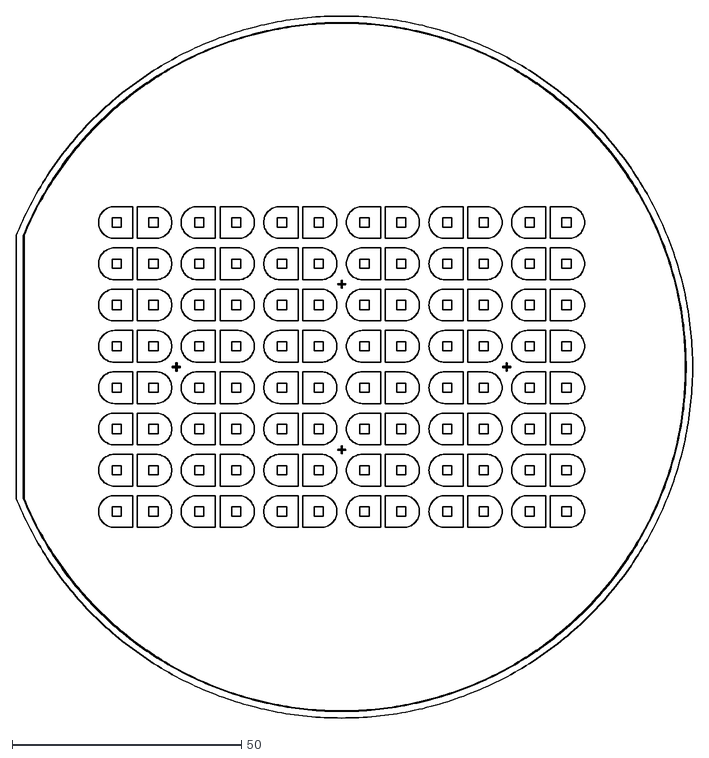
[picture p183: CAD file, 2025-10-20]
designs/open_chamber/gradient_layout/2compartment_96_well_inserts_v9_1000um/2_compartment_96_well_1000um_top.dxf
147.4 x 153.0
