trissim/OpenMFD/designs/open_chamber/gradient_layout/wall_gradient_multi_device.stl

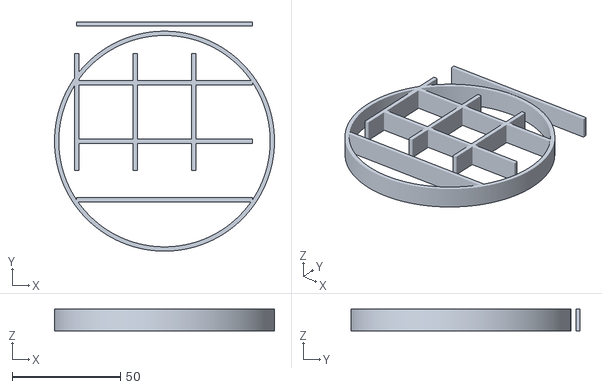
[picture p184: CAD file, 2025-10-20]
designs/open_chamber/gradient_layout/wall_gradient_multi_device.stl
101.4 x 105.7 x 10.0
