trissim/OpenMFD/orders/order oct_13_2022/closed_4x4_4mm/wall_closed_chamber_4mm_4x4.stl

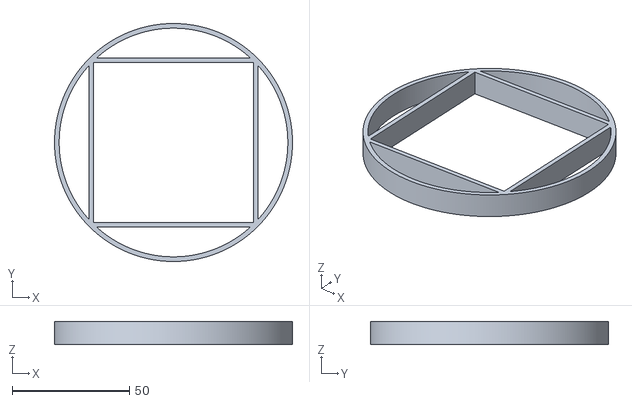
[picture p186: CAD file, 2025-10-20]
orders/order oct_13_2022/closed_4x4_4mm/wall_closed_chamber_4mm_4x4.stl
101.4 x 101.4 x 10.0
