trissim/OpenMFD/orders/order_dec_20_2023/2_compartment_96_well_300um_v11/wall_single_2_compartment_96_well_300um_v11.stl

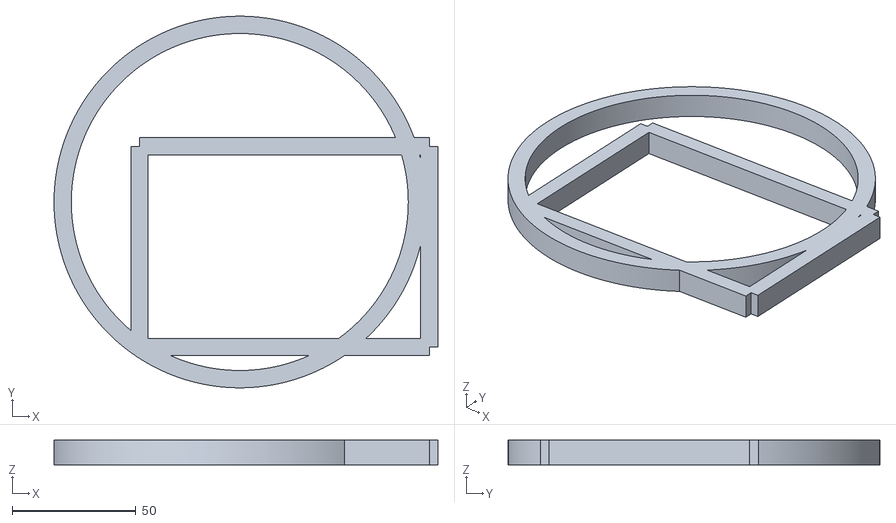
[picture p188: CAD file, 2025-10-20]
orders/order_dec_20_2023/2_compartment_96_well_300um_v11/wall_single_2_compartment_96_well_300um_v11.stl
155.0 x 150.0 x 10.0
