trissim/OpenMFD/orders/order_july25th_2024/2_compartment_96_well_300um_v17_wells_insert.stl

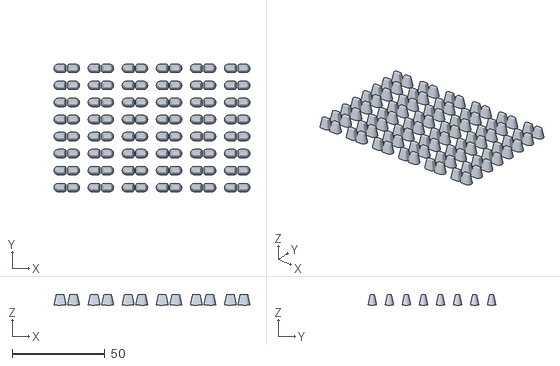
[picture p189: CAD file, 2025-10-20]
orders/order_july25th_2024/2_compartment_96_well_300um_v17_wells_insert.stl
105.9 x 69.1 x 5.74
