trissim/OpenMFD/orders/order_nov_2_2021/device_12_units_3mm_diameter.dxf

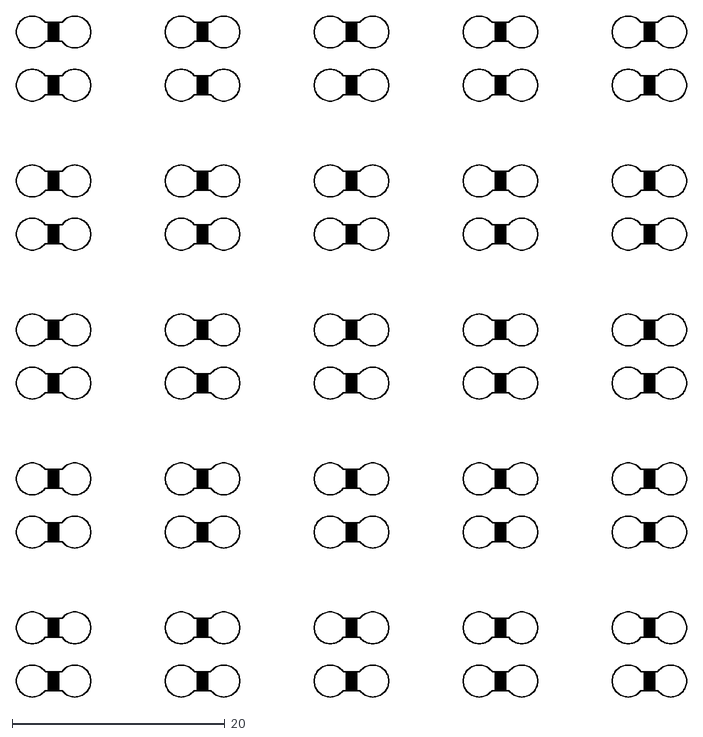
[picture p190: CAD file, 2025-10-20]
orders/order_nov_2_2021/device_12_units_3mm_diameter.dxf
63.0 x 64.0
