trissim/OpenMFD/orders/wafer_rack_send_cut_send_dec_9_2024/Wafer Rack 2 v5.step

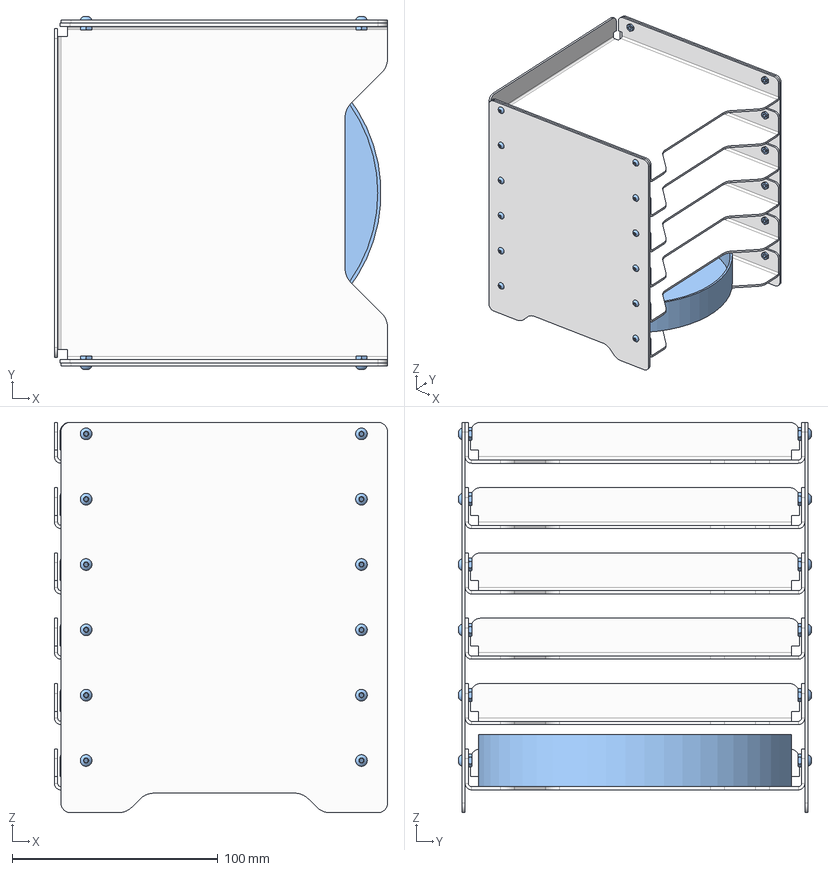
[picture p191: CAD file, 2025-10-20]
orders/wafer_rack_send_cut_send_dec_9_2024/Wafer Rack 2 v5.step
161.9 x 171.6 x 189.8 mm
Plate x 6
Wafer
Side
Broached Hexagon Socket Button Head Cap Screw ASME B18.3.4M - M3 x 0. 5 x 5 Steel Grade 2 Chrome v1 x 12
Broached Hexagon Socket Button Head Cap Screw ANSI B18.3.4M - M3 x 0. 5 x 5 Steel Grade 2 Chrome v1 x 12
Hexagon Thin Nut BS EN ISO 4035 - M3 Steel 6 Chrome v1 x 24
