trissim/OpenMFD/tests/open_duplicates_4mm_4x4_wells.stl

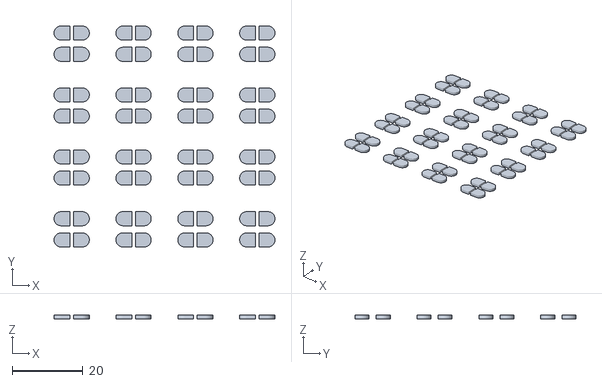
[picture p192: CAD file, 2025-10-20]
tests/open_duplicates_4mm_4x4_wells.stl
62.5 x 62.5 x 1.00
