trissim/OpenMFD/designs/closed_chamber/4x4/wall_closed_chamber_4x4_top.dxf

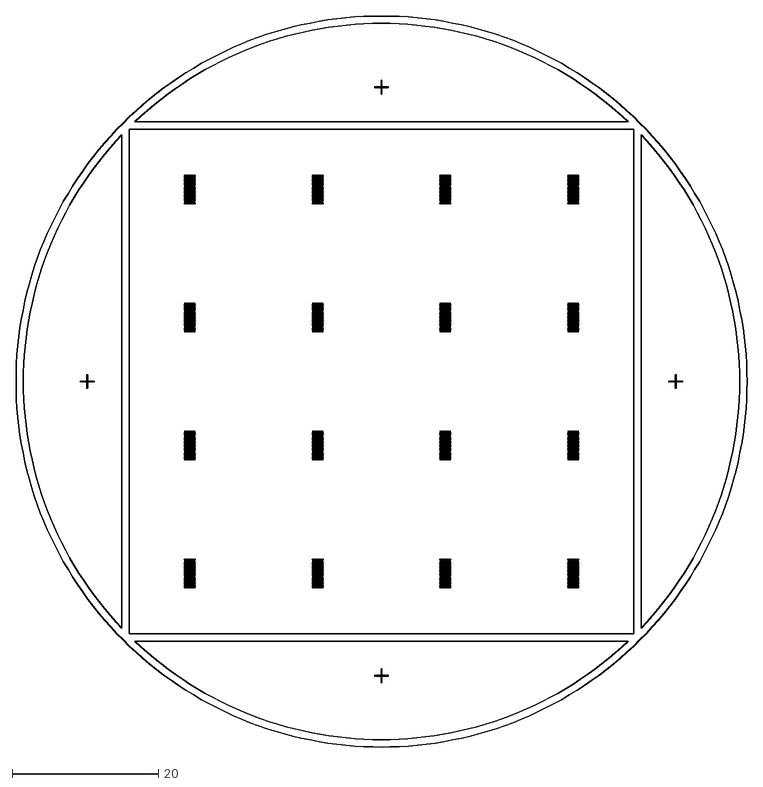
[picture p193: CAD file, 2025-10-20]
designs/closed_chamber/4x4/wall_closed_chamber_4x4_top.dxf
100.0 x 100.0
