trissim/OpenMFD/designs/open_chamber/2_compartment_154_well_300um_v21/2_compartment_96_well_300um_v21_single_aligned.dxf

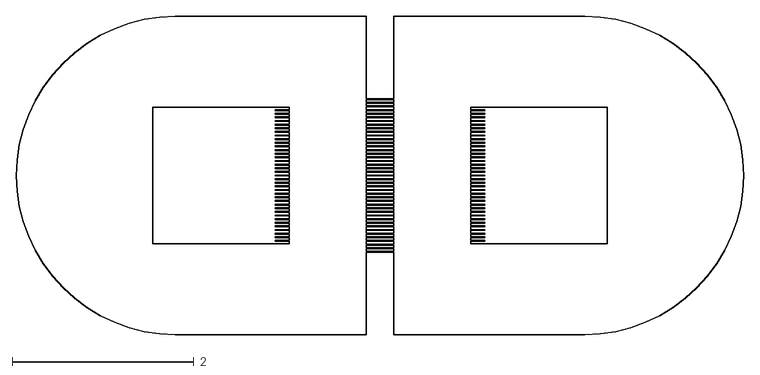
[picture p194: CAD file, 2025-10-20]
designs/open_chamber/2_compartment_154_well_300um_v21/2_compartment_96_well_300um_v21_single_aligned.dxf
8.00 x 3.50
