trissim/OpenMFD/designs/open_chamber/2_compartment_384_well_300um_suex100_v25/2_compartment_384_well_300um_suex100_v25_aligned.dxf

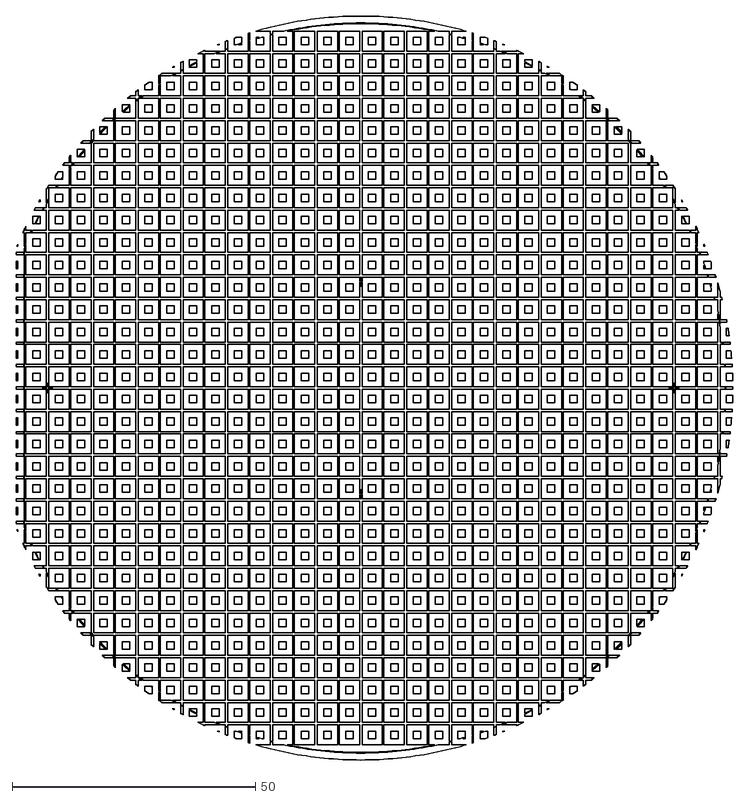
[picture p196: CAD file, 2025-10-20]
designs/open_chamber/2_compartment_384_well_300um_suex100_v25/2_compartment_384_well_300um_suex100_v25_aligned.dxf
147.4 x 153.0
