trissim/OpenMFD/designs/open_chamber/2_compartment_4x4_300um_suex100_v26/2_compartment_4x4_300um_suex100_v26_bottom.dxf

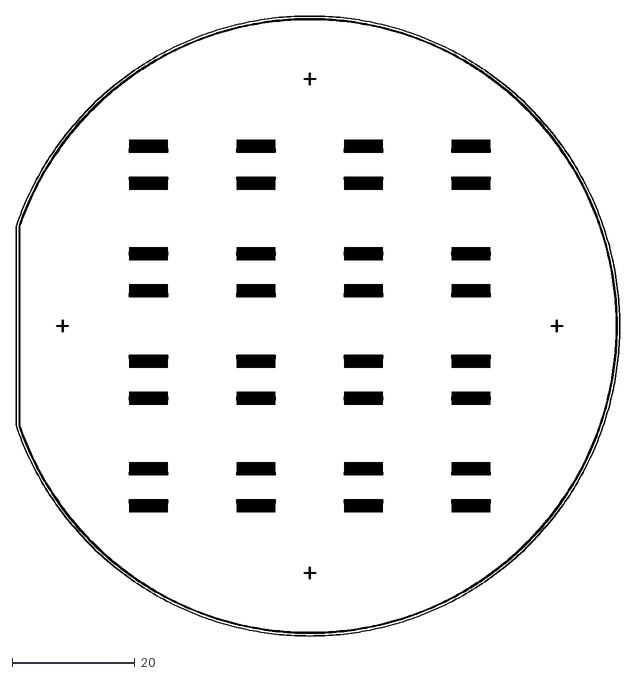
[picture p198: CAD file, 2025-10-20]
designs/open_chamber/2_compartment_4x4_300um_suex100_v26/2_compartment_4x4_300um_suex100_v26_bottom.dxf
98.3 x 101.0
