trissim/OpenMFD/designs/open_chamber/2_compartment_96_well_1000um_v10/wall_2_compartment_96_well_1000um_v10.stl

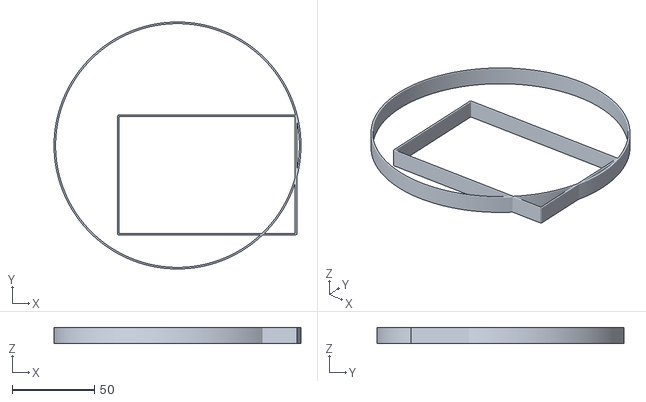
[picture p200: CAD file, 2025-10-20]
designs/open_chamber/2_compartment_96_well_1000um_v10/wall_2_compartment_96_well_1000um_v10.stl
150.0 x 150.0 x 10.0
