trissim/OpenMFD/designs/open_chamber/2_compartment_96_well_300um_suex100_v26/wafer.dxf

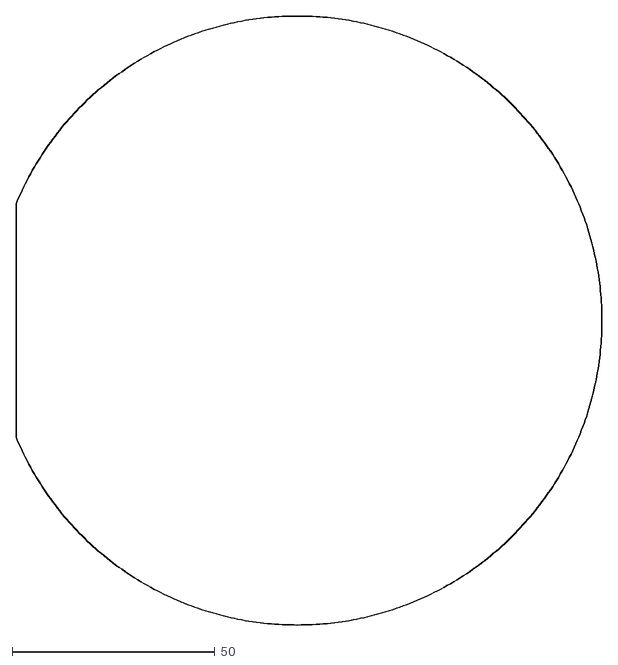
[picture p201: CAD file, 2025-10-20]
designs/open_chamber/2_compartment_96_well_300um_suex100_v26/wafer.dxf
144.3 x 150.0
