trissim/OpenMFD/designs/open_chamber/2compartment_96_well_inserts_v9_300um/2_compartment_96_well_300um_aligned.dxf

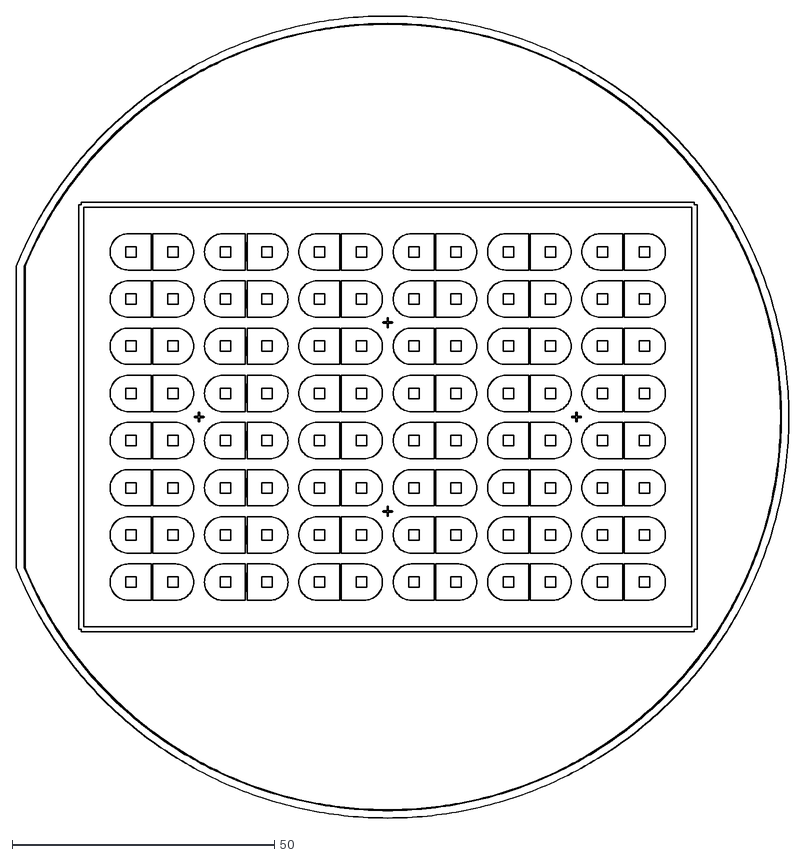
[picture p203: CAD file, 2025-10-20]
designs/open_chamber/2compartment_96_well_inserts_v9_300um/2_compartment_96_well_300um_aligned.dxf
147.4 x 153.0
