trissim/OpenMFD/designs/open_chamber/3compartment/devices_3compartment_multi_device_bottom.dxf

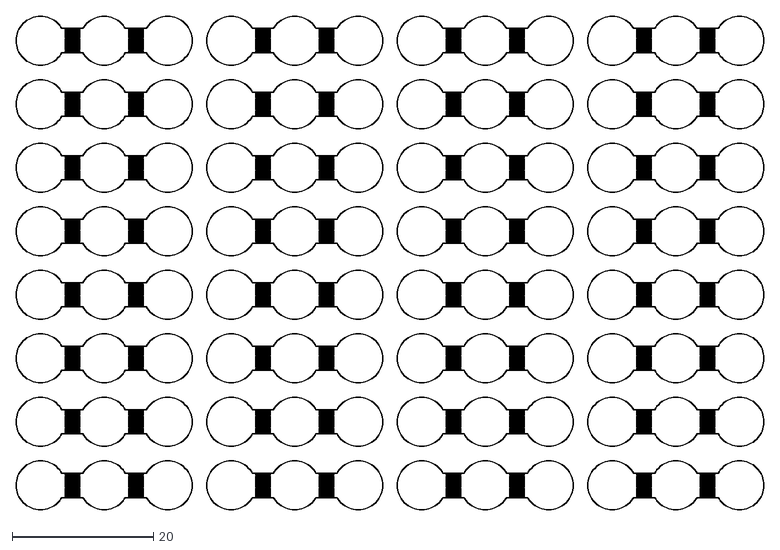
[picture p208: CAD file, 2025-10-20]
designs/open_chamber/3compartment/devices_3compartment_multi_device_bottom.dxf
105.9 x 69.9
