trissim/OpenMFD/designs/open_chamber/3mm_pairs_5x5/2compartment_many_single_device_top.dxf

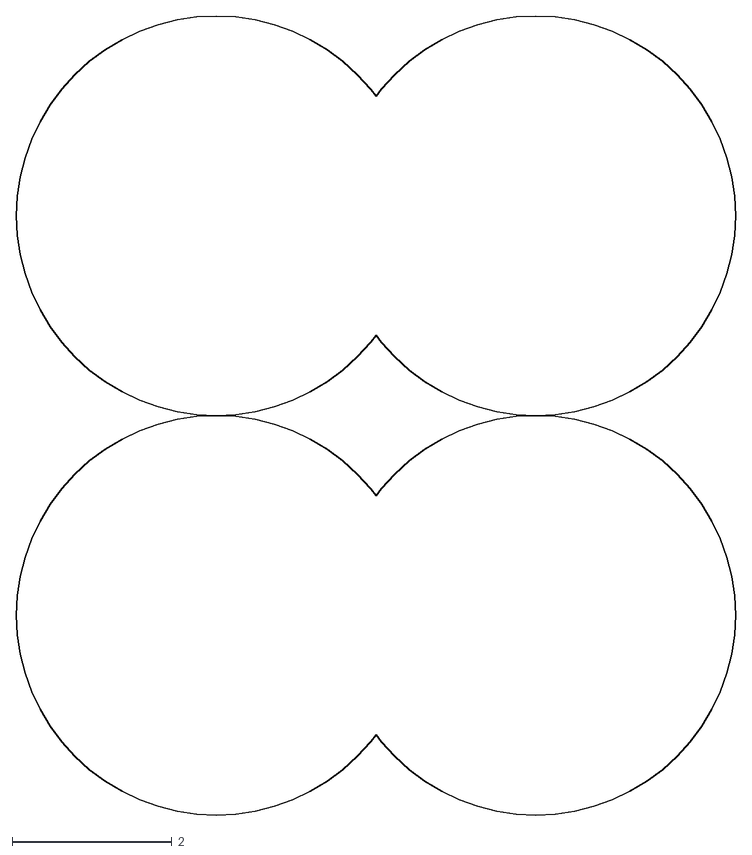
[picture p209: CAD file, 2025-10-20]
designs/open_chamber/3mm_pairs_5x5/2compartment_many_single_device_top.dxf
9.00 x 10.0
