trissim/OpenMFD/designs/open_chamber/gradient_layout/devices_gradient_single_device.dxf

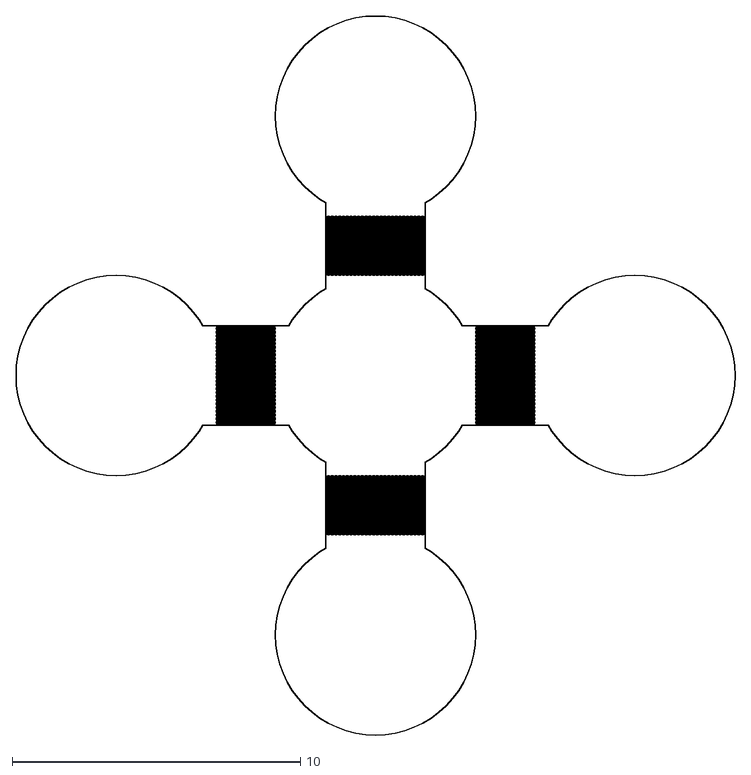
[picture p210: CAD file, 2025-10-20]
designs/open_chamber/gradient_layout/devices_gradient_single_device.dxf
24.9 x 24.9
