trissim/OpenMFD/designs/plasma_racks/4mm_well_0.5inch_diam_device_final_cnc/96_well_plate_reservoirs_almost_final_cnc.stl

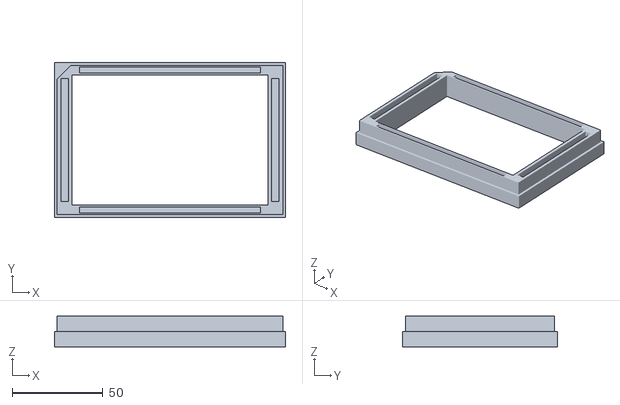
[picture p211: CAD file, 2025-10-20]
designs/plasma_racks/4mm_well_0.5inch_diam_device_final_cnc/96_well_plate_reservoirs_almost_final_cnc.stl
127.5 x 85.3 x 17.0
