trissim/OpenMFD/orders/order oct_13_2022/2compartment_96well_v2/2compartment_single_device_bottom.dxf

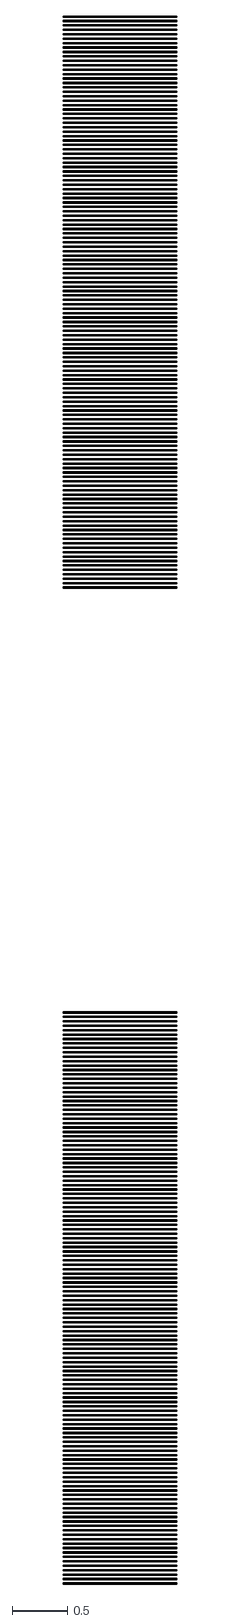
[picture p212: CAD file, 2025-10-20]
orders/order oct_13_2022/2compartment_96well_v2/2compartment_single_device_bottom.dxf
1.03 x 14.2
