trissim/OpenMFD/orders/order oct_13_2022/closed_4x4_4mm/closed_top.dxf

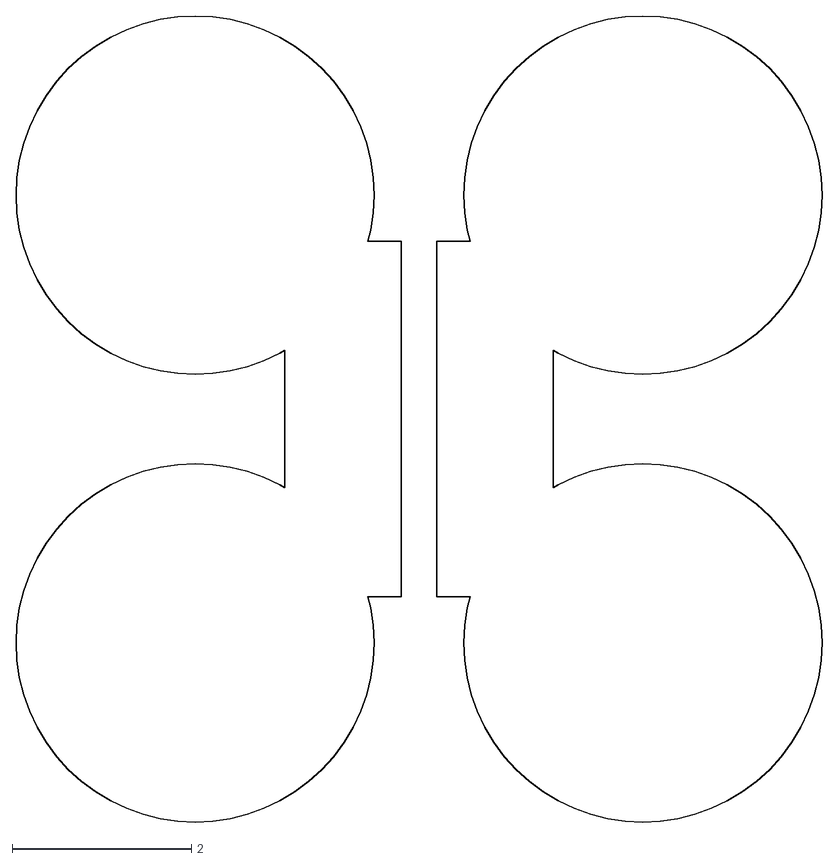
[picture p213: CAD file, 2025-10-20]
orders/order oct_13_2022/closed_4x4_4mm/closed_top.dxf
9.00 x 9.00
