trissim/OpenMFD/designs/open_chamber/2compartment_duplicates_4x4_refactored_inserts_v10_1000um_round_pin/2_compartment_4x4_1000um_v10_round_pin_aligned.scad

// Generated by SolidPython 1.1.3 on 2023-10-18 16:19:53


difference() {
	union() {
		difference() {
			translate(v = [-2.7500000000, -2.7500000000]) {
				translate(v = [35.0000000000, 35.0000000000]) {
					projection() {
						rotate(a = 90) {
							difference() {
								cylinder($fn = 512, h = 1, r1 = 50.5000000000, r2 = 50.5000000000);
								translate(v = [-16.2500000000, 47.8140931107, 0]) {
									cube(center = false, size = [32.5000000000, 2.6859068893, 1]);
								}
							}
						}
					}
				}
			}
			translate(v = [-2.7500000000, -2.7500000000]) {
				translate(v = [35.0000000000, 35.0000000000]) {
					projection() {
						rotate(a = 90) {
							difference() {
								cylinder($fn = 512, h = 1, r1 = 50.0750000000, r2 = 50.0750000000);
								translate(v = [-16.2500000000, 47.3649989444, 0]) {
									cube(center = false, size = [32.5000000000, 2.7100010556, 1]);
								}
							}
						}
					}
				}
			}
		}
		translate(v = [-2.7500000000, -2.7500000000]) {
			translate(v = [35.0000000000, 35.0000000000]) {
				projection() {
					rotate(a = 90) {
						difference() {
							cylinder($fn = 512, h = 1, r1 = 49.9250000000, r2 = 49.9250000000);
							translate(v = [-16.2500000000, 47.2063886037, 0]) {
								cube(center = false, size = [32.5000000000, 2.7186113963, 1]);
							}
						}
					}
				}
			}
		}
	}
	union() {
		translate(v = [-2.7500000000, -2.7500000000]) {
			union() {
				translate(v = [75.2500000000, 35.0000000000, 0]) {
					difference() {
						union() {
							translate(v = [0.1250000000, 0.1250000000, 0]) {
								translate(v = [0, 0, 0]) {
									rotate(a = 180) {
										union() {
											square(center = false, size = [1, 0.2500000000]);
											square(center = false, size = [0.2500000000, 1]);
										}
									}
								}
							}
							translate(v = [-0.1250000000, -0.1250000000, 0]) {
								translate(v = [0, 0, 0]) {
									rotate(a = 0) {
										union() {
											square(center = false, size = [1, 0.2500000000]);
											square(center = false, size = [0.2500000000, 1]);
										}
									}
								}
							}
						}
						union() {
							translate(v = [0.0625000000, 0.0625000000, 0]) {
								translate(v = [0, 0, 0]) {
									rotate(a = 180) {
										union() {
											square(center = false, size = [1, 0.1250000000]);
											square(center = false, size = [0.1250000000, 1]);
										}
									}
								}
							}
							translate(v = [-0.0625000000, -0.0625000000, 0]) {
								translate(v = [0, 0, 0]) {
									rotate(a = 0) {
										union() {
											square(center = false, size = [1, 0.1250000000]);
											square(center = false, size = [0.1250000000, 1]);
										}
									}
								}
							}
						}
					}
				}
				translate(v = [35.0000000000, 75.2500000000, 0]) {
					difference() {
						union() {
							translate(v = [0.1250000000, 0.1250000000, 0]) {
								translate(v = [0, 0, 0]) {
									rotate(a = 180) {
										union() {
											square(center = false, size = [1, 0.2500000000]);
											square(center = false, size = [0.2500000000, 1]);
										}
									}
								}
							}
							translate(v = [-0.1250000000, -0.1250000000, 0]) {
								translate(v = [0, 0, 0]) {
									rotate(a = 0) {
										union() {
											square(center = false, size = [1, 0.2500000000]);
											square(center = false, size = [0.2500000000, 1]);
										}
									}
								}
							}
						}
						union() {
							translate(v = [0.0625000000, 0.0625000000, 0]) {
								translate(v = [0, 0, 0]) {
									rotate(a = 180) {
										union() {
											square(center = false, size = [1, 0.1250000000]);
											square(center = false, size = [0.1250000000, 1]);
										}
									}
								}
							}
							translate(v = [-0.0625000000, -0.0625000000, 0]) {
								translate(v = [0, 0, 0]) {
									rotate(a = 0) {
										union() {
											square(center = false, size = [1, 0.1250000000]);
											square(center = false, size = [0.1250000000, 1]);
										}
									}
								}
							}
						}
					}
				}
				translate(v = [-5.2500000000, 35.0000000000, 0]) {
					difference() {
						union() {
							translate(v = [0.1250000000, 0.1250000000, 0]) {
								translate(v = [0, 0, 0]) {
									rotate(a = 180) {
										union() {
											square(center = false, size = [1, 0.2500000000]);
											square(center = false, size = [0.2500000000, 1]);
										}
									}
								}
							}
							translate(v = [-0.1250000000, -0.1250000000, 0]) {
								translate(v = [0, 0, 0]) {
									rotate(a = 0) {
										union() {
											square(center = false, size = [1, 0.2500000000]);
											square(center = false, size = [0.2500000000, 1]);
										}
									}
								}
							}
						}
						union() {
							translate(v = [0.0625000000, 0.0625000000, 0]) {
								translate(v = [0, 0, 0]) {
									rotate(a = 180) {
										union() {
											square(center = false, size = [1, 0.1250000000]);
											square(center = false, size = [0.1250000000, 1]);
										}
									}
								}
							}
							translate(v = [-0.0625000000, -0.0625000000, 0]) {
								translate(v = [0, 0, 0]) {
									rotate(a = 0) {
										union() {
											square(center = false, size = [1, 0.1250000000]);
											square(center = false, size = [0.1250000000, 1]);
										}
									}
								}
							}
						}
					}
				}
				translate(v = [35.0000000000, -5.2500000000, 0]) {
					difference() {
						union() {
							translate(v = [0.1250000000, 0.1250000000, 0]) {
								translate(v = [0, 0, 0]) {
									rotate(a = 180) {
										union() {
											square(center = false, size = [1, 0.2500000000]);
											square(center = false, size = [0.2500000000, 1]);
										}
									}
								}
							}
							translate(v = [-0.1250000000, -0.1250000000, 0]) {
								translate(v = [0, 0, 0]) {
									rotate(a = 0) {
										union() {
											square(center = false, size = [1, 0.2500000000]);
											square(center = false, size = [0.2500000000, 1]);
										}
									}
								}
							}
						}
						union() {
							translate(v = [0.0625000000, 0.0625000000, 0]) {
								translate(v = [0, 0, 0]) {
									rotate(a = 180) {
										union() {
											square(center = false, size = [1, 0.1250000000]);
											square(center = false, size = [0.1250000000, 1]);
										}
									}
								}
							}
							translate(v = [-0.0625000000, -0.0625000000, 0]) {
								translate(v = [0, 0, 0]) {
									rotate(a = 0) {
										union() {
											square(center = false, size = [1, 0.1250000000]);
											square(center = false, size = [0.1250000000, 1]);
										}
									}
								}
							}
						}
					}
				}
				translate(v = [2.7500000000, 2.7500000000]) {
					union() {
						translate(v = [0.0000000000, 0.0000000000]) {
							difference() {
								union() {
									translate(v = [0, 0]) {
										union() {
											translate(v = [6.0000000000, 3.0000000000, 0]) {
												rotate(a = 0) {
													union() {
														translate(v = [1.7500000000, 0]) {
															square(center = true, size = [2.5000000000, 4.0000000000]);
														}
														translate(v = [-1.7500000000, 0]) {
															square(center = true, size = [2.5000000000, 4.0000000000]);
														}
													}
												}
											}
											translate(v = [6.0000000000, 3.0000000000, 0]) {
												rotate(a = 0) {
													union() {
														translate(v = [3, 0]) {
															circle($fn = 64, r = 2);
														}
														translate(v = [-3, 0]) {
															circle($fn = 64, r = 2);
														}
													}
												}
											}
										}
									}
									translate(v = [0, 6]) {
										union() {
											translate(v = [6.0000000000, 3.0000000000, 0]) {
												rotate(a = 0) {
													union() {
														translate(v = [1.7500000000, 0]) {
															square(center = true, size = [2.5000000000, 4.0000000000]);
														}
														translate(v = [-1.7500000000, 0]) {
															square(center = true, size = [2.5000000000, 4.0000000000]);
														}
													}
												}
											}
											translate(v = [6.0000000000, 3.0000000000, 0]) {
												rotate(a = 0) {
													union() {
														translate(v = [3, 0]) {
															circle($fn = 64, r = 2);
														}
														translate(v = [-3, 0]) {
															circle($fn = 64, r = 2);
														}
													}
												}
											}
										}
									}
								}
								union() {
									translate(v = [0, 0]) {
										union() {
											translate(v = [6.0000000000, 3.0000000000, 0]) {
												rotate(a = 0) {
													union() {
														translate(v = [2.5000000000, 0]) {
															square(center = true, size = [2, 2]);
														}
														translate(v = [-2.5000000000, 0]) {
															square(center = true, size = [2, 2]);
														}
													}
												}
											}
										}
									}
									translate(v = [0, 6]) {
										union() {
											translate(v = [6.0000000000, 3.0000000000, 0]) {
												rotate(a = 0) {
													union() {
														translate(v = [2.5000000000, 0]) {
															square(center = true, size = [2, 2]);
														}
														translate(v = [-2.5000000000, 0]) {
															square(center = true, size = [2, 2]);
														}
													}
												}
											}
										}
									}
								}
							}
						}
						translate(v = [17.5000000000, 0.0000000000]) {
							difference() {
								union() {
									translate(v = [0, 0]) {
										union() {
											translate(v = [6.0000000000, 3.0000000000, 0]) {
												rotate(a = 0) {
													union() {
														translate(v = [1.7500000000, 0]) {
															square(center = true, size = [2.5000000000, 4.0000000000]);
														}
														translate(v = [-1.7500000000, 0]) {
															square(center = true, size = [2.5000000000, 4.0000000000]);
														}
													}
												}
											}
											translate(v = [6.0000000000, 3.0000000000, 0]) {
												rotate(a = 0) {
													union() {
														translate(v = [3, 0]) {
															circle($fn = 64, r = 2);
														}
														translate(v = [-3, 0]) {
															circle($fn = 64, r = 2);
														}
													}
												}
											}
										}
									}
									translate(v = [0, 6]) {
										union() {
											translate(v = [6.0000000000, 3.0000000000, 0]) {
												rotate(a = 0) {
													union() {
														translate(v = [1.7500000000, 0]) {
															square(center = true, size = [2.5000000000, 4.0000000000]);
														}
														translate(v = [-1.7500000000, 0]) {
															square(center = true, size = [2.5000000000, 4.0000000000]);
														}
													}
												}
											}
											translate(v = [6.0000000000, 3.0000000000, 0]) {
												rotate(a = 0) {
													union() {
														translate(v = [3, 0]) {
															circle($fn = 64, r = 2);
														}
														translate(v = [-3, 0]) {
															circle($fn = 64, r = 2);
														}
													}
												}
											}
										}
									}
								}
								union() {
									translate(v = [0, 0]) {
										union() {
											translate(v = [6.0000000000, 3.0000000000, 0]) {
												rotate(a = 0) {
													union() {
														translate(v = [2.5000000000, 0]) {
															square(center = true, size = [2, 2]);
														}
														translate(v = [-2.5000000000, 0]) {
															square(center = true, size = [2, 2]);
														}
													}
												}
											}
										}
									}
									translate(v = [0, 6]) {
										union() {
											translate(v = [6.0000000000, 3.0000000000, 0]) {
												rotate(a = 0) {
													union() {
														translate(v = [2.5000000000, 0]) {
															square(center = true, size = [2, 2]);
														}
														translate(v = [-2.5000000000, 0]) {
															square(center = true, size = [2, 2]);
														}
													}
												}
											}
										}
									}
								}
							}
						}
						translate(v = [35.0000000000, 0.0000000000]) {
							difference() {
								union() {
									translate(v = [0, 0]) {
										union() {
											translate(v = [6.0000000000, 3.0000000000, 0]) {
												rotate(a = 0) {
													union() {
														translate(v = [1.7500000000, 0]) {
															square(center = true, size = [2.5000000000, 4.0000000000]);
														}
														translate(v = [-1.7500000000, 0]) {
															square(center = true, size = [2.5000000000, 4.0000000000]);
														}
													}
												}
											}
											translate(v = [6.0000000000, 3.0000000000, 0]) {
												rotate(a = 0) {
													union() {
														translate(v = [3, 0]) {
															circle($fn = 64, r = 2);
														}
														translate(v = [-3, 0]) {
															circle($fn = 64, r = 2);
														}
													}
												}
											}
										}
									}
									translate(v = [0, 6]) {
										union() {
											translate(v = [6.0000000000, 3.0000000000, 0]) {
												rotate(a = 0) {
													union() {
														translate(v = [1.7500000000, 0]) {
															square(center = true, size = [2.5000000000, 4.0000000000]);
														}
														translate(v = [-1.7500000000, 0]) {
															square(center = true, size = [2.5000000000, 4.0000000000]);
														}
													}
												}
											}
											translate(v = [6.0000000000, 3.0000000000, 0]) {
												rotate(a = 0) {
													union() {
														translate(v = [3, 0]) {
															circle($fn = 64, r = 2);
														}
														translate(v = [-3, 0]) {
															circle($fn = 64, r = 2);
														}
													}
												}
											}
										}
									}
								}
								union() {
									translate(v = [0, 0]) {
										union() {
											translate(v = [6.0000000000, 3.0000000000, 0]) {
												rotate(a = 0) {
													union() {
														translate(v = [2.5000000000, 0]) {
															square(center = true, size = [2, 2]);
														}
														translate(v = [-2.5000000000, 0]) {
															square(center = true, size = [2, 2]);
														}
													}
												}
											}
										}
									}
									translate(v = [0, 6]) {
										union() {
											translate(v = [6.0000000000, 3.0000000000, 0]) {
												rotate(a = 0) {
													union() {
														translate(v = [2.5000000000, 0]) {
															square(center = true, size = [2, 2]);
														}
														translate(v = [-2.5000000000, 0]) {
															square(center = true, size = [2, 2]);
														}
													}
												}
											}
										}
									}
								}
							}
						}
						translate(v = [52.5000000000, 0.0000000000]) {
							difference() {
								union() {
									translate(v = [0, 0]) {
										union() {
											translate(v = [6.0000000000, 3.0000000000, 0]) {
												rotate(a = 0) {
													union() {
														translate(v = [1.7500000000, 0]) {
															square(center = true, size = [2.5000000000, 4.0000000000]);
														}
														translate(v = [-1.7500000000, 0]) {
															square(center = true, size = [2.5000000000, 4.0000000000]);
														}
													}
												}
											}
											translate(v = [6.0000000000, 3.0000000000, 0]) {
												rotate(a = 0) {
													union() {
														translate(v = [3, 0]) {
															circle($fn = 64, r = 2);
														}
														translate(v = [-3, 0]) {
															circle($fn = 64, r = 2);
														}
													}
												}
											}
										}
									}
									translate(v = [0, 6]) {
										union() {
											translate(v = [6.0000000000, 3.0000000000, 0]) {
												rotate(a = 0) {
													union() {
														translate(v = [1.7500000000, 0]) {
															square(center = true, size = [2.5000000000, 4.0000000000]);
														}
														translate(v = [-1.7500000000, 0]) {
															square(center = true, size = [2.5000000000, 4.0000000000]);
														}
													}
												}
											}
											translate(v = [6.0000000000, 3.0000000000, 0]) {
												rotate(a = 0) {
													union() {
														translate(v = [3, 0]) {
															circle($fn = 64, r = 2);
														}
														translate(v = [-3, 0]) {
															circle($fn = 64, r = 2);
														}
													}
												}
											}
										}
									}
								}
								union() {
									translate(v = [0, 0]) {
										union() {
											translate(v = [6.0000000000, 3.0000000000, 0]) {
												rotate(a = 0) {
													union() {
														translate(v = [2.5000000000, 0]) {
															square(center = true, size = [2, 2]);
														}
														translate(v = [-2.5000000000, 0]) {
															square(center = true, size = [2, 2]);
														}
													}
												}
											}
										}
									}
									translate(v = [0, 6]) {
										union() {
											translate(v = [6.0000000000, 3.0000000000, 0]) {
												rotate(a = 0) {
													union() {
														translate(v = [2.5000000000, 0]) {
															square(center = true, size = [2, 2]);
														}
														translate(v = [-2.5000000000, 0]) {
															square(center = true, size = [2, 2]);
														}
													}
												}
											}
										}
									}
								}
							}
						}
						translate(v = [0.0000000000, 17.5000000000]) {
							difference() {
								union() {
									translate(v = [0, 0]) {
										union() {
											translate(v = [6.0000000000, 3.0000000000, 0]) {
												rotate(a = 0) {
													union() {
														translate(v = [1.7500000000, 0]) {
															square(center = true, size = [2.5000000000, 4.0000000000]);
														}
														translate(v = [-1.7500000000, 0]) {
															square(center = true, size = [2.5000000000, 4.0000000000]);
														}
													}
												}
											}
											translate(v = [6.0000000000, 3.0000000000, 0]) {
												rotate(a = 0) {
													union() {
														translate(v = [3, 0]) {
															circle($fn = 64, r = 2);
														}
														translate(v = [-3, 0]) {
															circle($fn = 64, r = 2);
														}
													}
												}
											}
										}
									}
									translate(v = [0, 6]) {
										union() {
											translate(v = [6.0000000000, 3.0000000000, 0]) {
												rotate(a = 0) {
													union() {
														translate(v = [1.7500000000, 0]) {
															square(center = true, size = [2.5000000000, 4.0000000000]);
														}
														translate(v = [-1.7500000000, 0]) {
															square(center = true, size = [2.5000000000, 4.0000000000]);
														}
													}
												}
											}
											translate(v = [6.0000000000, 3.0000000000, 0]) {
												rotate(a = 0) {
													union() {
														translate(v = [3, 0]) {
															circle($fn = 64, r = 2);
														}
														translate(v = [-3, 0]) {
															circle($fn = 64, r = 2);
														}
													}
												}
											}
										}
									}
								}
								union() {
									translate(v = [0, 0]) {
										union() {
											translate(v = [6.0000000000, 3.0000000000, 0]) {
												rotate(a = 0) {
													union() {
														translate(v = [2.5000000000, 0]) {
															square(center = true, size = [2, 2]);
														}
														translate(v = [-2.5000000000, 0]) {
															square(center = true, size = [2, 2]);
														}
													}
												}
											}
										}
									}
									translate(v = [0, 6]) {
										union() {
											translate(v = [6.0000000000, 3.0000000000, 0]) {
												rotate(a = 0) {
													union() {
														translate(v = [2.5000000000, 0]) {
															square(center = true, size = [2, 2]);
														}
														translate(v = [-2.5000000000, 0]) {
															square(center = true, size = [2, 2]);
														}
													}
												}
											}
										}
									}
								}
							}
						}
						translate(v = [17.5000000000, 17.5000000000]) {
							difference() {
								union() {
									translate(v = [0, 0]) {
										union() {
											translate(v = [6.0000000000, 3.0000000000, 0]) {
												rotate(a = 0) {
													union() {
														translate(v = [1.7500000000, 0]) {
															square(center = true, size = [2.5000000000, 4.0000000000]);
														}
														translate(v = [-1.7500000000, 0]) {
															square(center = true, size = [2.5000000000, 4.0000000000]);
														}
													}
												}
											}
											translate(v = [6.0000000000, 3.0000000000, 0]) {
												rotate(a = 0) {
													union() {
														translate(v = [3, 0]) {
															circle($fn = 64, r = 2);
														}
														translate(v = [-3, 0]) {
															circle($fn = 64, r = 2);
														}
													}
												}
											}
										}
									}
									translate(v = [0, 6]) {
										union() {
											translate(v = [6.0000000000, 3.0000000000, 0]) {
												rotate(a = 0) {
													union() {
														translate(v = [1.7500000000, 0]) {
															square(center = true, size = [2.5000000000, 4.0000000000]);
														}
														translate(v = [-1.7500000000, 0]) {
															square(center = true, size = [2.5000000000, 4.0000000000]);
														}
													}
												}
											}
											translate(v = [6.0000000000, 3.0000000000, 0]) {
												rotate(a = 0) {
													union() {
														translate(v = [3, 0]) {
															circle($fn = 64, r = 2);
														}
														translate(v = [-3, 0]) {
															circle($fn = 64, r = 2);
														}
													}
												}
											}
										}
									}
								}
								union() {
									translate(v = [0, 0]) {
										union() {
											translate(v = [6.0000000000, 3.0000000000, 0]) {
												rotate(a = 0) {
													union() {
														translate(v = [2.5000000000, 0]) {
															square(center = true, size = [2, 2]);
														}
														translate(v = [-2.5000000000, 0]) {
															square(center = true, size = [2, 2]);
														}
													}
												}
											}
										}
									}
									translate(v = [0, 6]) {
										union() {
											translate(v = [6.0000000000, 3.0000000000, 0]) {
												rotate(a = 0) {
													union() {
														translate(v = [2.5000000000, 0]) {
															square(center = true, size = [2, 2]);
														}
														translate(v = [-2.5000000000, 0]) {
															square(center = true, size = [2, 2]);
														}
													}
												}
											}
										}
									}
								}
							}
						}
						translate(v = [35.0000000000, 17.5000000000]) {
							difference() {
								union() {
									translate(v = [0, 0]) {
										union() {
											translate(v = [6.0000000000, 3.0000000000, 0]) {
												rotate(a = 0) {
													union() {
														translate(v = [1.7500000000, 0]) {
															square(center = true, size = [2.5000000000, 4.0000000000]);
														}
														translate(v = [-1.7500000000, 0]) {
															square(center = true, size = [2.5000000000, 4.0000000000]);
														}
													}
												}
											}
											translate(v = [6.0000000000, 3.0000000000, 0]) {
												rotate(a = 0) {
													union() {
														translate(v = [3, 0]) {
															circle($fn = 64, r = 2);
														}
														translate(v = [-3, 0]) {
															circle($fn = 64, r = 2);
														}
													}
												}
											}
										}
									}
									translate(v = [0, 6]) {
										union() {
											translate(v = [6.0000000000, 3.0000000000, 0]) {
												rotate(a = 0) {
													union() {
														translate(v = [1.7500000000, 0]) {
															square(center = true, size = [2.5000000000, 4.0000000000]);
														}
														translate(v = [-1.7500000000, 0]) {
															square(center = true, size = [2.5000000000, 4.0000000000]);
														}
													}
												}
											}
											translate(v = [6.0000000000, 3.0000000000, 0]) {
												rotate(a = 0) {
													union() {
														translate(v = [3, 0]) {
															circle($fn = 64, r = 2);
														}
														translate(v = [-3, 0]) {
															circle($fn = 64, r = 2);
														}
													}
												}
											}
										}
									}
								}
								union() {
									translate(v = [0, 0]) {
										union() {
											translate(v = [6.0000000000, 3.0000000000, 0]) {
												rotate(a = 0) {
													union() {
														translate(v = [2.5000000000, 0]) {
															square(center = true, size = [2, 2]);
														}
														translate(v = [-2.5000000000, 0]) {
															square(center = true, size = [2, 2]);
														}
													}
												}
											}
										}
									}
									translate(v = [0, 6]) {
										union() {
											translate(v = [6.0000000000, 3.0000000000, 0]) {
												rotate(a = 0) {
													union() {
														translate(v = [2.5000000000, 0]) {
															square(center = true, size = [2, 2]);
														}
														translate(v = [-2.5000000000, 0]) {
															square(center = true, size = [2, 2]);
														}
													}
												}
											}
										}
									}
								}
							}
						}
						translate(v = [52.5000000000, 17.5000000000]) {
							difference() {
								union() {
									translate(v = [0, 0]) {
										union() {
											translate(v = [6.0000000000, 3.0000000000, 0]) {
												rotate(a = 0) {
													union() {
														translate(v = [1.7500000000, 0]) {
															square(center = true, size = [2.5000000000, 4.0000000000]);
														}
														translate(v = [-1.7500000000, 0]) {
															square(center = true, size = [2.5000000000, 4.0000000000]);
														}
													}
												}
											}
											translate(v = [6.0000000000, 3.0000000000, 0]) {
												rotate(a = 0) {
													union() {
														translate(v = [3, 0]) {
															circle($fn = 64, r = 2);
														}
														translate(v = [-3, 0]) {
															circle($fn = 64, r = 2);
														}
													}
												}
											}
										}
									}
									translate(v = [0, 6]) {
										union() {
											translate(v = [6.0000000000, 3.0000000000, 0]) {
												rotate(a = 0) {
													union() {
														translate(v = [1.7500000000, 0]) {
															square(center = true, size = [2.5000000000, 4.0000000000]);
														}
														translate(v = [-1.7500000000, 0]) {
															square(center = true, size = [2.5000000000, 4.0000000000]);
														}
													}
												}
											}
											translate(v = [6.0000000000, 3.0000000000, 0]) {
												rotate(a = 0) {
													union() {
														translate(v = [3, 0]) {
															circle($fn = 64, r = 2);
														}
														translate(v = [-3, 0]) {
															circle($fn = 64, r = 2);
														}
													}
												}
											}
										}
									}
								}
								union() {
									translate(v = [0, 0]) {
										union() {
											translate(v = [6.0000000000, 3.0000000000, 0]) {
												rotate(a = 0) {
													union() {
														translate(v = [2.5000000000, 0]) {
															square(center = true, size = [2, 2]);
														}
														translate(v = [-2.5000000000, 0]) {
															square(center = true, size = [2, 2]);
														}
													}
												}
											}
										}
									}
									translate(v = [0, 6]) {
										union() {
											translate(v = [6.0000000000, 3.0000000000, 0]) {
												rotate(a = 0) {
													union() {
														translate(v = [2.5000000000, 0]) {
															square(center = true, size = [2, 2]);
														}
														translate(v = [-2.5000000000, 0]) {
															square(center = true, size = [2, 2]);
														}
													}
												}
											}
										}
									}
								}
							}
						}
						translate(v = [0.0000000000, 35.0000000000]) {
							difference() {
								union() {
									translate(v = [0, 0]) {
										union() {
											translate(v = [6.0000000000, 3.0000000000, 0]) {
												rotate(a = 0) {
													union() {
														translate(v = [1.7500000000, 0]) {
															square(center = true, size = [2.5000000000, 4.0000000000]);
														}
														translate(v = [-1.7500000000, 0]) {
															square(center = true, size = [2.5000000000, 4.0000000000]);
														}
													}
												}
											}
											translate(v = [6.0000000000, 3.0000000000, 0]) {
												rotate(a = 0) {
													union() {
														translate(v = [3, 0]) {
															circle($fn = 64, r = 2);
														}
														translate(v = [-3, 0]) {
															circle($fn = 64, r = 2);
														}
													}
												}
											}
										}
									}
									translate(v = [0, 6]) {
										union() {
											translate(v = [6.0000000000, 3.0000000000, 0]) {
												rotate(a = 0) {
													union() {
														translate(v = [1.7500000000, 0]) {
															square(center = true, size = [2.5000000000, 4.0000000000]);
														}
														translate(v = [-1.7500000000, 0]) {
															square(center = true, size = [2.5000000000, 4.0000000000]);
														}
													}
												}
											}
											translate(v = [6.0000000000, 3.0000000000, 0]) {
												rotate(a = 0) {
													union() {
														translate(v = [3, 0]) {
															circle($fn = 64, r = 2);
														}
														translate(v = [-3, 0]) {
															circle($fn = 64, r = 2);
														}
													}
												}
											}
										}
									}
								}
								union() {
									translate(v = [0, 0]) {
										union() {
											translate(v = [6.0000000000, 3.0000000000, 0]) {
												rotate(a = 0) {
													union() {
														translate(v = [2.5000000000, 0]) {
															square(center = true, size = [2, 2]);
														}
														translate(v = [-2.5000000000, 0]) {
															square(center = true, size = [2, 2]);
														}
													}
												}
											}
										}
									}
									translate(v = [0, 6]) {
										union() {
											translate(v = [6.0000000000, 3.0000000000, 0]) {
												rotate(a = 0) {
													union() {
														translate(v = [2.5000000000, 0]) {
															square(center = true, size = [2, 2]);
														}
														translate(v = [-2.5000000000, 0]) {
															square(center = true, size = [2, 2]);
														}
													}
												}
											}
										}
									}
								}
							}
						}
						translate(v = [17.5000000000, 35.0000000000]) {
							difference() {
								union() {
									translate(v = [0, 0]) {
										union() {
											translate(v = [6.0000000000, 3.0000000000, 0]) {
												rotate(a = 0) {
													union() {
														translate(v = [1.7500000000, 0]) {
															square(center = true, size = [2.5000000000, 4.0000000000]);
														}
														translate(v = [-1.7500000000, 0]) {
															square(center = true, size = [2.5000000000, 4.0000000000]);
														}
													}
												}
											}
											translate(v = [6.0000000000, 3.0000000000, 0]) {
												rotate(a = 0) {
													union() {
														translate(v = [3, 0]) {
															circle($fn = 64, r = 2);
														}
														translate(v = [-3, 0]) {
															circle($fn = 64, r = 2);
														}
													}
												}
											}
										}
									}
									translate(v = [0, 6]) {
										union() {
											translate(v = [6.0000000000, 3.0000000000, 0]) {
												rotate(a = 0) {
													union() {
														translate(v = [1.7500000000, 0]) {
															square(center = true, size = [2.5000000000, 4.0000000000]);
														}
														translate(v = [-1.7500000000, 0]) {
															square(center = true, size = [2.5000000000, 4.0000000000]);
														}
													}
												}
											}
											translate(v = [6.0000000000, 3.0000000000, 0]) {
												rotate(a = 0) {
													union() {
														translate(v = [3, 0]) {
															circle($fn = 64, r = 2);
														}
														translate(v = [-3, 0]) {
															circle($fn = 64, r = 2);
														}
													}
												}
											}
										}
									}
								}
								union() {
									translate(v = [0, 0]) {
										union() {
											translate(v = [6.0000000000, 3.0000000000, 0]) {
												rotate(a = 0) {
													union() {
														translate(v = [2.5000000000, 0]) {
															square(center = true, size = [2, 2]);
														}
														translate(v = [-2.5000000000, 0]) {
															square(center = true, size = [2, 2]);
														}
													}
												}
											}
										}
									}
									translate(v = [0, 6]) {
										union() {
											translate(v = [6.0000000000, 3.0000000000, 0]) {
												rotate(a = 0) {
													union() {
														translate(v = [2.5000000000, 0]) {
															square(center = true, size = [2, 2]);
														}
														translate(v = [-2.5000000000, 0]) {
															square(center = true, size = [2, 2]);
														}
													}
												}
											}
										}
									}
								}
							}
						}
						translate(v = [35.0000000000, 35.0000000000]) {
							difference() {
								union() {
									translate(v = [0, 0]) {
										union() {
											translate(v = [6.0000000000, 3.0000000000, 0]) {
												rotate(a = 0) {
													union() {
														translate(v = [1.7500000000, 0]) {
															square(center = true, size = [2.5000000000, 4.0000000000]);
														}
														translate(v = [-1.7500000000, 0]) {
															square(center = true, size = [2.5000000000, 4.0000000000]);
														}
													}
												}
											}
											translate(v = [6.0000000000, 3.0000000000, 0]) {
												rotate(a = 0) {
													union() {
														translate(v = [3, 0]) {
															circle($fn = 64, r = 2);
														}
														translate(v = [-3, 0]) {
															circle($fn = 64, r = 2);
														}
													}
												}
											}
										}
									}
									translate(v = [0, 6]) {
										union() {
											translate(v = [6.0000000000, 3.0000000000, 0]) {
												rotate(a = 0) {
													union() {
														translate(v = [1.7500000000, 0]) {
															square(center = true, size = [2.5000000000, 4.0000000000]);
														}
														translate(v = [-1.7500000000, 0]) {
															square(center = true, size = [2.5000000000, 4.0000000000]);
														}
													}
												}
											}
											translate(v = [6.0000000000, 3.0000000000, 0]) {
												rotate(a = 0) {
													union() {
														translate(v = [3, 0]) {
															circle($fn = 64, r = 2);
														}
														translate(v = [-3, 0]) {
															circle($fn = 64, r = 2);
														}
													}
												}
											}
										}
									}
								}
								union() {
									translate(v = [0, 0]) {
										union() {
											translate(v = [6.0000000000, 3.0000000000, 0]) {
												rotate(a = 0) {
													union() {
														translate(v = [2.5000000000, 0]) {
															square(center = true, size = [2, 2]);
														}
														translate(v = [-2.5000000000, 0]) {
															square(center = true, size = [2, 2]);
														}
													}
												}
											}
										}
									}
									translate(v = [0, 6]) {
										union() {
											translate(v = [6.0000000000, 3.0000000000, 0]) {
												rotate(a = 0) {
													union() {
														translate(v = [2.5000000000, 0]) {
															square(center = true, size = [2, 2]);
														}
														translate(v = [-2.5000000000, 0]) {
															square(center = true, size = [2, 2]);
														}
													}
												}
											}
										}
									}
								}
							}
						}
						translate(v = [52.5000000000, 35.0000000000]) {
							difference() {
								union() {
									translate(v = [0, 0]) {
										union() {
											translate(v = [6.0000000000, 3.0000000000, 0]) {
												rotate(a = 0) {
													union() {
														translate(v = [1.7500000000, 0]) {
															square(center = true, size = [2.5000000000, 4.0000000000]);
														}
														translate(v = [-1.7500000000, 0]) {
															square(center = true, size = [2.5000000000, 4.0000000000]);
														}
													}
												}
											}
											translate(v = [6.0000000000, 3.0000000000, 0]) {
												rotate(a = 0) {
													union() {
														translate(v = [3, 0]) {
															circle($fn = 64, r = 2);
														}
														translate(v = [-3, 0]) {
															circle($fn = 64, r = 2);
														}
													}
												}
											}
										}
									}
									translate(v = [0, 6]) {
										union() {
											translate(v = [6.0000000000, 3.0000000000, 0]) {
												rotate(a = 0) {
													union() {
														translate(v = [1.7500000000, 0]) {
															square(center = true, size = [2.5000000000, 4.0000000000]);
														}
														translate(v = [-1.7500000000, 0]) {
															square(center = true, size = [2.5000000000, 4.0000000000]);
														}
													}
												}
											}
											translate(v = [6.0000000000, 3.0000000000, 0]) {
												rotate(a = 0) {
													union() {
														translate(v = [3, 0]) {
															circle($fn = 64, r = 2);
														}
														translate(v = [-3, 0]) {
															circle($fn = 64, r = 2);
														}
													}
												}
											}
										}
									}
								}
								union() {
									translate(v = [0, 0]) {
										union() {
											translate(v = [6.0000000000, 3.0000000000, 0]) {
												rotate(a = 0) {
													union() {
														translate(v = [2.5000000000, 0]) {
															square(center = true, size = [2, 2]);
														}
														translate(v = [-2.5000000000, 0]) {
															square(center = true, size = [2, 2]);
														}
													}
												}
											}
										}
									}
									translate(v = [0, 6]) {
										union() {
											translate(v = [6.0000000000, 3.0000000000, 0]) {
												rotate(a = 0) {
													union() {
														translate(v = [2.5000000000, 0]) {
															square(center = true, size = [2, 2]);
														}
														translate(v = [-2.5000000000, 0]) {
															square(center = true, size = [2, 2]);
														}
													}
												}
											}
										}
									}
								}
							}
						}
						translate(v = [0.0000000000, 52.5000000000]) {
							difference() {
								union() {
									translate(v = [0, 0]) {
										union() {
											translate(v = [6.0000000000, 3.0000000000, 0]) {
												rotate(a = 0) {
													union() {
														translate(v = [1.7500000000, 0]) {
															square(center = true, size = [2.5000000000, 4.0000000000]);
														}
														translate(v = [-1.7500000000, 0]) {
															square(center = true, size = [2.5000000000, 4.0000000000]);
														}
													}
												}
											}
											translate(v = [6.0000000000, 3.0000000000, 0]) {
												rotate(a = 0) {
													union() {
														translate(v = [3, 0]) {
															circle($fn = 64, r = 2);
														}
														translate(v = [-3, 0]) {
															circle($fn = 64, r = 2);
														}
													}
												}
											}
										}
									}
									translate(v = [0, 6]) {
										union() {
											translate(v = [6.0000000000, 3.0000000000, 0]) {
												rotate(a = 0) {
													union() {
														translate(v = [1.7500000000, 0]) {
															square(center = true, size = [2.5000000000, 4.0000000000]);
														}
														translate(v = [-1.7500000000, 0]) {
															square(center = true, size = [2.5000000000, 4.0000000000]);
														}
													}
												}
											}
											translate(v = [6.0000000000, 3.0000000000, 0]) {
												rotate(a = 0) {
													union() {
														translate(v = [3, 0]) {
															circle($fn = 64, r = 2);
														}
														translate(v = [-3, 0]) {
															circle($fn = 64, r = 2);
														}
													}
												}
											}
										}
									}
								}
								union() {
									translate(v = [0, 0]) {
										union() {
											translate(v = [6.0000000000, 3.0000000000, 0]) {
												rotate(a = 0) {
													union() {
														translate(v = [2.5000000000, 0]) {
															square(center = true, size = [2, 2]);
														}
														translate(v = [-2.5000000000, 0]) {
															square(center = true, size = [2, 2]);
														}
													}
												}
											}
										}
									}
									translate(v = [0, 6]) {
										union() {
											translate(v = [6.0000000000, 3.0000000000, 0]) {
												rotate(a = 0) {
													union() {
														translate(v = [2.5000000000, 0]) {
															square(center = true, size = [2, 2]);
														}
														translate(v = [-2.5000000000, 0]) {
															square(center = true, size = [2, 2]);
														}
													}
												}
											}
										}
									}
								}
							}
						}
						translate(v = [17.5000000000, 52.5000000000]) {
							difference() {
								union() {
									translate(v = [0, 0]) {
										union() {
											translate(v = [6.0000000000, 3.0000000000, 0]) {
												rotate(a = 0) {
													union() {
														translate(v = [1.7500000000, 0]) {
															square(center = true, size = [2.5000000000, 4.0000000000]);
														}
														translate(v = [-1.7500000000, 0]) {
															square(center = true, size = [2.5000000000, 4.0000000000]);
														}
													}
												}
											}
											translate(v = [6.0000000000, 3.0000000000, 0]) {
												rotate(a = 0) {
													union() {
														translate(v = [3, 0]) {
															circle($fn = 64, r = 2);
														}
														translate(v = [-3, 0]) {
															circle($fn = 64, r = 2);
														}
													}
												}
											}
										}
									}
									translate(v = [0, 6]) {
										union() {
											translate(v = [6.0000000000, 3.0000000000, 0]) {
												rotate(a = 0) {
													union() {
														translate(v = [1.7500000000, 0]) {
															square(center = true, size = [2.5000000000, 4.0000000000]);
														}
														translate(v = [-1.7500000000, 0]) {
															square(center = true, size = [2.5000000000, 4.0000000000]);
														}
													}
												}
											}
											translate(v = [6.0000000000, 3.0000000000, 0]) {
												rotate(a = 0) {
													union() {
														translate(v = [3, 0]) {
															circle($fn = 64, r = 2);
														}
														translate(v = [-3, 0]) {
															circle($fn = 64, r = 2);
														}
													}
												}
											}
										}
									}
								}
								union() {
									translate(v = [0, 0]) {
										union() {
											translate(v = [6.0000000000, 3.0000000000, 0]) {
												rotate(a = 0) {
													union() {
														translate(v = [2.5000000000, 0]) {
															square(center = true, size = [2, 2]);
														}
														translate(v = [-2.5000000000, 0]) {
															square(center = true, size = [2, 2]);
														}
													}
												}
											}
										}
									}
									translate(v = [0, 6]) {
										union() {
											translate(v = [6.0000000000, 3.0000000000, 0]) {
												rotate(a = 0) {
													union() {
														translate(v = [2.5000000000, 0]) {
															square(center = true, size = [2, 2]);
														}
														translate(v = [-2.5000000000, 0]) {
															square(center = true, size = [2, 2]);
														}
													}
												}
											}
										}
									}
								}
							}
						}
						translate(v = [35.0000000000, 52.5000000000]) {
							difference() {
								union() {
									translate(v = [0, 0]) {
										union() {
											translate(v = [6.0000000000, 3.0000000000, 0]) {
												rotate(a = 0) {
													union() {
														translate(v = [1.7500000000, 0]) {
															square(center = true, size = [2.5000000000, 4.0000000000]);
														}
														translate(v = [-1.7500000000, 0]) {
															square(center = true, size = [2.5000000000, 4.0000000000]);
														}
													}
												}
											}
											translate(v = [6.0000000000, 3.0000000000, 0]) {
												rotate(a = 0) {
													union() {
														translate(v = [3, 0]) {
															circle($fn = 64, r = 2);
														}
														translate(v = [-3, 0]) {
															circle($fn = 64, r = 2);
														}
													}
												}
											}
										}
									}
									translate(v = [0, 6]) {
										union() {
											translate(v = [6.0000000000, 3.0000000000, 0]) {
												rotate(a = 0) {
													union() {
														translate(v = [1.7500000000, 0]) {
															square(center = true, size = [2.5000000000, 4.0000000000]);
														}
														translate(v = [-1.7500000000, 0]) {
															square(center = true, size = [2.5000000000, 4.0000000000]);
														}
													}
												}
											}
											translate(v = [6.0000000000, 3.0000000000, 0]) {
												rotate(a = 0) {
													union() {
														translate(v = [3, 0]) {
															circle($fn = 64, r = 2);
														}
														translate(v = [-3, 0]) {
															circle($fn = 64, r = 2);
														}
													}
												}
											}
										}
									}
								}
								union() {
									translate(v = [0, 0]) {
										union() {
											translate(v = [6.0000000000, 3.0000000000, 0]) {
												rotate(a = 0) {
													union() {
														translate(v = [2.5000000000, 0]) {
															square(center = true, size = [2, 2]);
														}
														translate(v = [-2.5000000000, 0]) {
															square(center = true, size = [2, 2]);
														}
													}
												}
											}
										}
									}
									translate(v = [0, 6]) {
										union() {
											translate(v = [6.0000000000, 3.0000000000, 0]) {
												rotate(a = 0) {
													union() {
														translate(v = [2.5000000000, 0]) {
															square(center = true, size = [2, 2]);
														}
														translate(v = [-2.5000000000, 0]) {
															square(center = true, size = [2, 2]);
														}
													}
												}
											}
										}
									}
								}
							}
						}
						translate(v = [52.5000000000, 52.5000000000]) {
							difference() {
								union() {
									translate(v = [0, 0]) {
										union() {
											translate(v = [6.0000000000, 3.0000000000, 0]) {
												rotate(a = 0) {
													union() {
														translate(v = [1.7500000000, 0]) {
															square(center = true, size = [2.5000000000, 4.0000000000]);
														}
														translate(v = [-1.7500000000, 0]) {
															square(center = true, size = [2.5000000000, 4.0000000000]);
														}
													}
												}
											}
											translate(v = [6.0000000000, 3.0000000000, 0]) {
												rotate(a = 0) {
													union() {
														translate(v = [3, 0]) {
															circle($fn = 64, r = 2);
														}
														translate(v = [-3, 0]) {
															circle($fn = 64, r = 2);
														}
													}
												}
											}
										}
									}
									translate(v = [0, 6]) {
										union() {
											translate(v = [6.0000000000, 3.0000000000, 0]) {
												rotate(a = 0) {
													union() {
														translate(v = [1.7500000000, 0]) {
															square(center = true, size = [2.5000000000, 4.0000000000]);
														}
														translate(v = [-1.7500000000, 0]) {
															square(center = true, size = [2.5000000000, 4.0000000000]);
														}
													}
												}
											}
											translate(v = [6.0000000000, 3.0000000000, 0]) {
												rotate(a = 0) {
													union() {
														translate(v = [3, 0]) {
															circle($fn = 64, r = 2);
														}
														translate(v = [-3, 0]) {
															circle($fn = 64, r = 2);
														}
													}
												}
											}
										}
									}
								}
								union() {
									translate(v = [0, 0]) {
										union() {
											translate(v = [6.0000000000, 3.0000000000, 0]) {
												rotate(a = 0) {
													union() {
														translate(v = [2.5000000000, 0]) {
															square(center = true, size = [2, 2]);
														}
														translate(v = [-2.5000000000, 0]) {
															square(center = true, size = [2, 2]);
														}
													}
												}
											}
										}
									}
									translate(v = [0, 6]) {
										union() {
											translate(v = [6.0000000000, 3.0000000000, 0]) {
												rotate(a = 0) {
													union() {
														translate(v = [2.5000000000, 0]) {
															square(center = true, size = [2, 2]);
														}
														translate(v = [-2.5000000000, 0]) {
															square(center = true, size = [2, 2]);
														}
													}
												}
											}
										}
									}
								}
							}
						}
					}
				}
			}
		}
		union() {
			translate(v = [-2.7500000000, -2.7500000000]) {
				union() {
					translate(v = [75.2500000000, 35.0000000000, 0]) {
						union() {
							translate(v = [0.0625000000, 0.0625000000, 0]) {
								translate(v = [0, 0, 0]) {
									rotate(a = 180) {
										union() {
											square(center = false, size = [1, 0.1250000000]);
											square(center = false, size = [0.1250000000, 1]);
										}
									}
								}
							}
							translate(v = [-0.0625000000, -0.0625000000, 0]) {
								translate(v = [0, 0, 0]) {
									rotate(a = 0) {
										union() {
											square(center = false, size = [1, 0.1250000000]);
											square(center = false, size = [0.1250000000, 1]);
										}
									}
								}
							}
						}
					}
					translate(v = [35.0000000000, 75.2500000000, 0]) {
						union() {
							translate(v = [0.0625000000, 0.0625000000, 0]) {
								translate(v = [0, 0, 0]) {
									rotate(a = 180) {
										union() {
											square(center = false, size = [1, 0.1250000000]);
											square(center = false, size = [0.1250000000, 1]);
										}
									}
								}
							}
							translate(v = [-0.0625000000, -0.0625000000, 0]) {
								translate(v = [0, 0, 0]) {
									rotate(a = 0) {
										union() {
											square(center = false, size = [1, 0.1250000000]);
											square(center = false, size = [0.1250000000, 1]);
										}
									}
								}
							}
						}
					}
					translate(v = [-5.2500000000, 35.0000000000, 0]) {
						union() {
							translate(v = [0.0625000000, 0.0625000000, 0]) {
								translate(v = [0, 0, 0]) {
									rotate(a = 180) {
										union() {
											square(center = false, size = [1, 0.1250000000]);
											square(center = false, size = [0.1250000000, 1]);
										}
									}
								}
							}
							translate(v = [-0.0625000000, -0.0625000000, 0]) {
								translate(v = [0, 0, 0]) {
									rotate(a = 0) {
										union() {
											square(center = false, size = [1, 0.1250000000]);
											square(center = false, size = [0.1250000000, 1]);
										}
									}
								}
							}
						}
					}
					translate(v = [35.0000000000, -5.2500000000, 0]) {
						union() {
							translate(v = [0.0625000000, 0.0625000000, 0]) {
								translate(v = [0, 0, 0]) {
									rotate(a = 180) {
										union() {
											square(center = false, size = [1, 0.1250000000]);
											square(center = false, size = [0.1250000000, 1]);
										}
									}
								}
							}
							translate(v = [-0.0625000000, -0.0625000000, 0]) {
								translate(v = [0, 0, 0]) {
									rotate(a = 0) {
										union() {
											square(center = false, size = [1, 0.1250000000]);
											square(center = false, size = [0.1250000000, 1]);
										}
									}
								}
							}
						}
					}
					translate(v = [2.7500000000, 2.7500000000]) {
						union() {
							translate(v = [0.0000000000, 0.0000000000]) {
								union() {
									translate(v = [0, 0]) {
										translate(v = [6.0000000000, 3.0000000000, 0]) {
											rotate(a = 0) {
												union() {
													translate(v = [0, 0.0000000000]) {
														translate(v = [0, -0.0200000000]) {
															square(center = true, size = [4, 0.0100000000]);
														}
													}
													translate(v = [0, 0.0400000000]) {
														translate(v = [0, -0.0200000000]) {
															square(center = true, size = [4, 0.0100000000]);
														}
													}
													translate(v = [0, -0.0400000000]) {
														translate(v = [0, -0.0200000000]) {
															square(center = true, size = [4, 0.0100000000]);
														}
													}
													translate(v = [0, 0.0800000000]) {
														translate(v = [0, -0.0200000000]) {
															square(center = true, size = [4, 0.0100000000]);
														}
													}
													translate(v = [0, -0.0800000000]) {
														translate(v = [0, -0.0200000000]) {
															square(center = true, size = [4, 0.0100000000]);
														}
													}
													translate(v = [0, 0.1200000000]) {
														translate(v = [0, -0.0200000000]) {
															square(center = true, size = [4, 0.0100000000]);
														}
													}
													translate(v = [0, -0.1200000000]) {
														translate(v = [0, -0.0200000000]) {
															square(center = true, size = [4, 0.0100000000]);
														}
													}
													translate(v = [0, 0.1600000000]) {
														translate(v = [0, -0.0200000000]) {
															square(center = true, size = [4, 0.0100000000]);
														}
													}
													translate(v = [0, -0.1600000000]) {
														translate(v = [0, -0.0200000000]) {
															square(center = true, size = [4, 0.0100000000]);
														}
													}
													translate(v = [0, 0.2000000000]) {
														translate(v = [0, -0.0200000000]) {
															square(center = true, size = [4, 0.0100000000]);
														}
													}
													translate(v = [0, -0.2000000000]) {
														translate(v = [0, -0.0200000000]) {
															square(center = true, size = [4, 0.0100000000]);
														}
													}
													translate(v = [0, 0.2400000000]) {
														translate(v = [0, -0.0200000000]) {
															square(center = true, size = [4, 0.0100000000]);
														}
													}
													translate(v = [0, -0.2400000000]) {
														translate(v = [0, -0.0200000000]) {
															square(center = true, size = [4, 0.0100000000]);
														}
													}
													translate(v = [0, 0.2800000000]) {
														translate(v = [0, -0.0200000000]) {
															square(center = true, size = [4, 0.0100000000]);
														}
													}
													translate(v = [0, -0.2800000000]) {
														translate(v = [0, -0.0200000000]) {
															square(center = true, size = [4, 0.0100000000]);
														}
													}
													translate(v = [0, 0.3200000000]) {
														translate(v = [0, -0.0200000000]) {
															square(center = true, size = [4, 0.0100000000]);
														}
													}
													translate(v = [0, -0.3200000000]) {
														translate(v = [0, -0.0200000000]) {
															square(center = true, size = [4, 0.0100000000]);
														}
													}
													translate(v = [0, 0.3600000000]) {
														translate(v = [0, -0.0200000000]) {
															square(center = true, size = [4, 0.0100000000]);
														}
													}
													translate(v = [0, -0.3600000000]) {
														translate(v = [0, -0.0200000000]) {
															square(center = true, size = [4, 0.0100000000]);
														}
													}
													translate(v = [0, 0.4000000000]) {
														translate(v = [0, -0.0200000000]) {
															square(center = true, size = [4, 0.0100000000]);
														}
													}
													translate(v = [0, -0.4000000000]) {
														translate(v = [0, -0.0200000000]) {
															square(center = true, size = [4, 0.0100000000]);
														}
													}
													translate(v = [0, 0.4400000000]) {
														translate(v = [0, -0.0200000000]) {
															square(center = true, size = [4, 0.0100000000]);
														}
													}
													translate(v = [0, -0.4400000000]) {
														translate(v = [0, -0.0200000000]) {
															square(center = true, size = [4, 0.0100000000]);
														}
													}
													translate(v = [0, 0.4800000000]) {
														translate(v = [0, -0.0200000000]) {
															square(center = true, size = [4, 0.0100000000]);
														}
													}
													translate(v = [0, -0.4800000000]) {
														translate(v = [0, -0.0200000000]) {
															square(center = true, size = [4, 0.0100000000]);
														}
													}
													translate(v = [0, 0.5200000000]) {
														translate(v = [0, -0.0200000000]) {
															square(center = true, size = [4, 0.0100000000]);
														}
													}
													translate(v = [0, -0.5200000000]) {
														translate(v = [0, -0.0200000000]) {
															square(center = true, size = [4, 0.0100000000]);
														}
													}
													translate(v = [0, 0.5600000000]) {
														translate(v = [0, -0.0200000000]) {
															square(center = true, size = [4, 0.0100000000]);
														}
													}
													translate(v = [0, -0.5600000000]) {
														translate(v = [0, -0.0200000000]) {
															square(center = true, size = [4, 0.0100000000]);
														}
													}
													translate(v = [0, 0.6000000000]) {
														translate(v = [0, -0.0200000000]) {
															square(center = true, size = [4, 0.0100000000]);
														}
													}
													translate(v = [0, -0.6000000000]) {
														translate(v = [0, -0.0200000000]) {
															square(center = true, size = [4, 0.0100000000]);
														}
													}
													translate(v = [0, 0.6400000000]) {
														translate(v = [0, -0.0200000000]) {
															square(center = true, size = [4, 0.0100000000]);
														}
													}
													translate(v = [0, -0.6400000000]) {
														translate(v = [0, -0.0200000000]) {
															square(center = true, size = [4, 0.0100000000]);
														}
													}
													translate(v = [0, 0.6800000000]) {
														translate(v = [0, -0.0200000000]) {
															square(center = true, size = [4, 0.0100000000]);
														}
													}
													translate(v = [0, -0.6800000000]) {
														translate(v = [0, -0.0200000000]) {
															square(center = true, size = [4, 0.0100000000]);
														}
													}
													translate(v = [0, 0.7200000000]) {
														translate(v = [0, -0.0200000000]) {
															square(center = true, size = [4, 0.0100000000]);
														}
													}
													translate(v = [0, -0.7200000000]) {
														translate(v = [0, -0.0200000000]) {
															square(center = true, size = [4, 0.0100000000]);
														}
													}
													translate(v = [0, 0.7600000000]) {
														translate(v = [0, -0.0200000000]) {
															square(center = true, size = [4, 0.0100000000]);
														}
													}
													translate(v = [0, -0.7600000000]) {
														translate(v = [0, -0.0200000000]) {
															square(center = true, size = [4, 0.0100000000]);
														}
													}
													translate(v = [0, 0.8000000000]) {
														translate(v = [0, -0.0200000000]) {
															square(center = true, size = [4, 0.0100000000]);
														}
													}
													translate(v = [0, -0.8000000000]) {
														translate(v = [0, -0.0200000000]) {
															square(center = true, size = [4, 0.0100000000]);
														}
													}
													translate(v = [0, 0.8400000000]) {
														translate(v = [0, -0.0200000000]) {
															square(center = true, size = [4, 0.0100000000]);
														}
													}
													translate(v = [0, -0.8400000000]) {
														translate(v = [0, -0.0200000000]) {
															square(center = true, size = [4, 0.0100000000]);
														}
													}
													translate(v = [0, 0.8800000000]) {
														translate(v = [0, -0.0200000000]) {
															square(center = true, size = [4, 0.0100000000]);
														}
													}
													translate(v = [0, -0.8800000000]) {
														translate(v = [0, -0.0200000000]) {
															square(center = true, size = [4, 0.0100000000]);
														}
													}
													translate(v = [0, 0.9200000000]) {
														translate(v = [0, -0.0200000000]) {
															square(center = true, size = [4, 0.0100000000]);
														}
													}
													translate(v = [0, -0.9200000000]) {
														translate(v = [0, -0.0200000000]) {
															square(center = true, size = [4, 0.0100000000]);
														}
													}
													translate(v = [0, 0.9600000000]) {
														translate(v = [0, -0.0200000000]) {
															square(center = true, size = [4, 0.0100000000]);
														}
													}
													translate(v = [0, -0.9600000000]) {
														translate(v = [0, -0.0200000000]) {
															square(center = true, size = [4, 0.0100000000]);
														}
													}
													translate(v = [0, 1.0000000000]) {
														translate(v = [0, -0.0200000000]) {
															square(center = true, size = [4, 0.0100000000]);
														}
													}
												}
											}
										}
									}
									translate(v = [0, 6]) {
										translate(v = [6.0000000000, 3.0000000000, 0]) {
											rotate(a = 0) {
												union() {
													translate(v = [0, 0.0000000000]) {
														translate(v = [0, -0.0200000000]) {
															square(center = true, size = [4, 0.0100000000]);
														}
													}
													translate(v = [0, 0.0400000000]) {
														translate(v = [0, -0.0200000000]) {
															square(center = true, size = [4, 0.0100000000]);
														}
													}
													translate(v = [0, -0.0400000000]) {
														translate(v = [0, -0.0200000000]) {
															square(center = true, size = [4, 0.0100000000]);
														}
													}
													translate(v = [0, 0.0800000000]) {
														translate(v = [0, -0.0200000000]) {
															square(center = true, size = [4, 0.0100000000]);
														}
													}
													translate(v = [0, -0.0800000000]) {
														translate(v = [0, -0.0200000000]) {
															square(center = true, size = [4, 0.0100000000]);
														}
													}
													translate(v = [0, 0.1200000000]) {
														translate(v = [0, -0.0200000000]) {
															square(center = true, size = [4, 0.0100000000]);
														}
													}
													translate(v = [0, -0.1200000000]) {
														translate(v = [0, -0.0200000000]) {
															square(center = true, size = [4, 0.0100000000]);
														}
													}
													translate(v = [0, 0.1600000000]) {
														translate(v = [0, -0.0200000000]) {
															square(center = true, size = [4, 0.0100000000]);
														}
													}
													translate(v = [0, -0.1600000000]) {
														translate(v = [0, -0.0200000000]) {
															square(center = true, size = [4, 0.0100000000]);
														}
													}
													translate(v = [0, 0.2000000000]) {
														translate(v = [0, -0.0200000000]) {
															square(center = true, size = [4, 0.0100000000]);
														}
													}
													translate(v = [0, -0.2000000000]) {
														translate(v = [0, -0.0200000000]) {
															square(center = true, size = [4, 0.0100000000]);
														}
													}
													translate(v = [0, 0.2400000000]) {
														translate(v = [0, -0.0200000000]) {
															square(center = true, size = [4, 0.0100000000]);
														}
													}
													translate(v = [0, -0.2400000000]) {
														translate(v = [0, -0.0200000000]) {
															square(center = true, size = [4, 0.0100000000]);
														}
													}
													translate(v = [0, 0.2800000000]) {
														translate(v = [0, -0.0200000000]) {
															square(center = true, size = [4, 0.0100000000]);
														}
													}
													translate(v = [0, -0.2800000000]) {
														translate(v = [0, -0.0200000000]) {
															square(center = true, size = [4, 0.0100000000]);
														}
													}
													translate(v = [0, 0.3200000000]) {
														translate(v = [0, -0.0200000000]) {
															square(center = true, size = [4, 0.0100000000]);
														}
													}
													translate(v = [0, -0.3200000000]) {
														translate(v = [0, -0.0200000000]) {
															square(center = true, size = [4, 0.0100000000]);
														}
													}
													translate(v = [0, 0.3600000000]) {
														translate(v = [0, -0.0200000000]) {
															square(center = true, size = [4, 0.0100000000]);
														}
													}
													translate(v = [0, -0.3600000000]) {
														translate(v = [0, -0.0200000000]) {
															square(center = true, size = [4, 0.0100000000]);
														}
													}
													translate(v = [0, 0.4000000000]) {
														translate(v = [0, -0.0200000000]) {
															square(center = true, size = [4, 0.0100000000]);
														}
													}
													translate(v = [0, -0.4000000000]) {
														translate(v = [0, -0.0200000000]) {
															square(center = true, size = [4, 0.0100000000]);
														}
													}
													translate(v = [0, 0.4400000000]) {
														translate(v = [0, -0.0200000000]) {
															square(center = true, size = [4, 0.0100000000]);
														}
													}
													translate(v = [0, -0.4400000000]) {
														translate(v = [0, -0.0200000000]) {
															square(center = true, size = [4, 0.0100000000]);
														}
													}
													translate(v = [0, 0.4800000000]) {
														translate(v = [0, -0.0200000000]) {
															square(center = true, size = [4, 0.0100000000]);
														}
													}
													translate(v = [0, -0.4800000000]) {
														translate(v = [0, -0.0200000000]) {
															square(center = true, size = [4, 0.0100000000]);
														}
													}
													translate(v = [0, 0.5200000000]) {
														translate(v = [0, -0.0200000000]) {
															square(center = true, size = [4, 0.0100000000]);
														}
													}
													translate(v = [0, -0.5200000000]) {
														translate(v = [0, -0.0200000000]) {
															square(center = true, size = [4, 0.0100000000]);
														}
													}
													translate(v = [0, 0.5600000000]) {
														translate(v = [0, -0.0200000000]) {
															square(center = true, size = [4, 0.0100000000]);
														}
													}
													translate(v = [0, -0.5600000000]) {
														translate(v = [0, -0.0200000000]) {
															square(center = true, size = [4, 0.0100000000]);
														}
													}
													translate(v = [0, 0.6000000000]) {
														translate(v = [0, -0.0200000000]) {
															square(center = true, size = [4, 0.0100000000]);
														}
													}
													translate(v = [0, -0.6000000000]) {
														translate(v = [0, -0.0200000000]) {
															square(center = true, size = [4, 0.0100000000]);
														}
													}
													translate(v = [0, 0.6400000000]) {
														translate(v = [0, -0.0200000000]) {
															square(center = true, size = [4, 0.0100000000]);
														}
													}
													translate(v = [0, -0.6400000000]) {
														translate(v = [0, -0.0200000000]) {
															square(center = true, size = [4, 0.0100000000]);
														}
													}
													translate(v = [0, 0.6800000000]) {
														translate(v = [0, -0.0200000000]) {
															square(center = true, size = [4, 0.0100000000]);
														}
													}
													translate(v = [0, -0.6800000000]) {
														translate(v = [0, -0.0200000000]) {
															square(center = true, size = [4, 0.0100000000]);
														}
													}
													translate(v = [0, 0.7200000000]) {
														translate(v = [0, -0.0200000000]) {
															square(center = true, size = [4, 0.0100000000]);
														}
													}
													translate(v = [0, -0.7200000000]) {
														translate(v = [0, -0.0200000000]) {
															square(center = true, size = [4, 0.0100000000]);
														}
													}
													translate(v = [0, 0.7600000000]) {
														translate(v = [0, -0.0200000000]) {
															square(center = true, size = [4, 0.0100000000]);
														}
													}
													translate(v = [0, -0.7600000000]) {
														translate(v = [0, -0.0200000000]) {
															square(center = true, size = [4, 0.0100000000]);
														}
													}
													translate(v = [0, 0.8000000000]) {
														translate(v = [0, -0.0200000000]) {
															square(center = true, size = [4, 0.0100000000]);
														}
													}
													translate(v = [0, -0.8000000000]) {
														translate(v = [0, -0.0200000000]) {
															square(center = true, size = [4, 0.0100000000]);
														}
													}
													translate(v = [0, 0.8400000000]) {
														translate(v = [0, -0.0200000000]) {
															square(center = true, size = [4, 0.0100000000]);
														}
													}
													translate(v = [0, -0.8400000000]) {
														translate(v = [0, -0.0200000000]) {
															square(center = true, size = [4, 0.0100000000]);
														}
													}
													translate(v = [0, 0.8800000000]) {
														translate(v = [0, -0.0200000000]) {
															square(center = true, size = [4, 0.0100000000]);
														}
													}
													translate(v = [0, -0.8800000000]) {
														translate(v = [0, -0.0200000000]) {
															square(center = true, size = [4, 0.0100000000]);
														}
													}
													translate(v = [0, 0.9200000000]) {
														translate(v = [0, -0.0200000000]) {
															square(center = true, size = [4, 0.0100000000]);
														}
													}
													translate(v = [0, -0.9200000000]) {
														translate(v = [0, -0.0200000000]) {
															square(center = true, size = [4, 0.0100000000]);
														}
													}
													translate(v = [0, 0.9600000000]) {
														translate(v = [0, -0.0200000000]) {
															square(center = true, size = [4, 0.0100000000]);
														}
													}
													translate(v = [0, -0.9600000000]) {
														translate(v = [0, -0.0200000000]) {
															square(center = true, size = [4, 0.0100000000]);
														}
													}
													translate(v = [0, 1.0000000000]) {
														translate(v = [0, -0.0200000000]) {
															square(center = true, size = [4, 0.0100000000]);
														}
													}
												}
											}
										}
									}
								}
							}
							translate(v = [17.5000000000, 0.0000000000]) {
								union() {
									translate(v = [0, 0]) {
										translate(v = [6.0000000000, 3.0000000000, 0]) {
											rotate(a = 0) {
												union() {
													translate(v = [0, 0.0000000000]) {
														translate(v = [0, -0.0200000000]) {
															square(center = true, size = [4, 0.0100000000]);
														}
													}
													translate(v = [0, 0.0400000000]) {
														translate(v = [0, -0.0200000000]) {
															square(center = true, size = [4, 0.0100000000]);
														}
													}
													translate(v = [0, -0.0400000000]) {
														translate(v = [0, -0.0200000000]) {
															square(center = true, size = [4, 0.0100000000]);
														}
													}
													translate(v = [0, 0.0800000000]) {
														translate(v = [0, -0.0200000000]) {
															square(center = true, size = [4, 0.0100000000]);
														}
													}
													translate(v = [0, -0.0800000000]) {
														translate(v = [0, -0.0200000000]) {
															square(center = true, size = [4, 0.0100000000]);
														}
													}
													translate(v = [0, 0.1200000000]) {
														translate(v = [0, -0.0200000000]) {
															square(center = true, size = [4, 0.0100000000]);
														}
													}
													translate(v = [0, -0.1200000000]) {
														translate(v = [0, -0.0200000000]) {
															square(center = true, size = [4, 0.0100000000]);
														}
													}
													translate(v = [0, 0.1600000000]) {
														translate(v = [0, -0.0200000000]) {
															square(center = true, size = [4, 0.0100000000]);
														}
													}
													translate(v = [0, -0.1600000000]) {
														translate(v = [0, -0.0200000000]) {
															square(center = true, size = [4, 0.0100000000]);
														}
													}
													translate(v = [0, 0.2000000000]) {
														translate(v = [0, -0.0200000000]) {
															square(center = true, size = [4, 0.0100000000]);
														}
													}
													translate(v = [0, -0.2000000000]) {
														translate(v = [0, -0.0200000000]) {
															square(center = true, size = [4, 0.0100000000]);
														}
													}
													translate(v = [0, 0.2400000000]) {
														translate(v = [0, -0.0200000000]) {
															square(center = true, size = [4, 0.0100000000]);
														}
													}
													translate(v = [0, -0.2400000000]) {
														translate(v = [0, -0.0200000000]) {
															square(center = true, size = [4, 0.0100000000]);
														}
													}
													translate(v = [0, 0.2800000000]) {
														translate(v = [0, -0.0200000000]) {
															square(center = true, size = [4, 0.0100000000]);
														}
													}
													translate(v = [0, -0.2800000000]) {
														translate(v = [0, -0.0200000000]) {
															square(center = true, size = [4, 0.0100000000]);
														}
													}
													translate(v = [0, 0.3200000000]) {
														translate(v = [0, -0.0200000000]) {
															square(center = true, size = [4, 0.0100000000]);
														}
													}
													translate(v = [0, -0.3200000000]) {
														translate(v = [0, -0.0200000000]) {
															square(center = true, size = [4, 0.0100000000]);
														}
													}
													translate(v = [0, 0.3600000000]) {
														translate(v = [0, -0.0200000000]) {
															square(center = true, size = [4, 0.0100000000]);
														}
													}
													translate(v = [0, -0.3600000000]) {
														translate(v = [0, -0.0200000000]) {
															square(center = true, size = [4, 0.0100000000]);
														}
													}
													translate(v = [0, 0.4000000000]) {
														translate(v = [0, -0.0200000000]) {
															square(center = true, size = [4, 0.0100000000]);
														}
													}
													translate(v = [0, -0.4000000000]) {
														translate(v = [0, -0.0200000000]) {
															square(center = true, size = [4, 0.0100000000]);
														}
													}
													translate(v = [0, 0.4400000000]) {
														translate(v = [0, -0.0200000000]) {
															square(center = true, size = [4, 0.0100000000]);
														}
													}
													translate(v = [0, -0.4400000000]) {
														translate(v = [0, -0.0200000000]) {
															square(center = true, size = [4, 0.0100000000]);
														}
													}
													translate(v = [0, 0.4800000000]) {
														translate(v = [0, -0.0200000000]) {
															square(center = true, size = [4, 0.0100000000]);
														}
													}
													translate(v = [0, -0.4800000000]) {
														translate(v = [0, -0.0200000000]) {
															square(center = true, size = [4, 0.0100000000]);
														}
													}
													translate(v = [0, 0.5200000000]) {
														translate(v = [0, -0.0200000000]) {
															square(center = true, size = [4, 0.0100000000]);
														}
													}
													translate(v = [0, -0.5200000000]) {
														translate(v = [0, -0.0200000000]) {
															square(center = true, size = [4, 0.0100000000]);
														}
													}
													translate(v = [0, 0.5600000000]) {
														translate(v = [0, -0.0200000000]) {
															square(center = true, size = [4, 0.0100000000]);
														}
													}
													translate(v = [0, -0.5600000000]) {
														translate(v = [0, -0.0200000000]) {
															square(center = true, size = [4, 0.0100000000]);
														}
													}
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
