trissim/OpenMFD/designs/open_chamber/channels_5x5_units_.scad

// Generated by SolidPython 1.1.3 on 2022-07-14 17:39:10


union() {
	translate(v = [63.0000000000, 31.5000000000, 0]) {
		union() {
			translate(v = [0.1054687500, 0.1054687500, 0]) {
				translate(v = [0, 0, 0]) {
					rotate(a = 180) {
						union() {
							square(center = false, size = [1.6875000000, 0.2109375000]);
							square(center = false, size = [0.2109375000, 1.6875000000]);
						}
					}
				}
			}
			translate(v = [-0.1054687500, -0.1054687500, 0]) {
				translate(v = [0, 0, 0]) {
					rotate(a = 0) {
						union() {
							square(center = false, size = [1.6875000000, 0.2109375000]);
							square(center = false, size = [0.2109375000, 1.6875000000]);
						}
					}
				}
			}
		}
	}
	translate(v = [27.0000000000, 31.5000000000, 0]) {
		union() {
			translate(v = [0.1054687500, 0.1054687500, 0]) {
				translate(v = [0, 0, 0]) {
					rotate(a = 180) {
						union() {
							square(center = false, size = [1.6875000000, 0.2109375000]);
							square(center = false, size = [0.2109375000, 1.6875000000]);
						}
					}
				}
			}
			translate(v = [-0.1054687500, -0.1054687500, 0]) {
				translate(v = [0, 0, 0]) {
					rotate(a = 0) {
						union() {
							square(center = false, size = [1.6875000000, 0.2109375000]);
							square(center = false, size = [0.2109375000, 1.6875000000]);
						}
					}
				}
			}
		}
	}
	translate(v = [63.0000000000, 13.5000000000, 0]) {
		union() {
			translate(v = [0.1054687500, 0.1054687500, 0]) {
				translate(v = [0, 0, 0]) {
					rotate(a = 180) {
						union() {
							square(center = false, size = [1.6875000000, 0.2109375000]);
							square(center = false, size = [0.2109375000, 1.6875000000]);
						}
					}
				}
			}
			translate(v = [-0.1054687500, -0.1054687500, 0]) {
				translate(v = [0, 0, 0]) {
					rotate(a = 0) {
						union() {
							square(center = false, size = [1.6875000000, 0.2109375000]);
							square(center = false, size = [0.2109375000, 1.6875000000]);
						}
					}
				}
			}
		}
	}
	translate(v = [27.0000000000, 13.5000000000, 0]) {
		union() {
			translate(v = [0.1054687500, 0.1054687500, 0]) {
				translate(v = [0, 0, 0]) {
					rotate(a = 180) {
						union() {
							square(center = false, size = [1.6875000000, 0.2109375000]);
							square(center = false, size = [0.2109375000, 1.6875000000]);
						}
					}
				}
			}
			translate(v = [-0.1054687500, -0.1054687500, 0]) {
				translate(v = [0, 0, 0]) {
					rotate(a = 0) {
						union() {
							square(center = false, size = [1.6875000000, 0.2109375000]);
							square(center = false, size = [0.2109375000, 1.6875000000]);
						}
					}
				}
			}
		}
	}
	union() {
		translate(v = [0, 0]) {
			translate(v = [9.0000000000, 4.5000000000, 0]) {
				rotate(a = 0) {
					union() {
						translate(v = [0, 0.0000000000]) {
							translate(v = [0, -0.0200000000]) {
								square(center = true, size = [2.0600000000, 0.0100000000]);
							}
						}
						translate(v = [0, 0.0400000000]) {
							translate(v = [0, -0.0200000000]) {
								square(center = true, size = [2.0600000000, 0.0100000000]);
							}
						}
						translate(v = [0, -0.0400000000]) {
							translate(v = [0, -0.0200000000]) {
								square(center = true, size = [2.0600000000, 0.0100000000]);
							}
						}
						translate(v = [0, 0.0800000000]) {
							translate(v = [0, -0.0200000000]) {
								square(center = true, size = [2.0600000000, 0.0100000000]);
							}
						}
						translate(v = [0, -0.0800000000]) {
							translate(v = [0, -0.0200000000]) {
								square(center = true, size = [2.0600000000, 0.0100000000]);
							}
						}
						translate(v = [0, 0.1200000000]) {
							translate(v = [0, -0.0200000000]) {
								square(center = true, size = [2.0600000000, 0.0100000000]);
							}
						}
						translate(v = [0, -0.1200000000]) {
							translate(v = [0, -0.0200000000]) {
								square(center = true, size = [2.0600000000, 0.0100000000]);
							}
						}
						translate(v = [0, 0.1600000000]) {
							translate(v = [0, -0.0200000000]) {
								square(center = true, size = [2.0600000000, 0.0100000000]);
							}
						}
						translate(v = [0, -0.1600000000]) {
							translate(v = [0, -0.0200000000]) {
								square(center = true, size = [2.0600000000, 0.0100000000]);
							}
						}
						translate(v = [0, 0.2000000000]) {
							translate(v = [0, -0.0200000000]) {
								square(center = true, size = [2.0600000000, 0.0100000000]);
							}
						}
						translate(v = [0, -0.2000000000]) {
							translate(v = [0, -0.0200000000]) {
								square(center = true, size = [2.0600000000, 0.0100000000]);
							}
						}
						translate(v = [0, 0.2400000000]) {
							translate(v = [0, -0.0200000000]) {
								square(center = true, size = [2.0600000000, 0.0100000000]);
							}
						}
						translate(v = [0, -0.2400000000]) {
							translate(v = [0, -0.0200000000]) {
								square(center = true, size = [2.0600000000, 0.0100000000]);
							}
						}
						translate(v = [0, 0.2800000000]) {
							translate(v = [0, -0.0200000000]) {
								square(center = true, size = [2.0600000000, 0.0100000000]);
							}
						}
						translate(v = [0, -0.2800000000]) {
							translate(v = [0, -0.0200000000]) {
								square(center = true, size = [2.0600000000, 0.0100000000]);
							}
						}
						translate(v = [0, 0.3200000000]) {
							translate(v = [0, -0.0200000000]) {
								square(center = true, size = [2.0600000000, 0.0100000000]);
							}
						}
						translate(v = [0, -0.3200000000]) {
							translate(v = [0, -0.0200000000]) {
								square(center = true, size = [2.0600000000, 0.0100000000]);
							}
						}
						translate(v = [0, 0.3600000000]) {
							translate(v = [0, -0.0200000000]) {
								square(center = true, size = [2.0600000000, 0.0100000000]);
							}
						}
						translate(v = [0, -0.3600000000]) {
							translate(v = [0, -0.0200000000]) {
								square(center = true, size = [2.0600000000, 0.0100000000]);
							}
						}
						translate(v = [0, 0.4000000000]) {
							translate(v = [0, -0.0200000000]) {
								square(center = true, size = [2.0600000000, 0.0100000000]);
							}
						}
						translate(v = [0, -0.4000000000]) {
							translate(v = [0, -0.0200000000]) {
								square(center = true, size = [2.0600000000, 0.0100000000]);
							}
						}
						translate(v = [0, 0.4400000000]) {
							translate(v = [0, -0.0200000000]) {
								square(center = true, size = [2.0600000000, 0.0100000000]);
							}
						}
						translate(v = [0, -0.4400000000]) {
							translate(v = [0, -0.0200000000]) {
								square(center = true, size = [2.0600000000, 0.0100000000]);
							}
						}
						translate(v = [0, 0.4800000000]) {
							translate(v = [0, -0.0200000000]) {
								square(center = true, size = [2.0600000000, 0.0100000000]);
							}
						}
						translate(v = [0, -0.4800000000]) {
							translate(v = [0, -0.0200000000]) {
								square(center = true, size = [2.0600000000, 0.0100000000]);
							}
						}
						translate(v = [0, 0.5200000000]) {
							translate(v = [0, -0.0200000000]) {
								square(center = true, size = [2.0600000000, 0.0100000000]);
							}
						}
						translate(v = [0, -0.5200000000]) {
							translate(v = [0, -0.0200000000]) {
								square(center = true, size = [2.0600000000, 0.0100000000]);
							}
						}
						translate(v = [0, 0.5600000000]) {
							translate(v = [0, -0.0200000000]) {
								square(center = true, size = [2.0600000000, 0.0100000000]);
							}
						}
						translate(v = [0, -0.5600000000]) {
							translate(v = [0, -0.0200000000]) {
								square(center = true, size = [2.0600000000, 0.0100000000]);
							}
						}
						translate(v = [0, 0.6000000000]) {
							translate(v = [0, -0.0200000000]) {
								square(center = true, size = [2.0600000000, 0.0100000000]);
							}
						}
						translate(v = [0, -0.6000000000]) {
							translate(v = [0, -0.0200000000]) {
								square(center = true, size = [2.0600000000, 0.0100000000]);
							}
						}
						translate(v = [0, 0.6400000000]) {
							translate(v = [0, -0.0200000000]) {
								square(center = true, size = [2.0600000000, 0.0100000000]);
							}
						}
						translate(v = [0, -0.6400000000]) {
							translate(v = [0, -0.0200000000]) {
								square(center = true, size = [2.0600000000, 0.0100000000]);
							}
						}
						translate(v = [0, 0.6800000000]) {
							translate(v = [0, -0.0200000000]) {
								square(center = true, size = [2.0600000000, 0.0100000000]);
							}
						}
						translate(v = [0, -0.6800000000]) {
							translate(v = [0, -0.0200000000]) {
								square(center = true, size = [2.0600000000, 0.0100000000]);
							}
						}
						translate(v = [0, 0.7200000000]) {
							translate(v = [0, -0.0200000000]) {
								square(center = true, size = [2.0600000000, 0.0100000000]);
							}
						}
						translate(v = [0, -0.7200000000]) {
							translate(v = [0, -0.0200000000]) {
								square(center = true, size = [2.0600000000, 0.0100000000]);
							}
						}
						translate(v = [0, 0.7600000000]) {
							translate(v = [0, -0.0200000000]) {
								square(center = true, size = [2.0600000000, 0.0100000000]);
							}
						}
						translate(v = [0, -0.7600000000]) {
							translate(v = [0, -0.0200000000]) {
								square(center = true, size = [2.0600000000, 0.0100000000]);
							}
						}
						translate(v = [0, 0.8000000000]) {
							translate(v = [0, -0.0200000000]) {
								square(center = true, size = [2.0600000000, 0.0100000000]);
							}
						}
						translate(v = [0, -0.8000000000]) {
							translate(v = [0, -0.0200000000]) {
								square(center = true, size = [2.0600000000, 0.0100000000]);
							}
						}
						translate(v = [0, 0.8400000000]) {
							translate(v = [0, -0.0200000000]) {
								square(center = true, size = [2.0600000000, 0.0100000000]);
							}
						}
						translate(v = [0, -0.8400000000]) {
							translate(v = [0, -0.0200000000]) {
								square(center = true, size = [2.0600000000, 0.0100000000]);
							}
						}
						translate(v = [0, 0.8800000000]) {
							translate(v = [0, -0.0200000000]) {
								square(center = true, size = [2.0600000000, 0.0100000000]);
							}
						}
						translate(v = [0, -0.8800000000]) {
							translate(v = [0, -0.0200000000]) {
								square(center = true, size = [2.0600000000, 0.0100000000]);
							}
						}
						translate(v = [0, 0.9200000000]) {
							translate(v = [0, -0.0200000000]) {
								square(center = true, size = [2.0600000000, 0.0100000000]);
							}
						}
						translate(v = [0, -0.9200000000]) {
							translate(v = [0, -0.0200000000]) {
								square(center = true, size = [2.0600000000, 0.0100000000]);
							}
						}
						translate(v = [0, 0.9600000000]) {
							translate(v = [0, -0.0200000000]) {
								square(center = true, size = [2.0600000000, 0.0100000000]);
							}
						}
						translate(v = [0, -0.9600000000]) {
							translate(v = [0, -0.0200000000]) {
								square(center = true, size = [2.0600000000, 0.0100000000]);
							}
						}
						translate(v = [0, 1.0000000000]) {
							translate(v = [0, -0.0200000000]) {
								square(center = true, size = [2.0600000000, 0.0100000000]);
							}
						}
						translate(v = [0, -1.0000000000]) {
							translate(v = [0, -0.0200000000]) {
								square(center = true, size = [2.0600000000, 0.0100000000]);
							}
						}
						translate(v = [0, 1.0400000000]) {
							translate(v = [0, -0.0200000000]) {
								square(center = true, size = [2.0600000000, 0.0100000000]);
							}
						}
						translate(v = [0, -1.0400000000]) {
							translate(v = [0, -0.0200000000]) {
								square(center = true, size = [2.0600000000, 0.0100000000]);
							}
						}
						translate(v = [0, 1.0800000000]) {
							translate(v = [0, -0.0200000000]) {
								square(center = true, size = [2.0600000000, 0.0100000000]);
							}
						}
						translate(v = [0, -1.0800000000]) {
							translate(v = [0, -0.0200000000]) {
								square(center = true, size = [2.0600000000, 0.0100000000]);
							}
						}
						translate(v = [0, 1.1200000000]) {
							translate(v = [0, -0.0200000000]) {
								square(center = true, size = [2.0600000000, 0.0100000000]);
							}
						}
						translate(v = [0, -1.1200000000]) {
							translate(v = [0, -0.0200000000]) {
								square(center = true, size = [2.0600000000, 0.0100000000]);
							}
						}
						translate(v = [0, 1.1600000000]) {
							translate(v = [0, -0.0200000000]) {
								square(center = true, size = [2.0600000000, 0.0100000000]);
							}
						}
						translate(v = [0, -1.1600000000]) {
							translate(v = [0, -0.0200000000]) {
								square(center = true, size = [2.0600000000, 0.0100000000]);
							}
						}
						translate(v = [0, 1.2000000000]) {
							translate(v = [0, -0.0200000000]) {
								square(center = true, size = [2.0600000000, 0.0100000000]);
							}
						}
						translate(v = [0, -1.2000000000]) {
							translate(v = [0, -0.0200000000]) {
								square(center = true, size = [2.0600000000, 0.0100000000]);
							}
						}
						translate(v = [0, 1.2400000000]) {
							translate(v = [0, -0.0200000000]) {
								square(center = true, size = [2.0600000000, 0.0100000000]);
							}
						}
						translate(v = [0, -1.2400000000]) {
							translate(v = [0, -0.0200000000]) {
								square(center = true, size = [2.0600000000, 0.0100000000]);
							}
						}
						translate(v = [0, 1.2800000000]) {
							translate(v = [0, -0.0200000000]) {
								square(center = true, size = [2.0600000000, 0.0100000000]);
							}
						}
						translate(v = [0, -1.2800000000]) {
							translate(v = [0, -0.0200000000]) {
								square(center = true, size = [2.0600000000, 0.0100000000]);
							}
						}
						translate(v = [0, 1.3200000000]) {
							translate(v = [0, -0.0200000000]) {
								square(center = true, size = [2.0600000000, 0.0100000000]);
							}
						}
						translate(v = [0, -1.3200000000]) {
							translate(v = [0, -0.0200000000]) {
								square(center = true, size = [2.0600000000, 0.0100000000]);
							}
						}
						translate(v = [0, 1.3600000000]) {
							translate(v = [0, -0.0200000000]) {
								square(center = true, size = [2.0600000000, 0.0100000000]);
							}
						}
						translate(v = [0, -1.3600000000]) {
							translate(v = [0, -0.0200000000]) {
								square(center = true, size = [2.0600000000, 0.0100000000]);
							}
						}
						translate(v = [0, 1.4000000000]) {
							translate(v = [0, -0.0200000000]) {
								square(center = true, size = [2.0600000000, 0.0100000000]);
							}
						}
						translate(v = [0, -1.4000000000]) {
							translate(v = [0, -0.0200000000]) {
								square(center = true, size = [2.0600000000, 0.0100000000]);
							}
						}
						translate(v = [0, 1.4400000000]) {
							translate(v = [0, -0.0200000000]) {
								square(center = true, size = [2.0600000000, 0.0100000000]);
							}
						}
						translate(v = [0, -1.4400000000]) {
							translate(v = [0, -0.0200000000]) {
								square(center = true, size = [2.0600000000, 0.0100000000]);
							}
						}
						translate(v = [0, 1.4800000000]) {
							translate(v = [0, -0.0200000000]) {
								square(center = true, size = [2.0600000000, 0.0100000000]);
							}
						}
						translate(v = [0, -1.4800000000]) {
							translate(v = [0, -0.0200000000]) {
								square(center = true, size = [2.0600000000, 0.0100000000]);
							}
						}
						translate(v = [0, 1.5200000000]) {
							translate(v = [0, -0.0200000000]) {
								square(center = true, size = [2.0600000000, 0.0100000000]);
							}
						}
						translate(v = [0, -1.5200000000]) {
							translate(v = [0, -0.0200000000]) {
								square(center = true, size = [2.0600000000, 0.0100000000]);
							}
						}
						translate(v = [0, 1.5600000000]) {
							translate(v = [0, -0.0200000000]) {
								square(center = true, size = [2.0600000000, 0.0100000000]);
							}
						}
						translate(v = [0, -1.5600000000]) {
							translate(v = [0, -0.0200000000]) {
								square(center = true, size = [2.0600000000, 0.0100000000]);
							}
						}
						translate(v = [0, 1.6000000000]) {
							translate(v = [0, -0.0200000000]) {
								square(center = true, size = [2.0600000000, 0.0100000000]);
							}
						}
						translate(v = [0, -1.6000000000]) {
							translate(v = [0, -0.0200000000]) {
								square(center = true, size = [2.0600000000, 0.0100000000]);
							}
						}
						translate(v = [0, 1.6400000000]) {
							translate(v = [0, -0.0200000000]) {
								square(center = true, size = [2.0600000000, 0.0100000000]);
							}
						}
						translate(v = [0, -1.6400000000]) {
							translate(v = [0, -0.0200000000]) {
								square(center = true, size = [2.0600000000, 0.0100000000]);
							}
						}
						translate(v = [0, 1.6800000000]) {
							translate(v = [0, -0.0200000000]) {
								square(center = true, size = [2.0600000000, 0.0100000000]);
							}
						}
						translate(v = [0, -1.6800000000]) {
							translate(v = [0, -0.0200000000]) {
								square(center = true, size = [2.0600000000, 0.0100000000]);
							}
						}
						translate(v = [0, 1.7200000000]) {
							translate(v = [0, -0.0200000000]) {
								square(center = true, size = [2.0600000000, 0.0100000000]);
							}
						}
					}
				}
			}
		}
		translate(v = [18, 0]) {
			translate(v = [9.0000000000, 4.5000000000, 0]) {
				rotate(a = 0) {
					union() {
						translate(v = [0, 0.0000000000]) {
							translate(v = [0, -0.0200000000]) {
								square(center = true, size = [2.0600000000, 0.0100000000]);
							}
						}
						translate(v = [0, 0.0400000000]) {
							translate(v = [0, -0.0200000000]) {
								square(center = true, size = [2.0600000000, 0.0100000000]);
							}
						}
						translate(v = [0, -0.0400000000]) {
							translate(v = [0, -0.0200000000]) {
								square(center = true, size = [2.0600000000, 0.0100000000]);
							}
						}
						translate(v = [0, 0.0800000000]) {
							translate(v = [0, -0.0200000000]) {
								square(center = true, size = [2.0600000000, 0.0100000000]);
							}
						}
						translate(v = [0, -0.0800000000]) {
							translate(v = [0, -0.0200000000]) {
								square(center = true, size = [2.0600000000, 0.0100000000]);
							}
						}
						translate(v = [0, 0.1200000000]) {
							translate(v = [0, -0.0200000000]) {
								square(center = true, size = [2.0600000000, 0.0100000000]);
							}
						}
						translate(v = [0, -0.1200000000]) {
							translate(v = [0, -0.0200000000]) {
								square(center = true, size = [2.0600000000, 0.0100000000]);
							}
						}
						translate(v = [0, 0.1600000000]) {
							translate(v = [0, -0.0200000000]) {
								square(center = true, size = [2.0600000000, 0.0100000000]);
							}
						}
						translate(v = [0, -0.1600000000]) {
							translate(v = [0, -0.0200000000]) {
								square(center = true, size = [2.0600000000, 0.0100000000]);
							}
						}
						translate(v = [0, 0.2000000000]) {
							translate(v = [0, -0.0200000000]) {
								square(center = true, size = [2.0600000000, 0.0100000000]);
							}
						}
						translate(v = [0, -0.2000000000]) {
							translate(v = [0, -0.0200000000]) {
								square(center = true, size = [2.0600000000, 0.0100000000]);
							}
						}
						translate(v = [0, 0.2400000000]) {
							translate(v = [0, -0.0200000000]) {
								square(center = true, size = [2.0600000000, 0.0100000000]);
							}
						}
						translate(v = [0, -0.2400000000]) {
							translate(v = [0, -0.0200000000]) {
								square(center = true, size = [2.0600000000, 0.0100000000]);
							}
						}
						translate(v = [0, 0.2800000000]) {
							translate(v = [0, -0.0200000000]) {
								square(center = true, size = [2.0600000000, 0.0100000000]);
							}
						}
						translate(v = [0, -0.2800000000]) {
							translate(v = [0, -0.0200000000]) {
								square(center = true, size = [2.0600000000, 0.0100000000]);
							}
						}
						translate(v = [0, 0.3200000000]) {
							translate(v = [0, -0.0200000000]) {
								square(center = true, size = [2.0600000000, 0.0100000000]);
							}
						}
						translate(v = [0, -0.3200000000]) {
							translate(v = [0, -0.0200000000]) {
								square(center = true, size = [2.0600000000, 0.0100000000]);
							}
						}
						translate(v = [0, 0.3600000000]) {
							translate(v = [0, -0.0200000000]) {
								square(center = true, size = [2.0600000000, 0.0100000000]);
							}
						}
						translate(v = [0, -0.3600000000]) {
							translate(v = [0, -0.0200000000]) {
								square(center = true, size = [2.0600000000, 0.0100000000]);
							}
						}
						translate(v = [0, 0.4000000000]) {
							translate(v = [0, -0.0200000000]) {
								square(center = true, size = [2.0600000000, 0.0100000000]);
							}
						}
						translate(v = [0, -0.4000000000]) {
							translate(v = [0, -0.0200000000]) {
								square(center = true, size = [2.0600000000, 0.0100000000]);
							}
						}
						translate(v = [0, 0.4400000000]) {
							translate(v = [0, -0.0200000000]) {
								square(center = true, size = [2.0600000000, 0.0100000000]);
							}
						}
						translate(v = [0, -0.4400000000]) {
							translate(v = [0, -0.0200000000]) {
								square(center = true, size = [2.0600000000, 0.0100000000]);
							}
						}
						translate(v = [0, 0.4800000000]) {
							translate(v = [0, -0.0200000000]) {
								square(center = true, size = [2.0600000000, 0.0100000000]);
							}
						}
						translate(v = [0, -0.4800000000]) {
							translate(v = [0, -0.0200000000]) {
								square(center = true, size = [2.0600000000, 0.0100000000]);
							}
						}
						translate(v = [0, 0.5200000000]) {
							translate(v = [0, -0.0200000000]) {
								square(center = true, size = [2.0600000000, 0.0100000000]);
							}
						}
						translate(v = [0, -0.5200000000]) {
							translate(v = [0, -0.0200000000]) {
								square(center = true, size = [2.0600000000, 0.0100000000]);
							}
						}
						translate(v = [0, 0.5600000000]) {
							translate(v = [0, -0.0200000000]) {
								square(center = true, size = [2.0600000000, 0.0100000000]);
							}
						}
						translate(v = [0, -0.5600000000]) {
							translate(v = [0, -0.0200000000]) {
								square(center = true, size = [2.0600000000, 0.0100000000]);
							}
						}
						translate(v = [0, 0.6000000000]) {
							translate(v = [0, -0.0200000000]) {
								square(center = true, size = [2.0600000000, 0.0100000000]);
							}
						}
						translate(v = [0, -0.6000000000]) {
							translate(v = [0, -0.0200000000]) {
								square(center = true, size = [2.0600000000, 0.0100000000]);
							}
						}
						translate(v = [0, 0.6400000000]) {
							translate(v = [0, -0.0200000000]) {
								square(center = true, size = [2.0600000000, 0.0100000000]);
							}
						}
						translate(v = [0, -0.6400000000]) {
							translate(v = [0, -0.0200000000]) {
								square(center = true, size = [2.0600000000, 0.0100000000]);
							}
						}
						translate(v = [0, 0.6800000000]) {
							translate(v = [0, -0.0200000000]) {
								square(center = true, size = [2.0600000000, 0.0100000000]);
							}
						}
						translate(v = [0, -0.6800000000]) {
							translate(v = [0, -0.0200000000]) {
								square(center = true, size = [2.0600000000, 0.0100000000]);
							}
						}
						translate(v = [0, 0.7200000000]) {
							translate(v = [0, -0.0200000000]) {
								square(center = true, size = [2.0600000000, 0.0100000000]);
							}
						}
						translate(v = [0, -0.7200000000]) {
							translate(v = [0, -0.0200000000]) {
								square(center = true, size = [2.0600000000, 0.0100000000]);
							}
						}
						translate(v = [0, 0.7600000000]) {
							translate(v = [0, -0.0200000000]) {
								square(center = true, size = [2.0600000000, 0.0100000000]);
							}
						}
						translate(v = [0, -0.7600000000]) {
							translate(v = [0, -0.0200000000]) {
								square(center = true, size = [2.0600000000, 0.0100000000]);
							}
						}
						translate(v = [0, 0.8000000000]) {
							translate(v = [0, -0.0200000000]) {
								square(center = true, size = [2.0600000000, 0.0100000000]);
							}
						}
						translate(v = [0, -0.8000000000]) {
							translate(v = [0, -0.0200000000]) {
								square(center = true, size = [2.0600000000, 0.0100000000]);
							}
						}
						translate(v = [0, 0.8400000000]) {
							translate(v = [0, -0.0200000000]) {
								square(center = true, size = [2.0600000000, 0.0100000000]);
							}
						}
						translate(v = [0, -0.8400000000]) {
							translate(v = [0, -0.0200000000]) {
								square(center = true, size = [2.0600000000, 0.0100000000]);
							}
						}
						translate(v = [0, 0.8800000000]) {
							translate(v = [0, -0.0200000000]) {
								square(center = true, size = [2.0600000000, 0.0100000000]);
							}
						}
						translate(v = [0, -0.8800000000]) {
							translate(v = [0, -0.0200000000]) {
								square(center = true, size = [2.0600000000, 0.0100000000]);
							}
						}
						translate(v = [0, 0.9200000000]) {
							translate(v = [0, -0.0200000000]) {
								square(center = true, size = [2.0600000000, 0.0100000000]);
							}
						}
						translate(v = [0, -0.9200000000]) {
							translate(v = [0, -0.0200000000]) {
								square(center = true, size = [2.0600000000, 0.0100000000]);
							}
						}
						translate(v = [0, 0.9600000000]) {
							translate(v = [0, -0.0200000000]) {
								square(center = true, size = [2.0600000000, 0.0100000000]);
							}
						}
						translate(v = [0, -0.9600000000]) {
							translate(v = [0, -0.0200000000]) {
								square(center = true, size = [2.0600000000, 0.0100000000]);
							}
						}
						translate(v = [0, 1.0000000000]) {
							translate(v = [0, -0.0200000000]) {
								square(center = true, size = [2.0600000000, 0.0100000000]);
							}
						}
						translate(v = [0, -1.0000000000]) {
							translate(v = [0, -0.0200000000]) {
								square(center = true, size = [2.0600000000, 0.0100000000]);
							}
						}
						translate(v = [0, 1.0400000000]) {
							translate(v = [0, -0.0200000000]) {
								square(center = true, size = [2.0600000000, 0.0100000000]);
							}
						}
						translate(v = [0, -1.0400000000]) {
							translate(v = [0, -0.0200000000]) {
								square(center = true, size = [2.0600000000, 0.0100000000]);
							}
						}
						translate(v = [0, 1.0800000000]) {
							translate(v = [0, -0.0200000000]) {
								square(center = true, size = [2.0600000000, 0.0100000000]);
							}
						}
						translate(v = [0, -1.0800000000]) {
							translate(v = [0, -0.0200000000]) {
								square(center = true, size = [2.0600000000, 0.0100000000]);
							}
						}
						translate(v = [0, 1.1200000000]) {
							translate(v = [0, -0.0200000000]) {
								square(center = true, size = [2.0600000000, 0.0100000000]);
							}
						}
						translate(v = [0, -1.1200000000]) {
							translate(v = [0, -0.0200000000]) {
								square(center = true, size = [2.0600000000, 0.0100000000]);
							}
						}
						translate(v = [0, 1.1600000000]) {
							translate(v = [0, -0.0200000000]) {
								square(center = true, size = [2.0600000000, 0.0100000000]);
							}
						}
						translate(v = [0, -1.1600000000]) {
							translate(v = [0, -0.0200000000]) {
								square(center = true, size = [2.0600000000, 0.0100000000]);
							}
						}
						translate(v = [0, 1.2000000000]) {
							translate(v = [0, -0.0200000000]) {
								square(center = true, size = [2.0600000000, 0.0100000000]);
							}
						}
						translate(v = [0, -1.2000000000]) {
							translate(v = [0, -0.0200000000]) {
								square(center = true, size = [2.0600000000, 0.0100000000]);
							}
						}
						translate(v = [0, 1.2400000000]) {
							translate(v = [0, -0.0200000000]) {
								square(center = true, size = [2.0600000000, 0.0100000000]);
							}
						}
						translate(v = [0, -1.2400000000]) {
							translate(v = [0, -0.0200000000]) {
								square(center = true, size = [2.0600000000, 0.0100000000]);
							}
						}
						translate(v = [0, 1.2800000000]) {
							translate(v = [0, -0.0200000000]) {
								square(center = true, size = [2.0600000000, 0.0100000000]);
							}
						}
						translate(v = [0, -1.2800000000]) {
							translate(v = [0, -0.0200000000]) {
								square(center = true, size = [2.0600000000, 0.0100000000]);
							}
						}
						translate(v = [0, 1.3200000000]) {
							translate(v = [0, -0.0200000000]) {
								square(center = true, size = [2.0600000000, 0.0100000000]);
							}
						}
						translate(v = [0, -1.3200000000]) {
							translate(v = [0, -0.0200000000]) {
								square(center = true, size = [2.0600000000, 0.0100000000]);
							}
						}
						translate(v = [0, 1.3600000000]) {
							translate(v = [0, -0.0200000000]) {
								square(center = true, size = [2.0600000000, 0.0100000000]);
							}
						}
						translate(v = [0, -1.3600000000]) {
							translate(v = [0, -0.0200000000]) {
								square(center = true, size = [2.0600000000, 0.0100000000]);
							}
						}
						translate(v = [0, 1.4000000000]) {
							translate(v = [0, -0.0200000000]) {
								square(center = true, size = [2.0600000000, 0.0100000000]);
							}
						}
						translate(v = [0, -1.4000000000]) {
							translate(v = [0, -0.0200000000]) {
								square(center = true, size = [2.0600000000, 0.0100000000]);
							}
						}
						translate(v = [0, 1.4400000000]) {
							translate(v = [0, -0.0200000000]) {
								square(center = true, size = [2.0600000000, 0.0100000000]);
							}
						}
						translate(v = [0, -1.4400000000]) {
							translate(v = [0, -0.0200000000]) {
								square(center = true, size = [2.0600000000, 0.0100000000]);
							}
						}
						translate(v = [0, 1.4800000000]) {
							translate(v = [0, -0.0200000000]) {
								square(center = true, size = [2.0600000000, 0.0100000000]);
							}
						}
						translate(v = [0, -1.4800000000]) {
							translate(v = [0, -0.0200000000]) {
								square(center = true, size = [2.0600000000, 0.0100000000]);
							}
						}
						translate(v = [0, 1.5200000000]) {
							translate(v = [0, -0.0200000000]) {
								square(center = true, size = [2.0600000000, 0.0100000000]);
							}
						}
						translate(v = [0, -1.5200000000]) {
							translate(v = [0, -0.0200000000]) {
								square(center = true, size = [2.0600000000, 0.0100000000]);
							}
						}
						translate(v = [0, 1.5600000000]) {
							translate(v = [0, -0.0200000000]) {
								square(center = true, size = [2.0600000000, 0.0100000000]);
							}
						}
						translate(v = [0, -1.5600000000]) {
							translate(v = [0, -0.0200000000]) {
								square(center = true, size = [2.0600000000, 0.0100000000]);
							}
						}
						translate(v = [0, 1.6000000000]) {
							translate(v = [0, -0.0200000000]) {
								square(center = true, size = [2.0600000000, 0.0100000000]);
							}
						}
						translate(v = [0, -1.6000000000]) {
							translate(v = [0, -0.0200000000]) {
								square(center = true, size = [2.0600000000, 0.0100000000]);
							}
						}
						translate(v = [0, 1.6400000000]) {
							translate(v = [0, -0.0200000000]) {
								square(center = true, size = [2.0600000000, 0.0100000000]);
							}
						}
						translate(v = [0, -1.6400000000]) {
							translate(v = [0, -0.0200000000]) {
								square(center = true, size = [2.0600000000, 0.0100000000]);
							}
						}
						translate(v = [0, 1.6800000000]) {
							translate(v = [0, -0.0200000000]) {
								square(center = true, size = [2.0600000000, 0.0100000000]);
							}
						}
						translate(v = [0, -1.6800000000]) {
							translate(v = [0, -0.0200000000]) {
								square(center = true, size = [2.0600000000, 0.0100000000]);
							}
						}
						translate(v = [0, 1.7200000000]) {
							translate(v = [0, -0.0200000000]) {
								square(center = true, size = [2.0600000000, 0.0100000000]);
							}
						}
					}
				}
			}
		}
		translate(v = [36, 0]) {
			translate(v = [9.0000000000, 4.5000000000, 0]) {
				rotate(a = 0) {
					union() {
						translate(v = [0, 0.0000000000]) {
							translate(v = [0, -0.0200000000]) {
								square(center = true, size = [2.0600000000, 0.0100000000]);
							}
						}
						translate(v = [0, 0.0400000000]) {
							translate(v = [0, -0.0200000000]) {
								square(center = true, size = [2.0600000000, 0.0100000000]);
							}
						}
						translate(v = [0, -0.0400000000]) {
							translate(v = [0, -0.0200000000]) {
								square(center = true, size = [2.0600000000, 0.0100000000]);
							}
						}
						translate(v = [0, 0.0800000000]) {
							translate(v = [0, -0.0200000000]) {
								square(center = true, size = [2.0600000000, 0.0100000000]);
							}
						}
						translate(v = [0, -0.0800000000]) {
							translate(v = [0, -0.0200000000]) {
								square(center = true, size = [2.0600000000, 0.0100000000]);
							}
						}
						translate(v = [0, 0.1200000000]) {
							translate(v = [0, -0.0200000000]) {
								square(center = true, size = [2.0600000000, 0.0100000000]);
							}
						}
						translate(v = [0, -0.1200000000]) {
							translate(v = [0, -0.0200000000]) {
								square(center = true, size = [2.0600000000, 0.0100000000]);
							}
						}
						translate(v = [0, 0.1600000000]) {
							translate(v = [0, -0.0200000000]) {
								square(center = true, size = [2.0600000000, 0.0100000000]);
							}
						}
						translate(v = [0, -0.1600000000]) {
							translate(v = [0, -0.0200000000]) {
								square(center = true, size = [2.0600000000, 0.0100000000]);
							}
						}
						translate(v = [0, 0.2000000000]) {
							translate(v = [0, -0.0200000000]) {
								square(center = true, size = [2.0600000000, 0.0100000000]);
							}
						}
						translate(v = [0, -0.2000000000]) {
							translate(v = [0, -0.0200000000]) {
								square(center = true, size = [2.0600000000, 0.0100000000]);
							}
						}
						translate(v = [0, 0.2400000000]) {
							translate(v = [0, -0.0200000000]) {
								square(center = true, size = [2.0600000000, 0.0100000000]);
							}
						}
						translate(v = [0, -0.2400000000]) {
							translate(v = [0, -0.0200000000]) {
								square(center = true, size = [2.0600000000, 0.0100000000]);
							}
						}
						translate(v = [0, 0.2800000000]) {
							translate(v = [0, -0.0200000000]) {
								square(center = true, size = [2.0600000000, 0.0100000000]);
							}
						}
						translate(v = [0, -0.2800000000]) {
							translate(v = [0, -0.0200000000]) {
								square(center = true, size = [2.0600000000, 0.0100000000]);
							}
						}
						translate(v = [0, 0.3200000000]) {
							translate(v = [0, -0.0200000000]) {
								square(center = true, size = [2.0600000000, 0.0100000000]);
							}
						}
						translate(v = [0, -0.3200000000]) {
							translate(v = [0, -0.0200000000]) {
								square(center = true, size = [2.0600000000, 0.0100000000]);
							}
						}
						translate(v = [0, 0.3600000000]) {
							translate(v = [0, -0.0200000000]) {
								square(center = true, size = [2.0600000000, 0.0100000000]);
							}
						}
						translate(v = [0, -0.3600000000]) {
							translate(v = [0, -0.0200000000]) {
								square(center = true, size = [2.0600000000, 0.0100000000]);
							}
						}
						translate(v = [0, 0.4000000000]) {
							translate(v = [0, -0.0200000000]) {
								square(center = true, size = [2.0600000000, 0.0100000000]);
							}
						}
						translate(v = [0, -0.4000000000]) {
							translate(v = [0, -0.0200000000]) {
								square(center = true, size = [2.0600000000, 0.0100000000]);
							}
						}
						translate(v = [0, 0.4400000000]) {
							translate(v = [0, -0.0200000000]) {
								square(center = true, size = [2.0600000000, 0.0100000000]);
							}
						}
						translate(v = [0, -0.4400000000]) {
							translate(v = [0, -0.0200000000]) {
								square(center = true, size = [2.0600000000, 0.0100000000]);
							}
						}
						translate(v = [0, 0.4800000000]) {
							translate(v = [0, -0.0200000000]) {
								square(center = true, size = [2.0600000000, 0.0100000000]);
							}
						}
						translate(v = [0, -0.4800000000]) {
							translate(v = [0, -0.0200000000]) {
								square(center = true, size = [2.0600000000, 0.0100000000]);
							}
						}
						translate(v = [0, 0.5200000000]) {
							translate(v = [0, -0.0200000000]) {
								square(center = true, size = [2.0600000000, 0.0100000000]);
							}
						}
						translate(v = [0, -0.5200000000]) {
							translate(v = [0, -0.0200000000]) {
								square(center = true, size = [2.0600000000, 0.0100000000]);
							}
						}
						translate(v = [0, 0.5600000000]) {
							translate(v = [0, -0.0200000000]) {
								square(center = true, size = [2.0600000000, 0.0100000000]);
							}
						}
						translate(v = [0, -0.5600000000]) {
							translate(v = [0, -0.0200000000]) {
								square(center = true, size = [2.0600000000, 0.0100000000]);
							}
						}
						translate(v = [0, 0.6000000000]) {
							translate(v = [0, -0.0200000000]) {
								square(center = true, size = [2.0600000000, 0.0100000000]);
							}
						}
						translate(v = [0, -0.6000000000]) {
							translate(v = [0, -0.0200000000]) {
								square(center = true, size = [2.0600000000, 0.0100000000]);
							}
						}
						translate(v = [0, 0.6400000000]) {
							translate(v = [0, -0.0200000000]) {
								square(center = true, size = [2.0600000000, 0.0100000000]);
							}
						}
						translate(v = [0, -0.6400000000]) {
							translate(v = [0, -0.0200000000]) {
								square(center = true, size = [2.0600000000, 0.0100000000]);
							}
						}
						translate(v = [0, 0.6800000000]) {
							translate(v = [0, -0.0200000000]) {
								square(center = true, size = [2.0600000000, 0.0100000000]);
							}
						}
						translate(v = [0, -0.6800000000]) {
							translate(v = [0, -0.0200000000]) {
								square(center = true, size = [2.0600000000, 0.0100000000]);
							}
						}
						translate(v = [0, 0.7200000000]) {
							translate(v = [0, -0.0200000000]) {
								square(center = true, size = [2.0600000000, 0.0100000000]);
							}
						}
						translate(v = [0, -0.7200000000]) {
							translate(v = [0, -0.0200000000]) {
								square(center = true, size = [2.0600000000, 0.0100000000]);
							}
						}
						translate(v = [0, 0.7600000000]) {
							translate(v = [0, -0.0200000000]) {
								square(center = true, size = [2.0600000000, 0.0100000000]);
							}
						}
						translate(v = [0, -0.7600000000]) {
							translate(v = [0, -0.0200000000]) {
								square(center = true, size = [2.0600000000, 0.0100000000]);
							}
						}
						translate(v = [0, 0.8000000000]) {
							translate(v = [0, -0.0200000000]) {
								square(center = true, size = [2.0600000000, 0.0100000000]);
							}
						}
						translate(v = [0, -0.8000000000]) {
							translate(v = [0, -0.0200000000]) {
								square(center = true, size = [2.0600000000, 0.0100000000]);
							}
						}
						translate(v = [0, 0.8400000000]) {
							translate(v = [0, -0.0200000000]) {
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
