trissim/OpenMFD/papers/mfd_platform/supplementary/Supplementary_Table_S6_FDM_frame_printing_settings.md

# Supplementary Table S6. HIPS frame-printing settings

These settings were used to print the frame generated by OpenMFD. The complete
Creality Print 6.0.4 configuration is
embedded in the distributed G-code file
`UPGRADE_96_well_plate_reservoirs_print_hips_2_chamfered_v2_HIPS_3h36m.gcode`.
When using other printers, slicers, or materials, check for warping, correct fit,
an unbroken adhesive groove, and a leak-tight seal around the device.

| Parameter | Setting |
|---|---|
| Printer | Creality K1C, enclosed |
| Slicer | Creality Print 6.0.4.1795 |
| Filament | Generic HIPS, 1.75 mm diameter |
| Nozzle | 0.4 mm brass |
| Layer height | 0.20 mm |
| First-layer height | 0.20 mm |
| Nozzle temperature | 220°C, first and subsequent layers |
| Build-plate temperature | 100°C, first and subsequent layers |
| Part cooling | Disabled |
| Wall loops | 2 |
| Top layers | 5 (0.8 mm) |
| Bottom layers | 3 |
| Sparse infill | 15% grid |
| Supports | Disabled |
| Build-plate adhesion | 5 mm outer brim, 0 mm object gap |
| Outer-wall speed | 200 mm/s |
| Inner-wall speed | 300 mm/s |
| Sparse-infill speed | 270 mm/s |
| Top-surface speed | 200 mm/s |
| Initial-layer speed | 60 mm/s |
| Travel speed | 500 mm/s |
| Maximum filament volumetric speed | 5 mm³/s |
| Printed height / layer count | 17.0 mm / 85 layers |
