trissim/OpenMFD/papers/mfd_platform/tmp_pdftext/milimeter_thick_su-8_casting_3d_print_Tamura_2019_Jpn._J._Appl._Phys._58_SDDL10_p1.txt

Japanese Journal of Applied
Physics

You may also like

REGULAR PAPER

Seamless fabrication technique for micro to
millimeter structures by combining 3D printing and
photolithography
To cite this article: Takahiro Tamura and Takaaki Suzuki 2019 Jpn. J. Appl. Phys. 58 SDDL10

- Microfluidic viscometers for biochemical
and biomedical applications: A review
S B Puneeth, Madhusudan B Kulkarni and
Sanket Goel
- Hard magnetics and soft materials—a
synergy
P Narayanan, R Pramanik and A
Arockiarajan
- Organic photodiodes: printing, coating,
benchmarks, and applications
Noah Strobel, Mervin Seiberlich, Ralph
Eckstein et al.

View the article online for updates and enhancements.

This content was downloaded from IP address 24.231.98.89 on 15/08/2024 at 22:43
