trissim/OpenMFD/papers/mfd_platform/tmp_pdftext/steel_3d_print_myelination_Ristola_2019_J._Micromech._Microeng._29_065009_p1.txt

Journal of Micromechanics and
Microengineering

You may also like

PAPER • OPEN ACCESS

A compartmentalized neuron-oligodendrocyte coculture device for myelin research: design,
fabrication and functionality testing
To cite this article: Mervi Ristola et al 2019 J. Micromech. Microeng. 29 065009

- Biomimetic hydrogels direct spinal
progenitor cell differentiation and promote
functional recovery after spinal cord injury
Sydney A Geissler, Alexandra L Sabin,
Rachel R Besser et al.
- Advances in electroactive bioscaffolds for
repairing spinal cord injury
Zeqi Liu, Jiahui Lai, Dexin Kong et al.
- Advances in 3D printing scaffolds for
peripheral nerve and spinal cord injury
repair
Juqing Song, Baiheng Lv, Wencong Chen
et al.

View the article online for updates and enhancements.

This content was downloaded from IP address 24.231.98.89 on 15/08/2024 at 22:04
