trissim/OpenMFD/papers/mfd_platform/figures/final_drop/Fig1_openmfd_design/assembled_device_photo.png

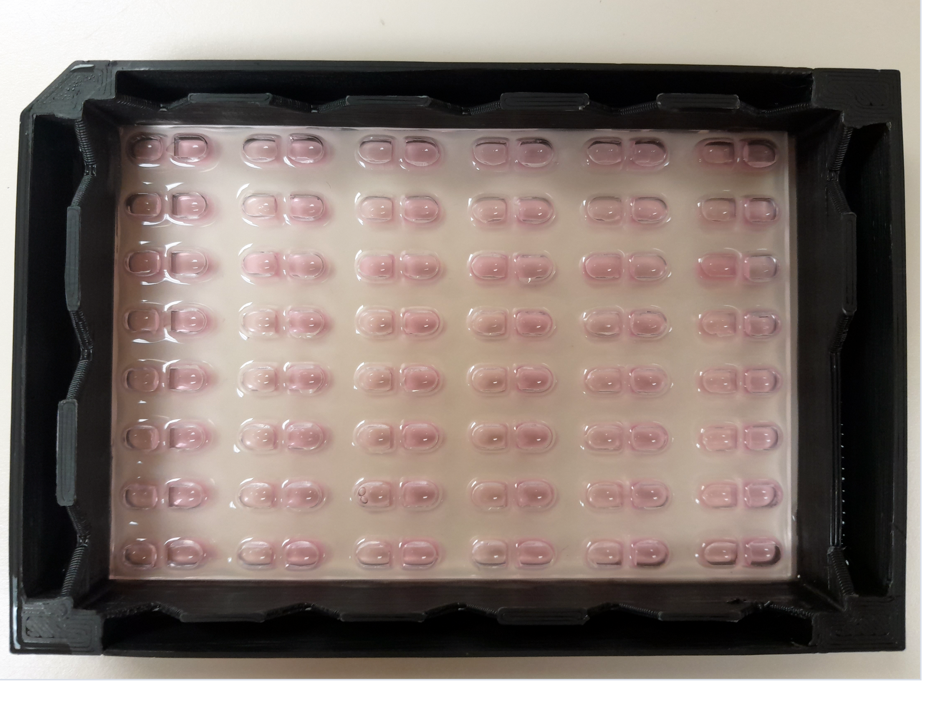
papers/mfd_platform/figures/final_drop/Fig1_openmfd_design/assembled_device_photo.png
