trissim/OpenMFD/papers/mfd_platform/figures/final_drop/Fig3_bonding_fixture/clamp_assembly.jpg

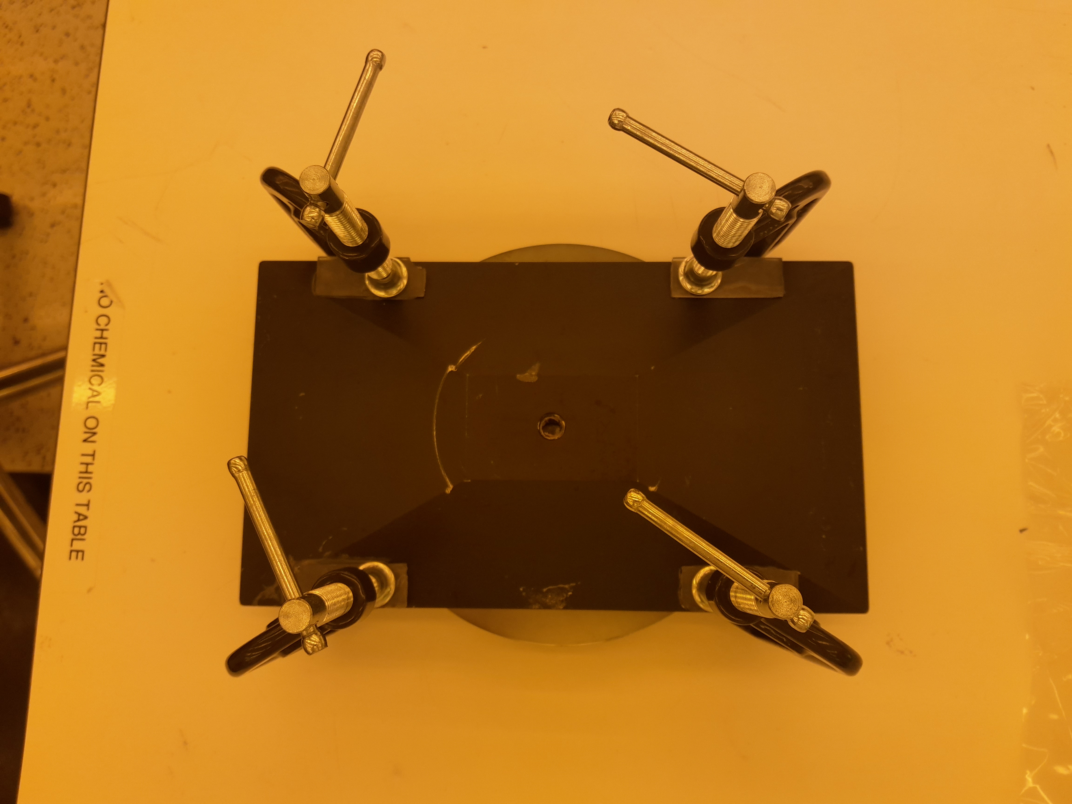
papers/mfd_platform/figures/final_drop/Fig3_bonding_fixture/clamp_assembly.jpg
