trissim/OpenMFD/papers/mfd_platform/figures/rendered/validation.pdf

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

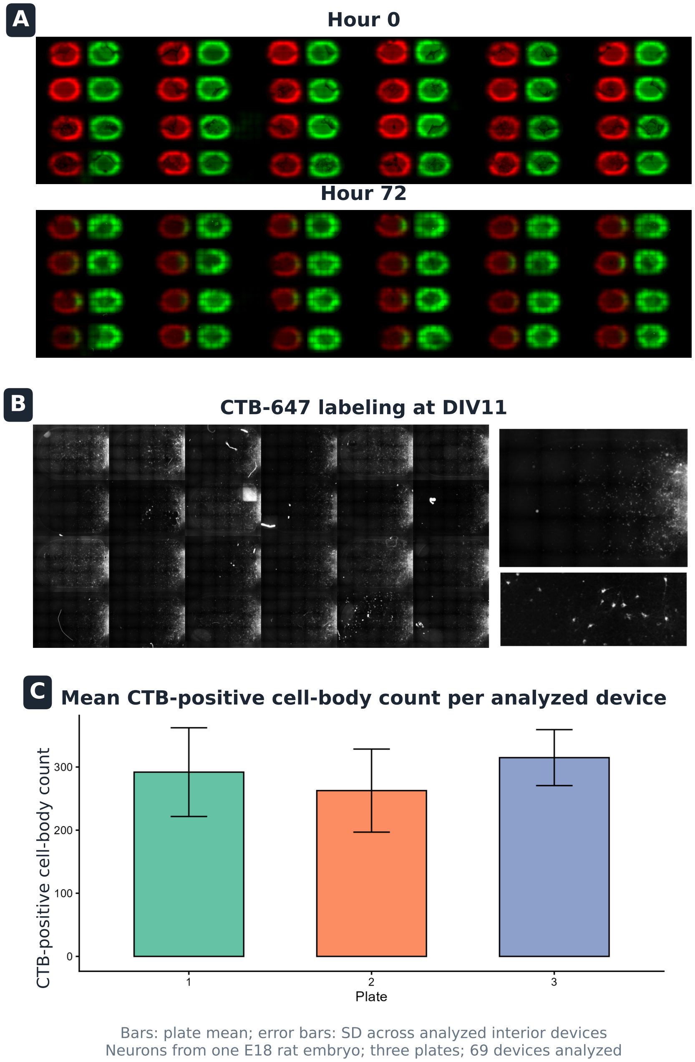
[picture p221: page 1]
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
