trissim/OpenMFD/papers/mfd_platform/figures/final_drop/Fig5_plate_layout_validation/fluorescence_microscopy.pdf

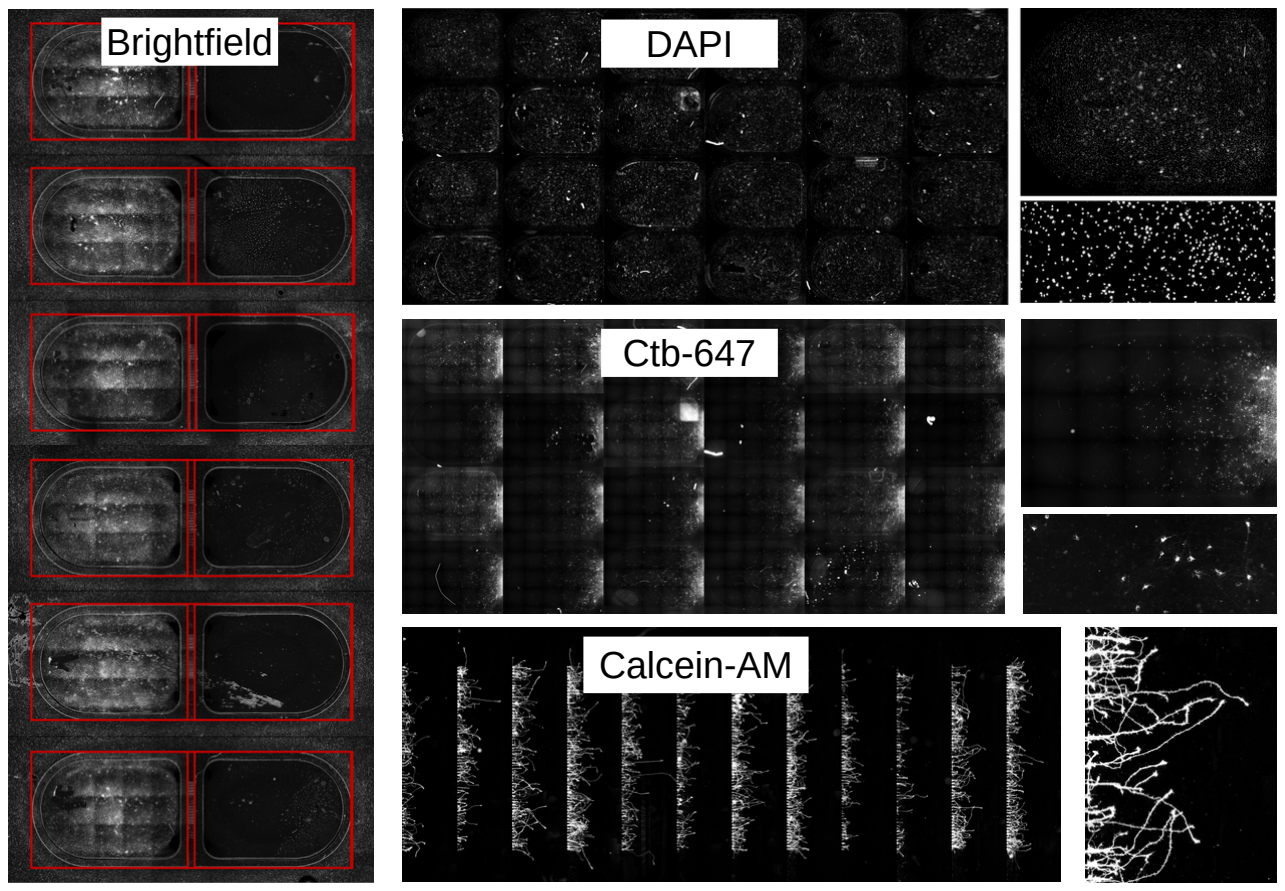
[picture p222: page 1]

Brightfield | DAPI

Ctb-647

Calcein-AM
