trissim/OpenMFD/papers/mfd_platform/figures/drafts/testing/calcein_am_axon.png

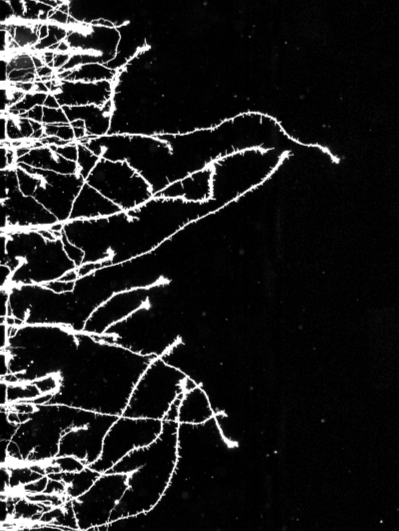
papers/mfd_platform/figures/drafts/testing/calcein_am_axon.png
