trissim/OpenMFD/papers/mfd_platform/figures/drafts/testing/calcein_am_axon_mosaic.png

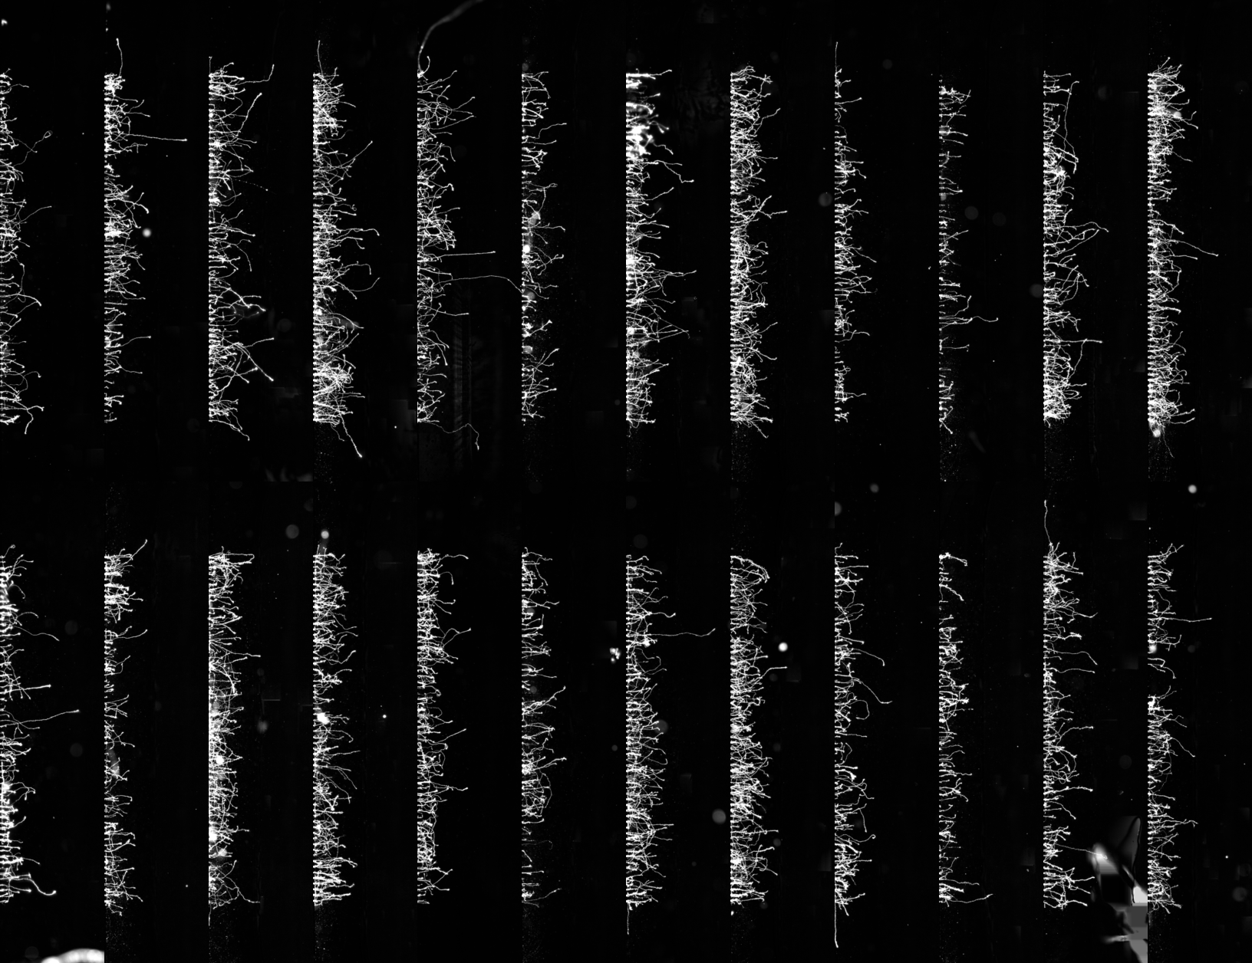
papers/mfd_platform/figures/drafts/testing/calcein_am_axon_mosaic.png
