trissim/OpenMFD/papers/mfd_platform/figures/drafts/testing/representative-ctb1.jpg

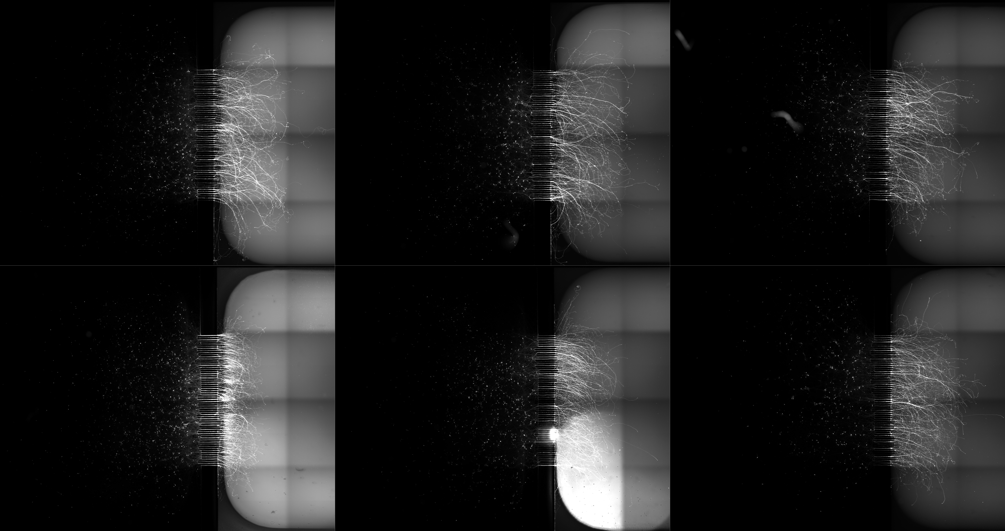
papers/mfd_platform/figures/drafts/testing/representative-ctb1.jpg
