trissim/OpenMFD/papers/mfd_platform/figures/drafts/testing/representative-ctb2.jpg

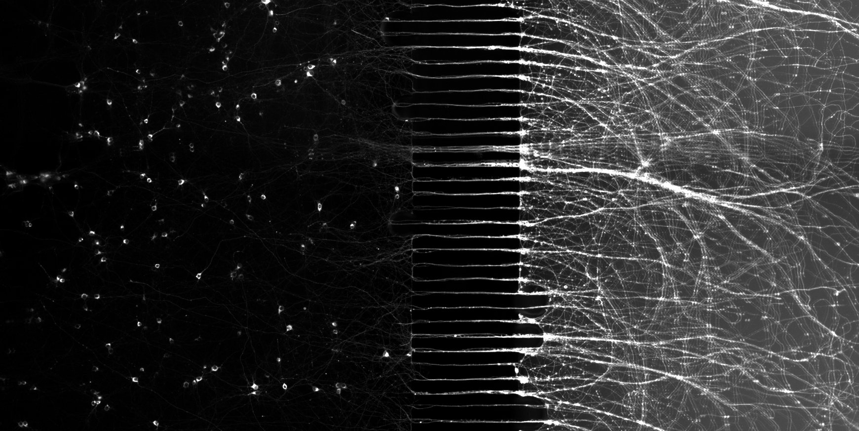
papers/mfd_platform/figures/drafts/testing/representative-ctb2.jpg
