trissim/OpenMFD/papers/mfd_platform/figures/drafts/testing/representative-ctb3.jpg

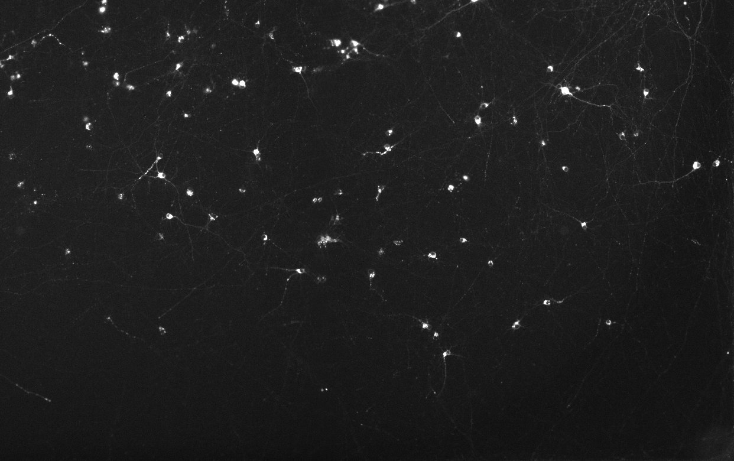
papers/mfd_platform/figures/drafts/testing/representative-ctb3.jpg
