trissim/OpenMFD/papers/mfd_platform/figures/final_drop/Fig5_plate_layout_validation/dapi_tile.png

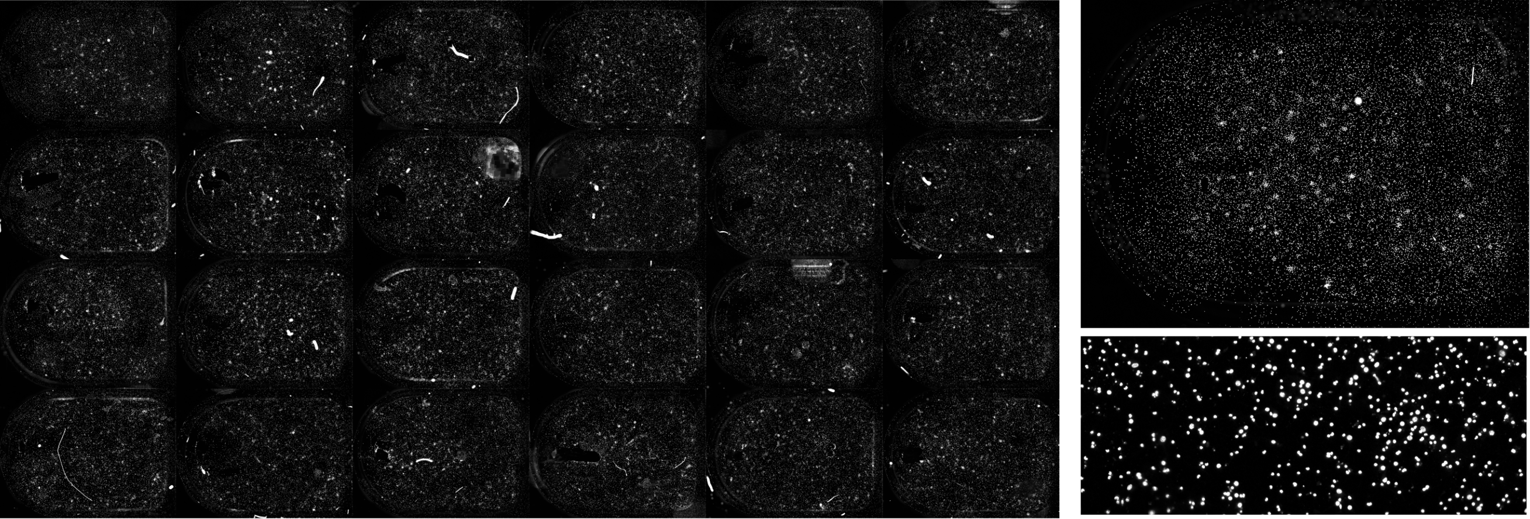
papers/mfd_platform/figures/final_drop/Fig5_plate_layout_validation/dapi_tile.png
