trissim/OpenMFD/papers/mfd_platform/figures/final_drop/Fig5_plate_layout_validation/plate_bar_var_Cell_Before.png

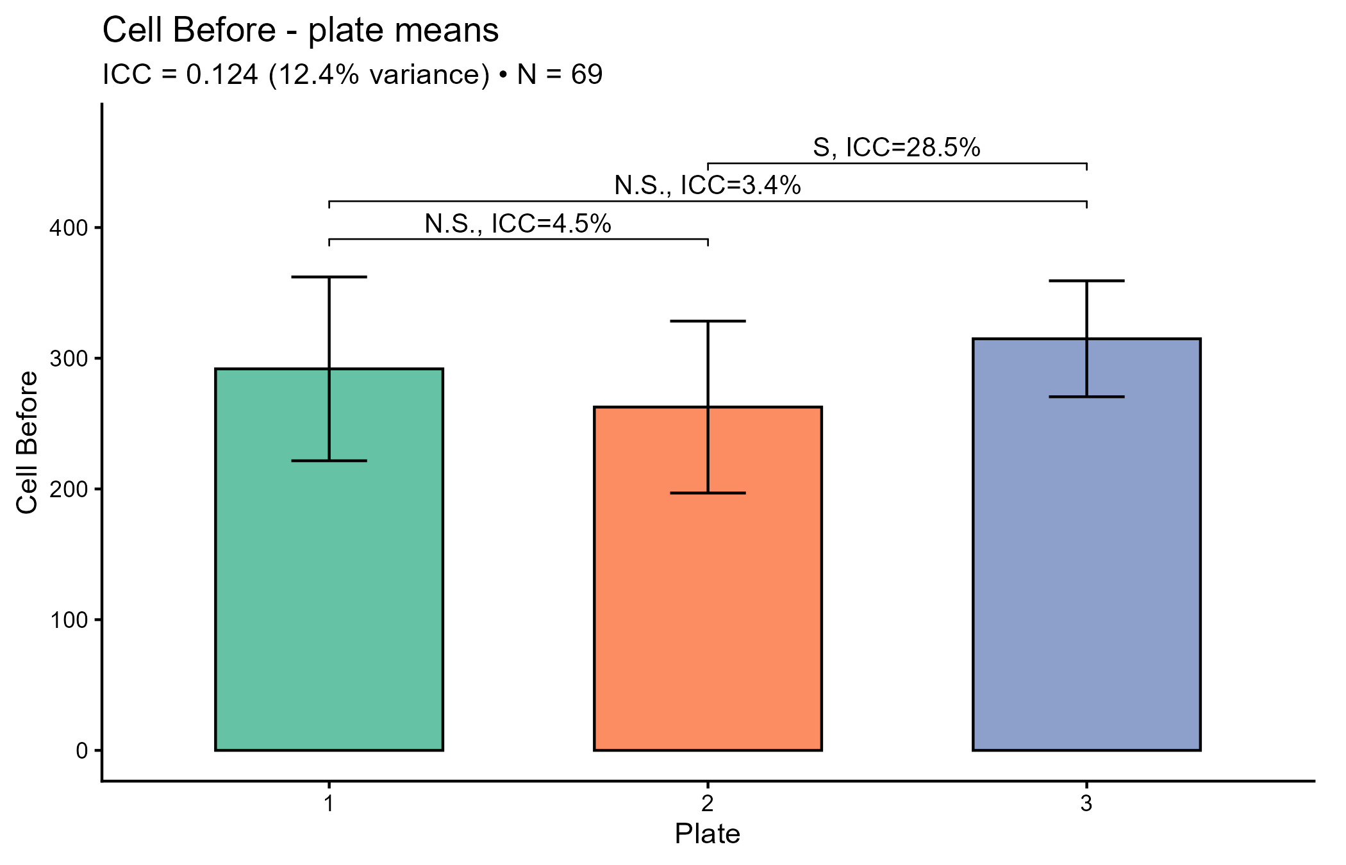
papers/mfd_platform/figures/final_drop/Fig5_plate_layout_validation/plate_bar_var_Cell_Before.png
