trissim/OpenMFD/papers/mfd_platform/figures/comparisons/v25_vs_v27/2_compartment_96_well_300um_v25_vs_v27.pdf

2-compartment 96-well 300 um comparison: v25 vs v27 v25 (suex100) | v27 (suex200)

# Full aligned layout

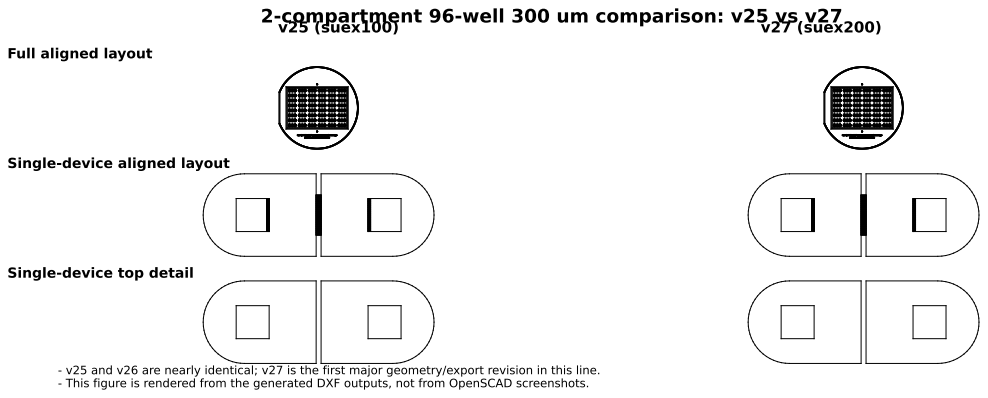
[picture p233: page 1]

Single-device aligned layout

Single-device top detail

- v25 and v26 are nearly identical; v27 is the first major geometry/export revision in this line.
- This figure is rendered from the generated DXF outputs, not from OpenSCAD screenshots.
