trissim/OpenMFD/papers/mfd_platform/figures/final_drop/Supp_FigS1_noLP360/SUEX.jpg

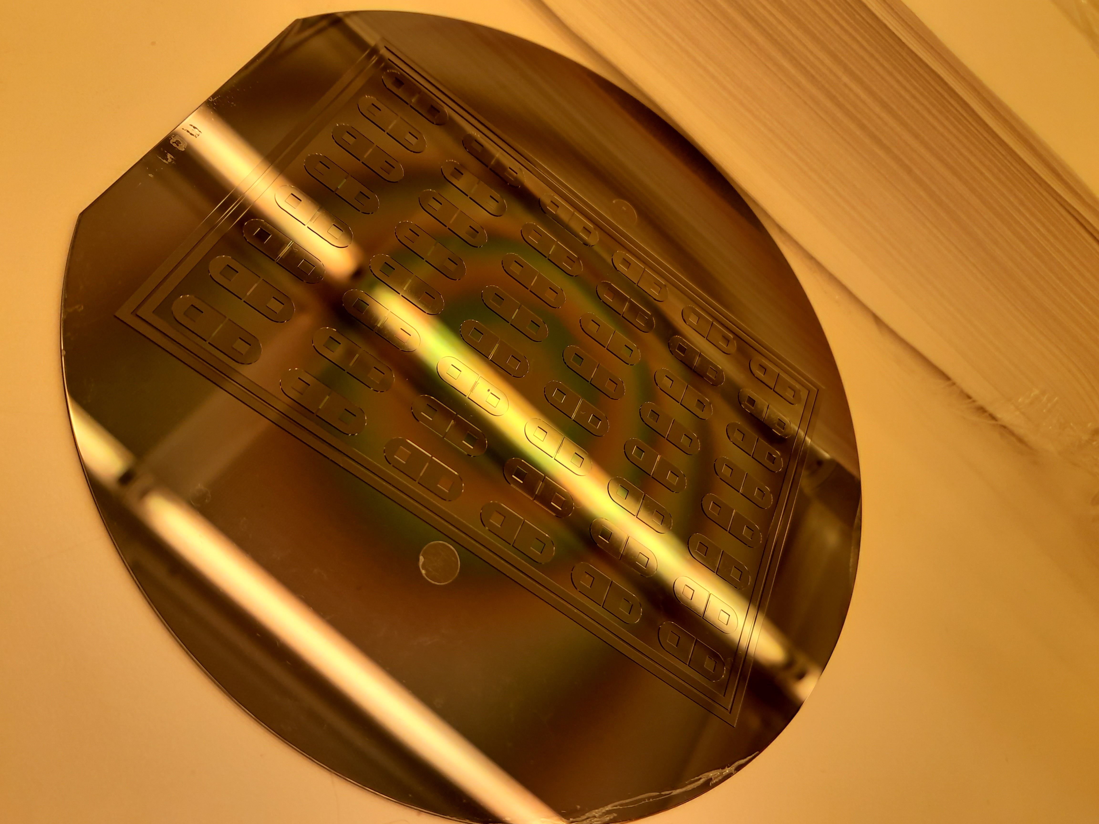
papers/mfd_platform/figures/final_drop/Supp_FigS1_noLP360/SUEX.jpg
